BigPappy098/Satellite1-Ultra/reports/drawings/bottom_service_plate.pdf

# Satellite1 Ultra — bottom_service_plate

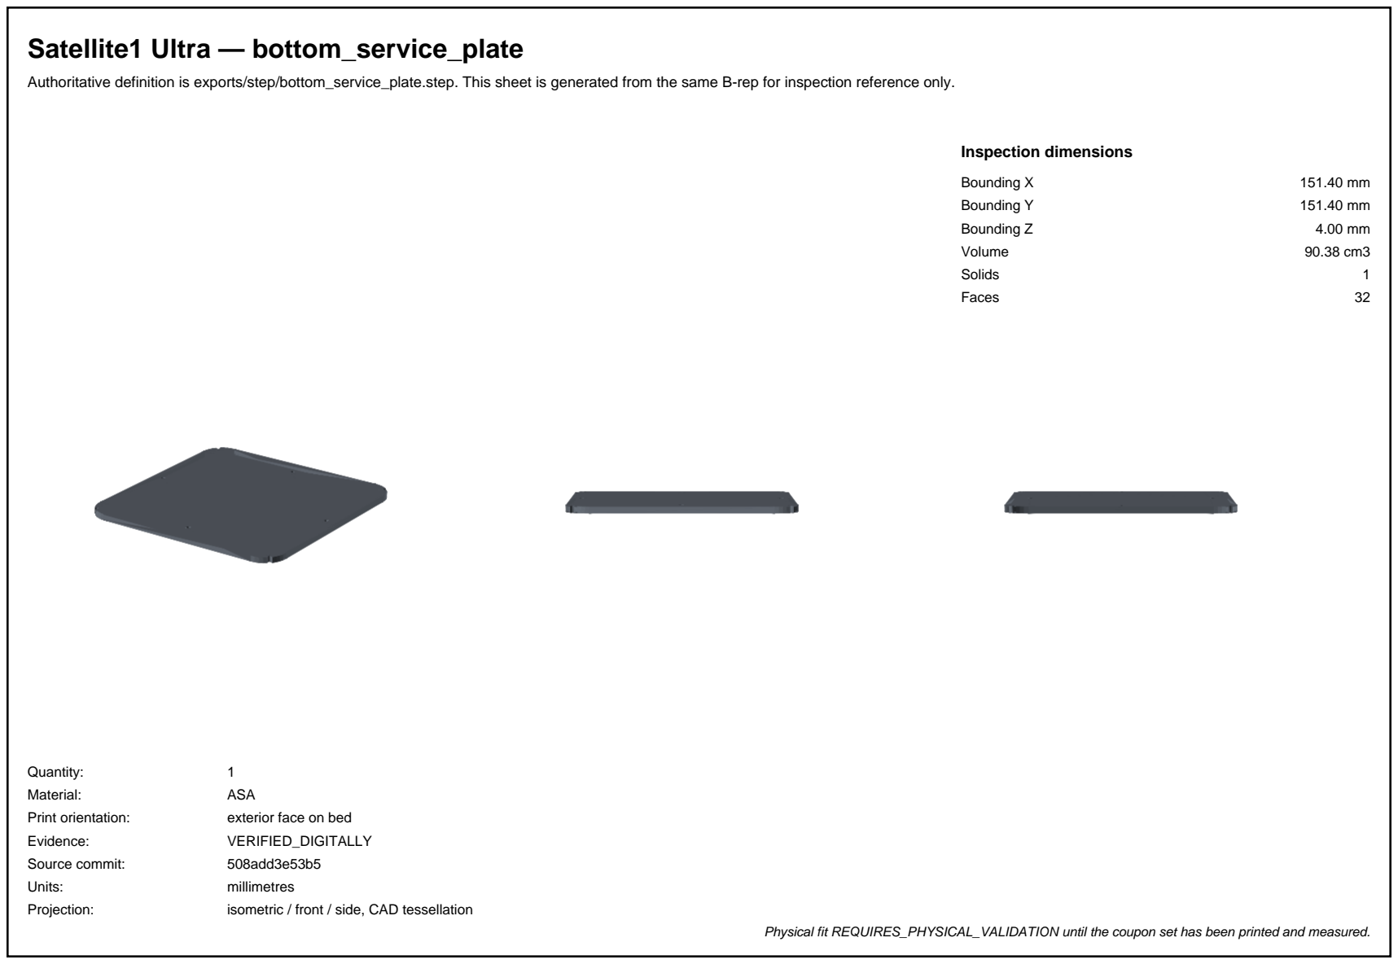
[picture p7: page 1]

Authoritative definition is exports/step/bottom_service_plate.step. This sheet is generated from the same B-rep for inspection reference only.

Inspection dimensions

Bounding X | 151.40 mm
Bounding Y | 151.40 mm
Bounding Z | 4.00 mm
Volume | 90.38 cm3
Solids | 1
Faces | 32
Quantity: | 1
Material: | ASA
Print orientation: | exterior face on bed
Evidence: | VERIFIED_DIGITALLY
Source commit: | 508add3e53b5
Units: | millimetres
Projection: | isometric / front / side, CAD tessellation
Physical fit REQUIRES_PHYSICAL_VALIDATION until the coupon set has been printed and measured.
