BigPappy098/Satellite1-Ultra/reports/drawings/cable_gland.pdf

# Satellite1 Ultra — cable_gland

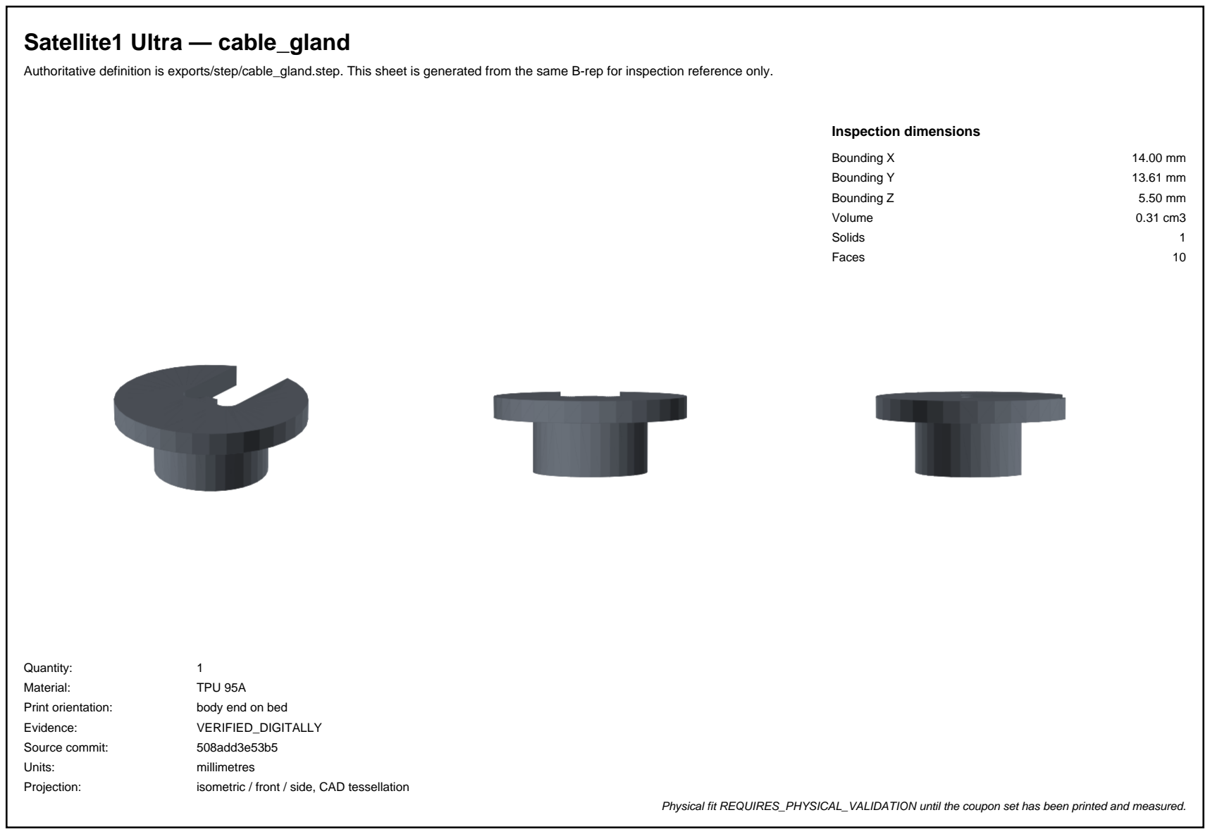
[picture p8: page 1]

Authoritative definition is exports/step/cable_gland.step. This sheet is generated from the same B-rep for inspection reference only.

Inspection dimensions

Bounding X | 14.00 mm
Bounding Y | 13.61 mm
Bounding Z | 5.50 mm
Volume | 0.31 cm3
Solids | 1
Faces | 10
Quantity: | 1
Material: | TPU 95A
Print orientation: | body end on bed
Evidence: | VERIFIED_DIGITALLY
Source commit: | 508add3e53b5
Units: | millimetres
Projection: | isometric / front / side, CAD tessellation
Physical fit REQUIRES_PHYSICAL_VALIDATION until the coupon set has been printed and measured.
