BigPappy098/Satellite1-Ultra/reports/drawings/coupon_active_driver.pdf

# Satellite1 Ultra — coupon_active_driver

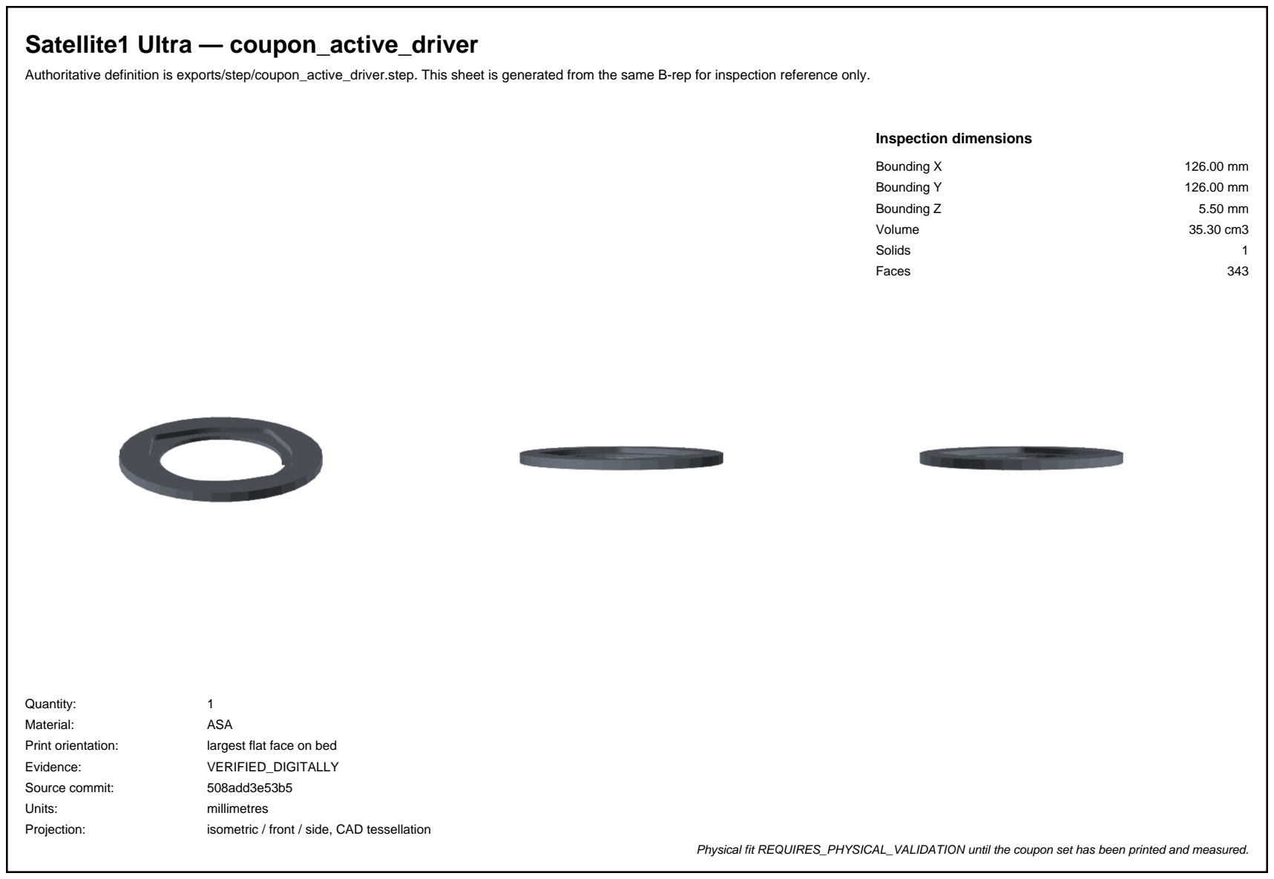
[picture p9: page 1]

Authoritative definition is exports/step/coupon_active_driver.step. This sheet is generated from the same B-rep for inspection reference only.

Inspection dimensions

Bounding X | 126.00 mm
Bounding Y | 126.00 mm
Bounding Z | 5.50 mm
Volume | 35.30 cm3
Solids | 1
Faces | 343
Quantity: | 1
Material: | ASA
Print orientation: | largest flat face on bed
Evidence: | VERIFIED_DIGITALLY
Source commit: | 508add3e53b5
Units: | millimetres
Projection: | isometric / front / side, CAD tessellation
Physical fit REQUIRES_PHYSICAL_VALIDATION until the coupon set has been printed and measured.
