BigPappy098/Satellite1-Ultra/reports/drawings/coupon_cable_passage.pdf

# Satellite1 Ultra — coupon_cable_passage

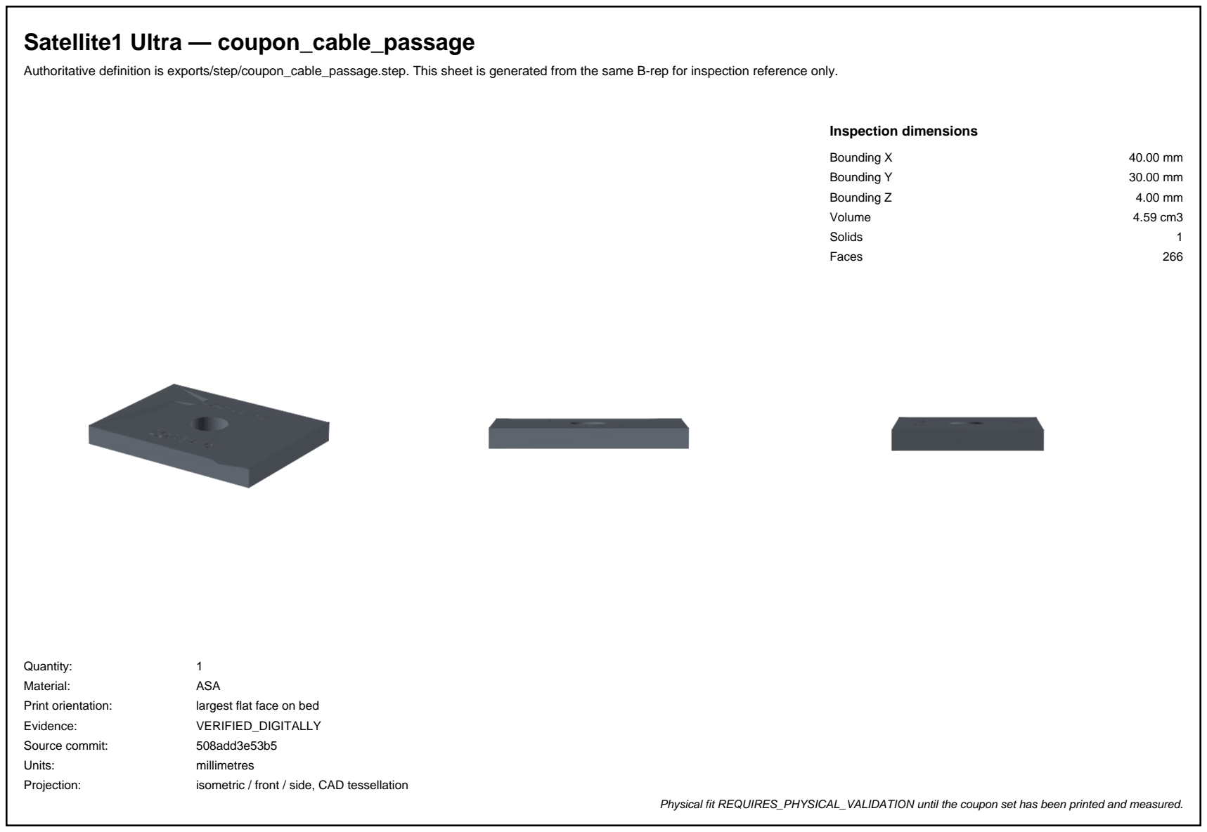
[picture p10: page 1]

Authoritative definition is exports/step/coupon_cable_passage.step. This sheet is generated from the same B-rep for inspection reference only.

Inspection dimensions

Bounding X | 40.00 mm
Bounding Y | 30.00 mm
Bounding Z | 4.00 mm
Volume | 4.59 cm3
Solids | 1
Faces | 266
Quantity: | 1
Material: | ASA
Print orientation: | largest flat face on bed
Evidence: | VERIFIED_DIGITALLY
Source commit: | 508add3e53b5
Units: | millimetres
Projection: | isometric / front / side, CAD tessellation
Physical fit REQUIRES_PHYSICAL_VALIDATION until the coupon set has been printed and measured.
