BigPappy098/Satellite1-Ultra/reports/drawings/coupon_gasket_base.pdf

# Satellite1 Ultra — coupon_gasket_base

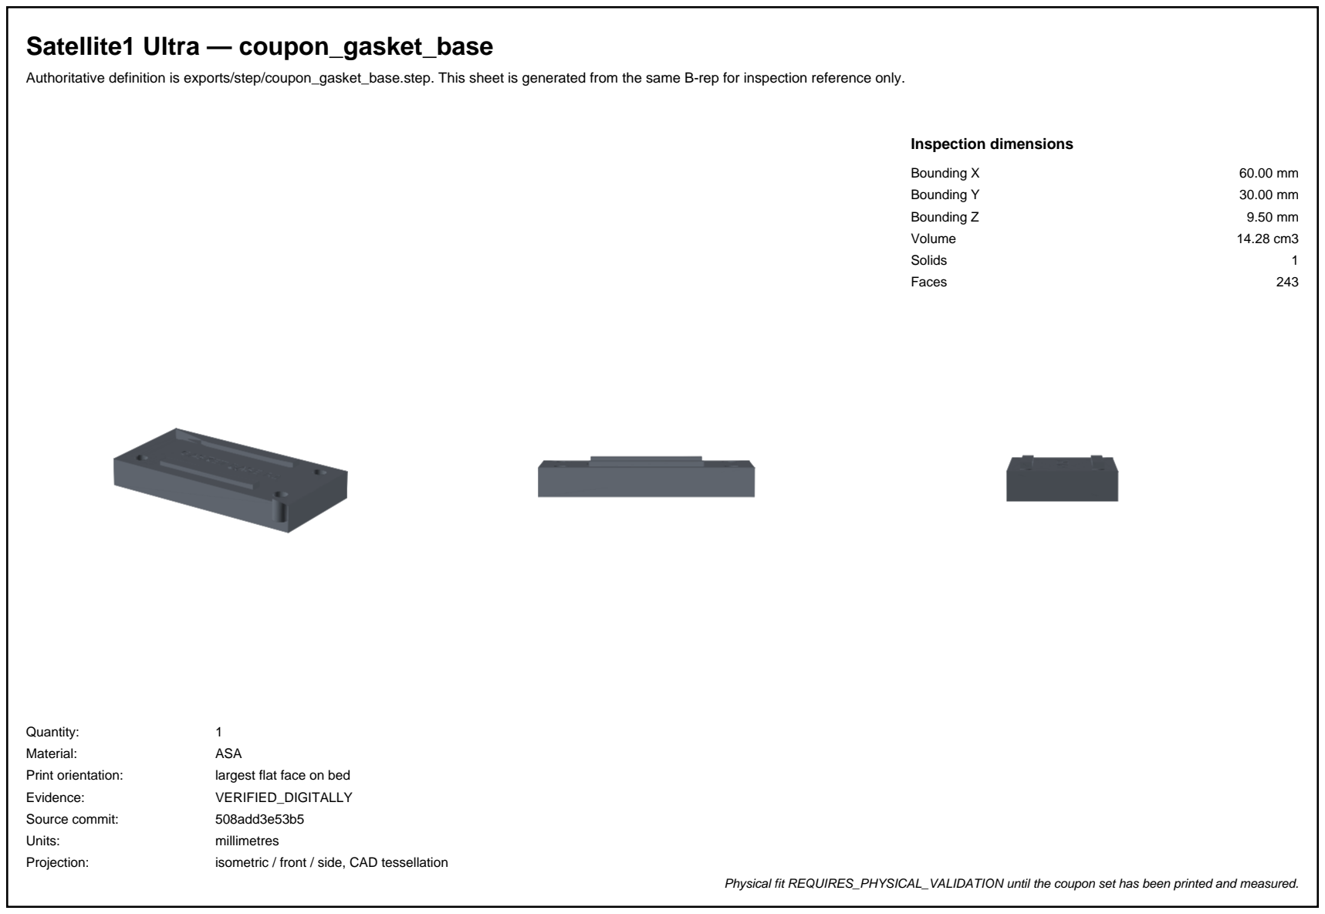
[picture p11: page 1]

Authoritative definition is exports/step/coupon_gasket_base.step. This sheet is generated from the same B-rep for inspection reference only.

Inspection dimensions

Bounding X | 60.00 mm
Bounding Y | 30.00 mm
Bounding Z | 9.50 mm
Volume | 14.28 cm3
Solids | 1
Faces | 243
Quantity: | 1
Material: | ASA
Print orientation: | largest flat face on bed
Evidence: | VERIFIED_DIGITALLY
Source commit: | 508add3e53b5
Units: | millimetres
Projection: | isometric / front / side, CAD tessellation
Physical fit REQUIRES_PHYSICAL_VALIDATION until the coupon set has been printed and measured.
