BigPappy098/Satellite1-Ultra/reports/drawings/coupon_heat_set_insert.pdf

# Satellite1 Ultra — coupon_heat_set_insert

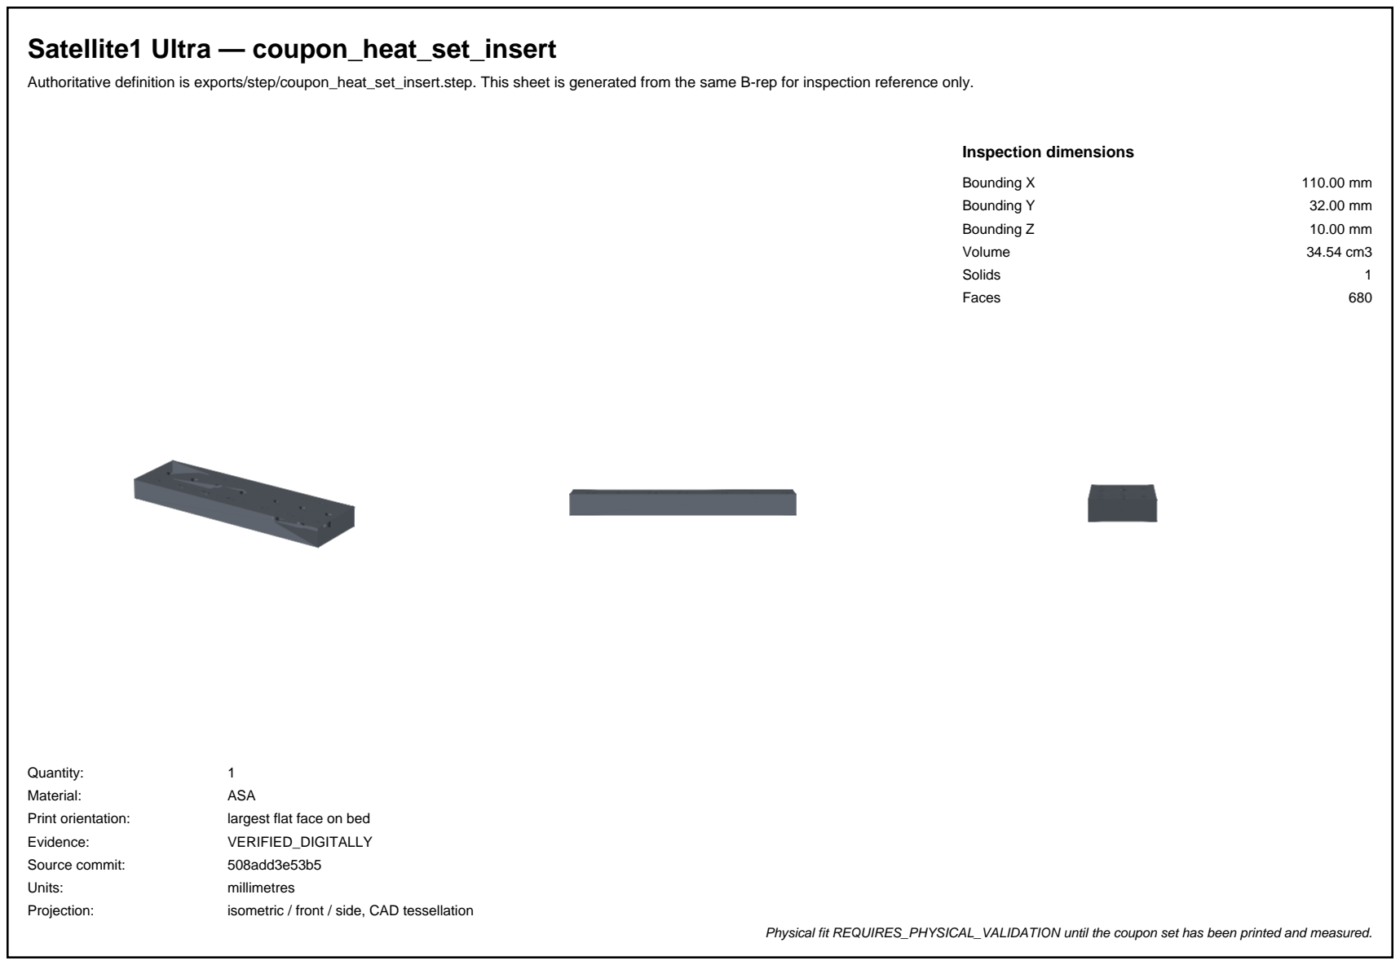
[picture p13: page 1]

Authoritative definition is exports/step/coupon_heat_set_insert.step. This sheet is generated from the same B-rep for inspection reference only.

Inspection dimensions

Bounding X | 110.00 mm
Bounding Y | 32.00 mm
Bounding Z | 10.00 mm
Volume | 34.54 cm3
Solids | 1
Faces | 680
Quantity: | 1
Material: | ASA
Print orientation: | largest flat face on bed
Evidence: | VERIFIED_DIGITALLY
Source commit: | 508add3e53b5
Units: | millimetres
Projection: | isometric / front / side, CAD tessellation
Physical fit REQUIRES_PHYSICAL_VALIDATION until the coupon set has been printed and measured.
