BigPappy098/Satellite1-Ultra/reports/drawings/coupon_official_interface.pdf

# Satellite1 Ultra — coupon_official_interface

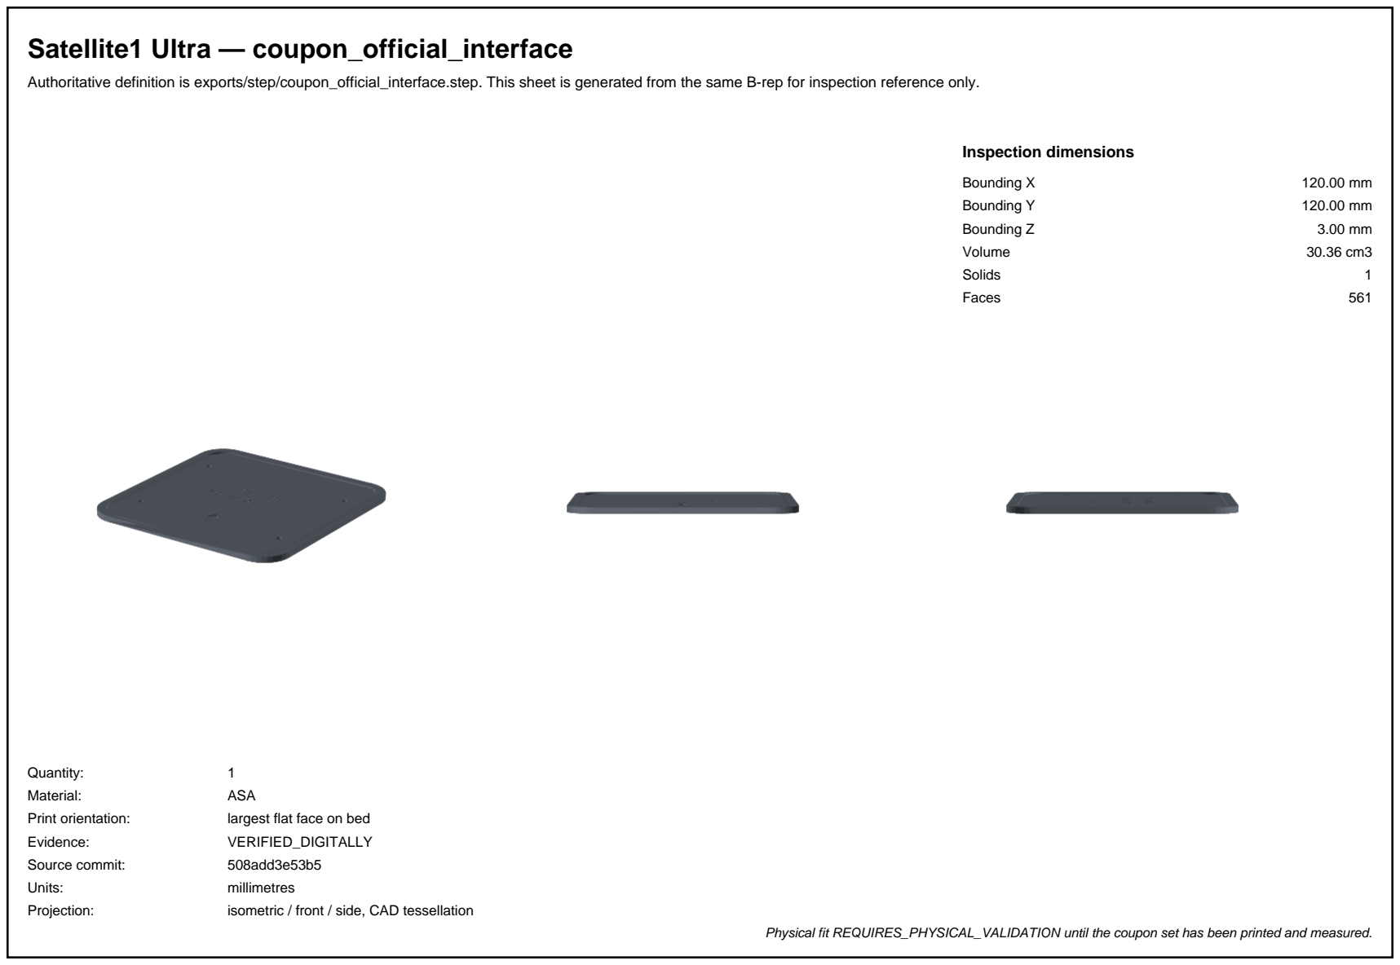
[picture p14: page 1]

Authoritative definition is exports/step/coupon_official_interface.step. This sheet is generated from the same B-rep for inspection reference only.

Inspection dimensions

Bounding X | 120.00 mm
Bounding Y | 120.00 mm
Bounding Z | 3.00 mm
Volume | 30.36 cm3
Solids | 1
Faces | 561
Quantity: | 1
Material: | ASA
Print orientation: | largest flat face on bed
Evidence: | VERIFIED_DIGITALLY
Source commit: | 508add3e53b5
Units: | millimetres
Projection: | isometric / front / side, CAD tessellation
Physical fit REQUIRES_PHYSICAL_VALIDATION until the coupon set has been printed and measured.
