BigPappy098/Satellite1-Ultra/reports/drawings/coupon_passive_radiator.pdf

# Satellite1 Ultra — coupon_passive_radiator

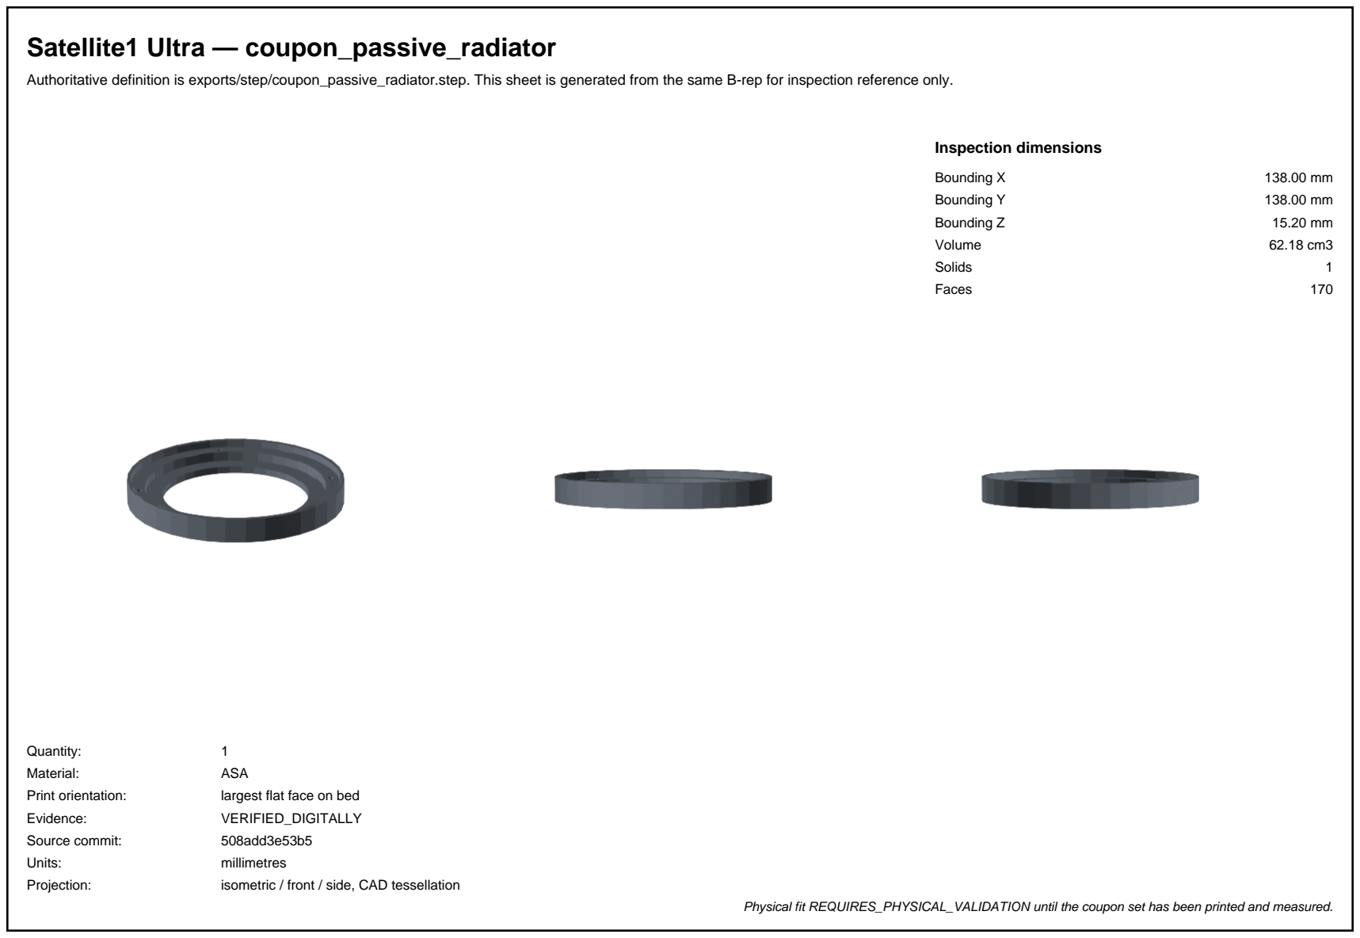
[picture p15: page 1]

Authoritative definition is exports/step/coupon_passive_radiator.step. This sheet is generated from the same B-rep for inspection reference only.

Inspection dimensions

Bounding X | 138.00 mm
Bounding Y | 138.00 mm
Bounding Z | 15.20 mm
Volume | 62.18 cm3
Solids | 1
Faces | 170
Quantity: | 1
Material: | ASA
Print orientation: | largest flat face on bed
Evidence: | VERIFIED_DIGITALLY
Source commit: | 508add3e53b5
Units: | millimetres
Projection: | isometric / front / side, CAD tessellation
Physical fit REQUIRES_PHYSICAL_VALIDATION until the coupon set has been printed and measured.
