BigPappy098/Satellite1-Ultra/reports/drawings/divider_gasket.pdf

# Satellite1 Ultra — divider_gasket

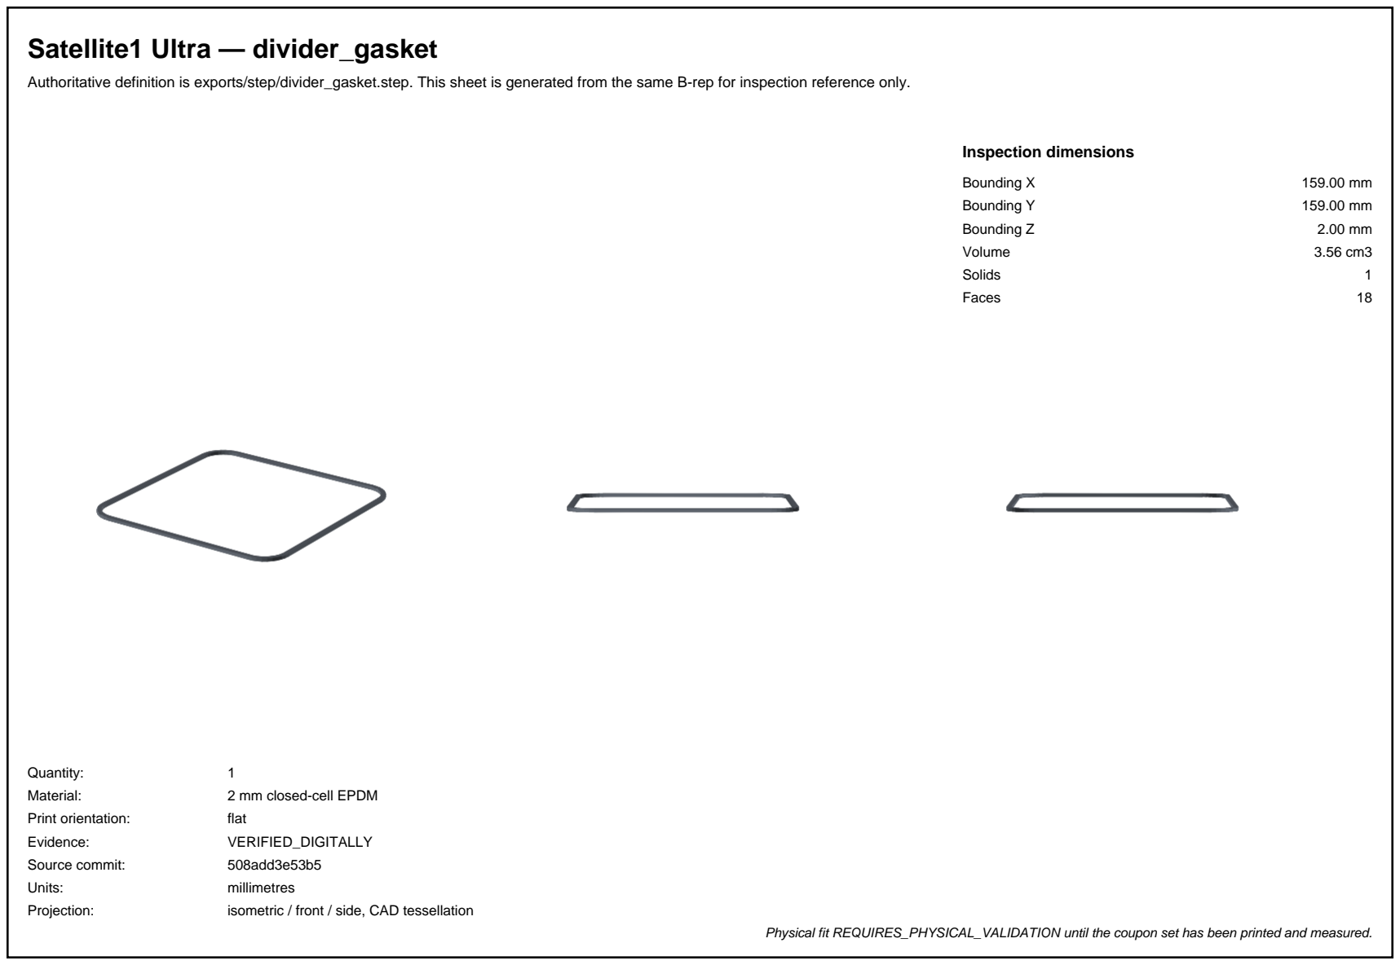
[picture p16: page 1]

Authoritative definition is exports/step/divider_gasket.step. This sheet is generated from the same B-rep for inspection reference only.

Inspection dimensions

Bounding X | 159.00 mm
Bounding Y | 159.00 mm
Bounding Z | 2.00 mm
Volume | 3.56 cm3
Solids | 1
Faces | 18
Quantity: | 1
Material: | 2 mm closed-cell EPDM
Print orientation: | flat
Evidence: | VERIFIED_DIGITALLY
Source commit: | 508add3e53b5
Units: | millimetres
Projection: | isometric / front / side, CAD tessellation
Physical fit REQUIRES_PHYSICAL_VALIDATION until the coupon set has been printed and measured.
