BigPappy098/Satellite1-Ultra/reports/drawings/driver_gasket.pdf

# Satellite1 Ultra — driver_gasket

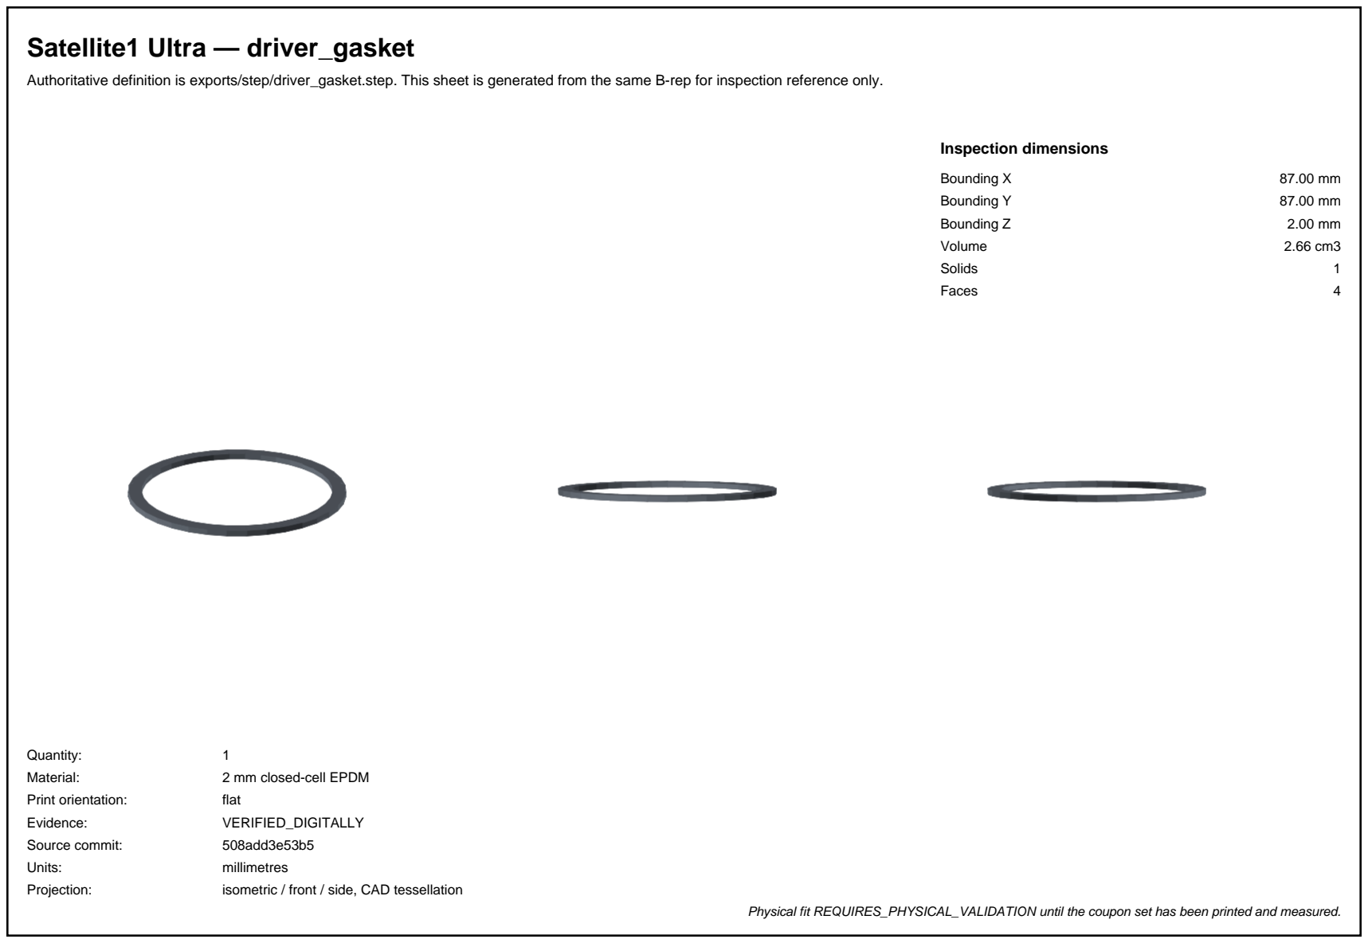
[picture p17: page 1]

Authoritative definition is exports/step/driver_gasket.step. This sheet is generated from the same B-rep for inspection reference only.

Inspection dimensions

Bounding X | 87.00 mm
Bounding Y | 87.00 mm
Bounding Z | 2.00 mm
Volume | 2.66 cm3
Solids | 1
Faces | 4
Quantity: | 1
Material: | 2 mm closed-cell EPDM
Print orientation: | flat
Evidence: | VERIFIED_DIGITALLY
Source commit: | 508add3e53b5
Units: | millimetres
Projection: | isometric / front / side, CAD tessellation
Physical fit REQUIRES_PHYSICAL_VALIDATION until the coupon set has been printed and measured.
