BigPappy098/Satellite1-Ultra/reports/drawings/main_cabinet.pdf

# Satellite1 Ultra — main_cabinet

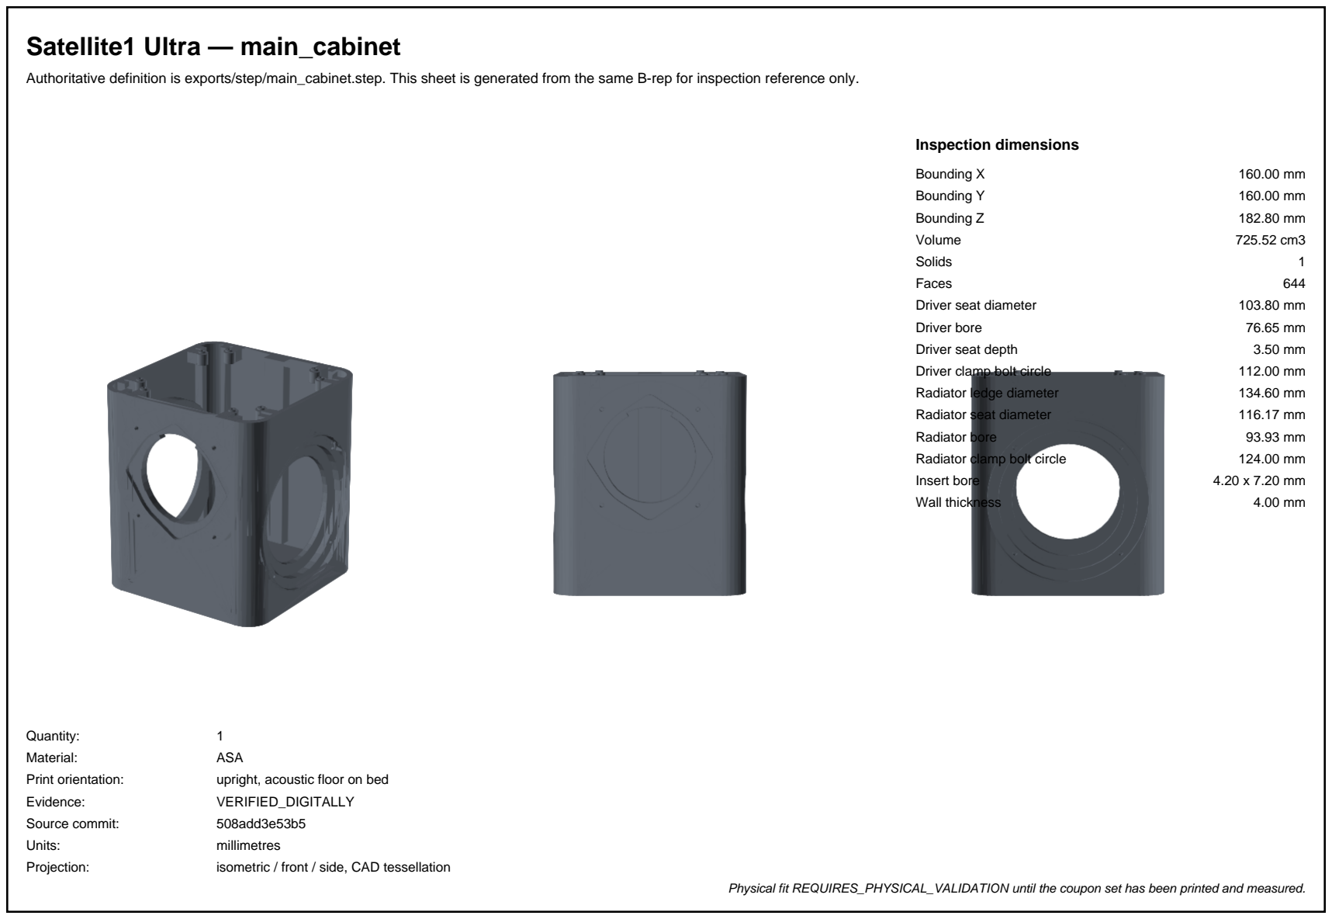
[picture p18: page 1]

Authoritative definition is exports/step/main_cabinet.step. This sheet is generated from the same B-rep for inspection reference only.

Inspection dimensions

Bounding X | 160.00 mm
Bounding Y | 160.00 mm
Bounding Z | 182.80 mm
Volume | 725.52 cm3
Solids | 1
Faces | 644
Driver seat diameter | 103.80 mm
Driver bore | 76.65 mm
Driver seat depth | 3.50 mm
Driver clamp bolt circle | 112.00 mm
Radiator ledge diameter | 134.60 mm
Radiator seat diameter | 116.17 mm
Radiator bore | 93.93 mm
Radiator clamp bolt circle | 124.00 mm
Insert bore | 4.20 x 7.20 mm
Wall thickness | 4.00 mm
Quantity: | 1
Material: | ASA
Print orientation: | upright, acoustic floor on bed
Evidence: | VERIFIED_DIGITALLY
Source commit: | 508add3e53b5
Units: | millimetres
Projection: | isometric / front / side, CAD tessellation
Physical fit REQUIRES_PHYSICAL_VALIDATION until the coupon set has been printed and measured.
