BigPappy098/Satellite1-Ultra/reports/drawings/mic_isolation_bushing.pdf

# Satellite1 Ultra — mic_isolation_bushing

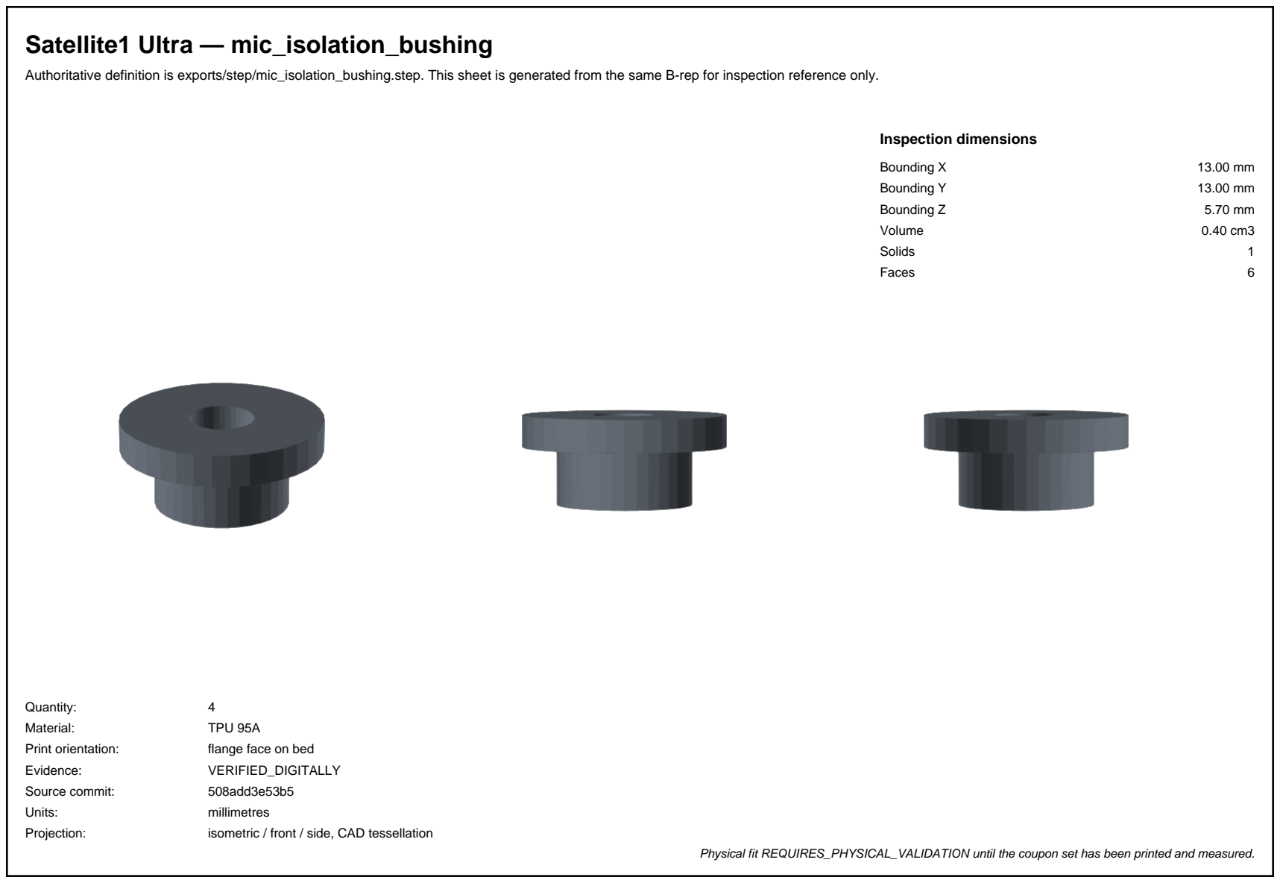
[picture p19: page 1]

Authoritative definition is exports/step/mic_isolation_bushing.step. This sheet is generated from the same B-rep for inspection reference only.

Inspection dimensions

Bounding X | 13.00 mm
Bounding Y | 13.00 mm
Bounding Z | 5.70 mm
Volume | 0.40 cm3
Solids | 1
Faces | 6
Quantity: | 4
Material: | TPU 95A
Print orientation: | flange face on bed
Evidence: | VERIFIED_DIGITALLY
Source commit: | 508add3e53b5
Units: | millimetres
Projection: | isometric / front / side, CAD tessellation
Physical fit REQUIRES_PHYSICAL_VALIDATION until the coupon set has been printed and measured.
