BigPappy098/Satellite1-Ultra/reports/drawings/passive_radiator_clamp_ring.pdf

# Satellite1 Ultra — passive_radiator_clamp_ring

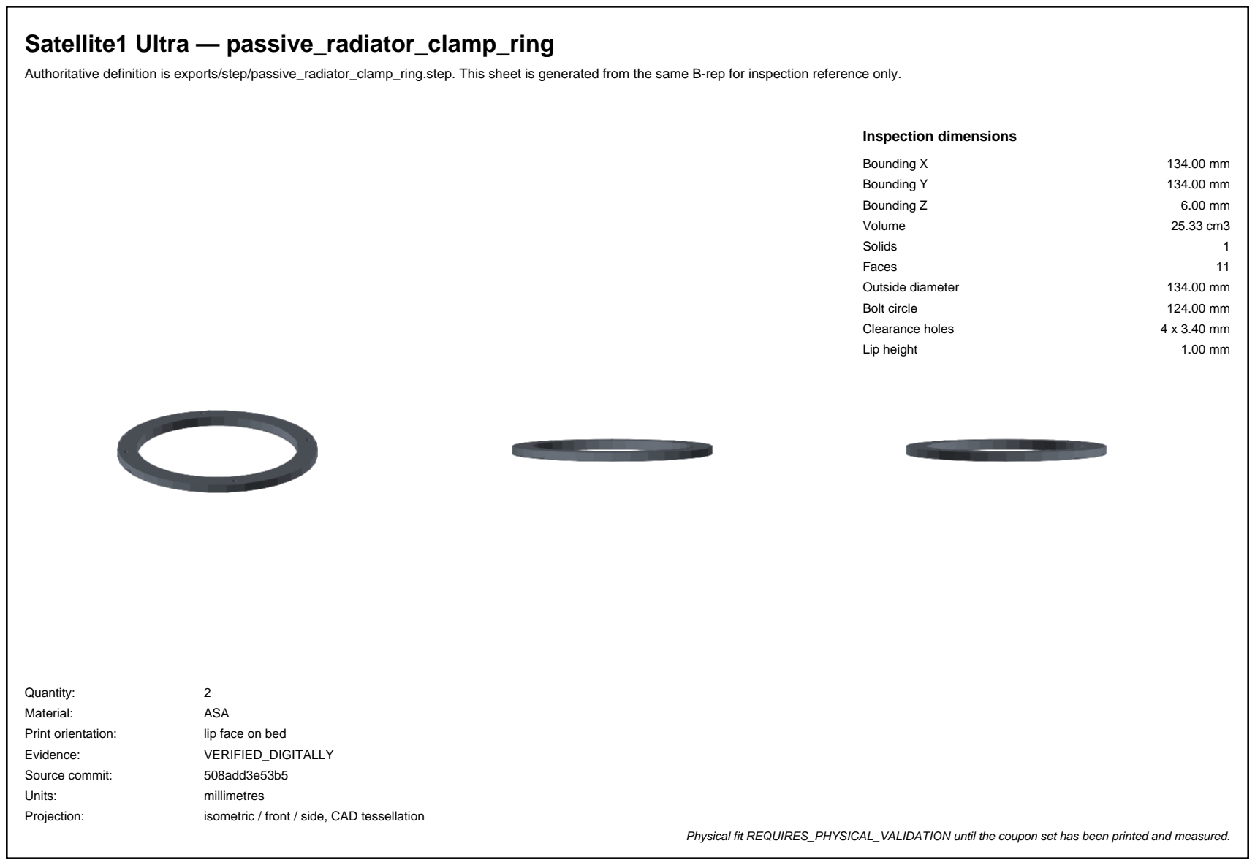
[picture p20: page 1]

Authoritative definition is exports/step/passive_radiator_clamp_ring.step. This sheet is generated from the same B-rep for inspection reference only.

Inspection dimensions

Bounding X | 134.00 mm
Bounding Y | 134.00 mm
Bounding Z | 6.00 mm
Volume | 25.33 cm3
Solids | 1
Faces | 11
Outside diameter | 134.00 mm
Bolt circle | 124.00 mm
Clearance holes | 4 x 3.40 mm
Lip height | 1.00 mm
Quantity: | 2
Material: | ASA
Print orientation: | lip face on bed
Evidence: | VERIFIED_DIGITALLY
Source commit: | 508add3e53b5
Units: | millimetres
Projection: | isometric / front / side, CAD tessellation
Physical fit REQUIRES_PHYSICAL_VALIDATION until the coupon set has been printed and measured.
