BigPappy098/Satellite1-Ultra/reports/drawings/passive_radiator_gasket.pdf

# Satellite1 Ultra — passive_radiator_gasket

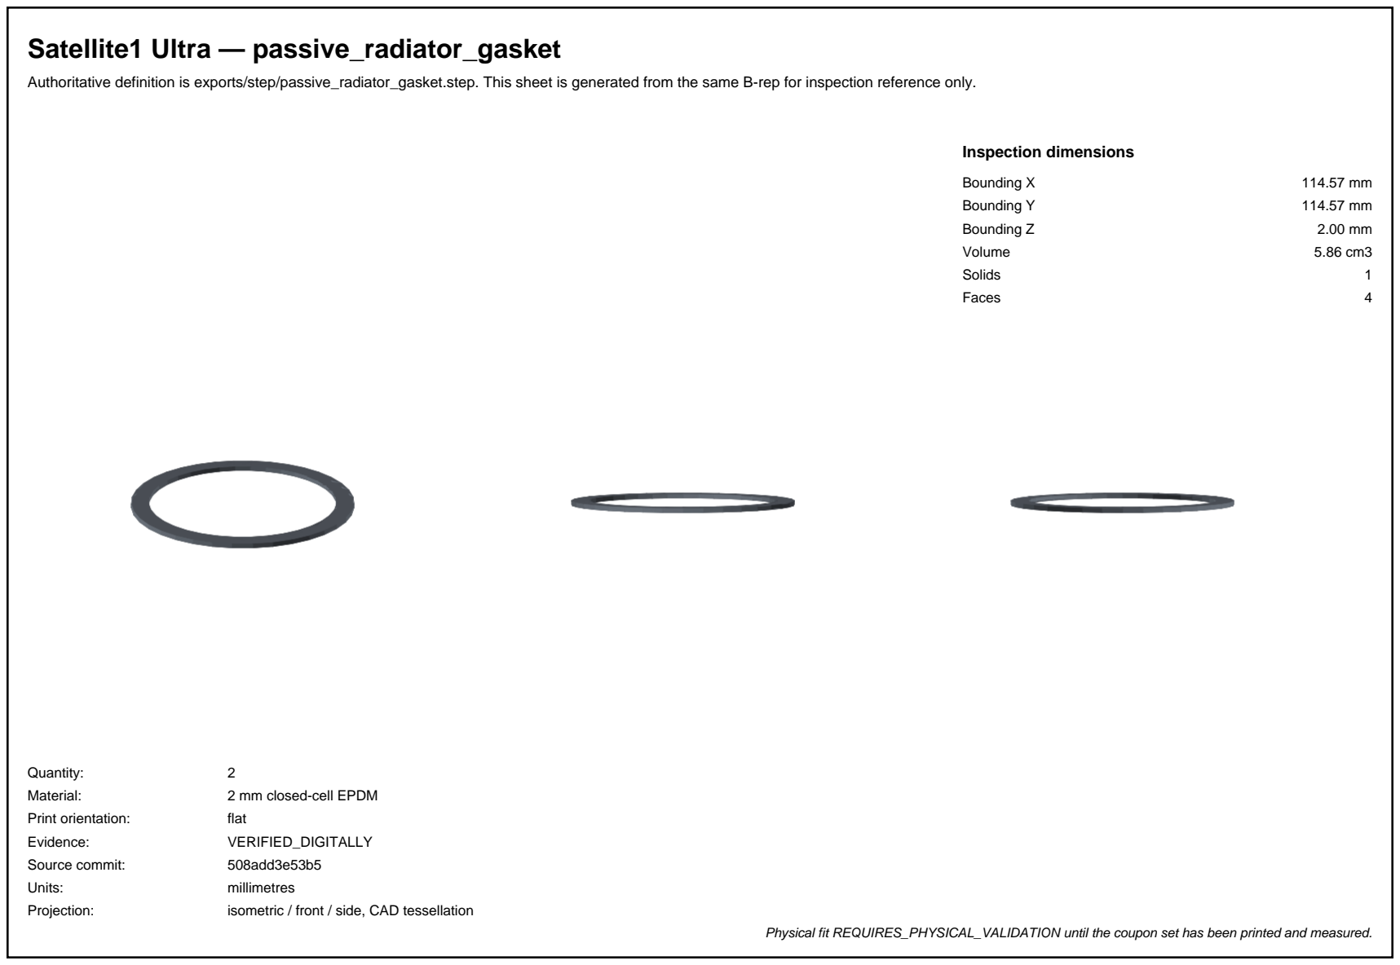
[picture p21: page 1]

Authoritative definition is exports/step/passive_radiator_gasket.step. This sheet is generated from the same B-rep for inspection reference only.

Inspection dimensions

Bounding X | 114.57 mm
Bounding Y | 114.57 mm
Bounding Z | 2.00 mm
Volume | 5.86 cm3
Solids | 1
Faces | 4
Quantity: | 2
Material: | 2 mm closed-cell EPDM
Print orientation: | flat
Evidence: | VERIFIED_DIGITALLY
Source commit: | 508add3e53b5
Units: | millimetres
Projection: | isometric / front / side, CAD tessellation
Physical fit REQUIRES_PHYSICAL_VALIDATION until the coupon set has been printed and measured.
