BigPappy098/Satellite1-Ultra/reports/drawings/pressure_divider.pdf

# Satellite1 Ultra — pressure_divider

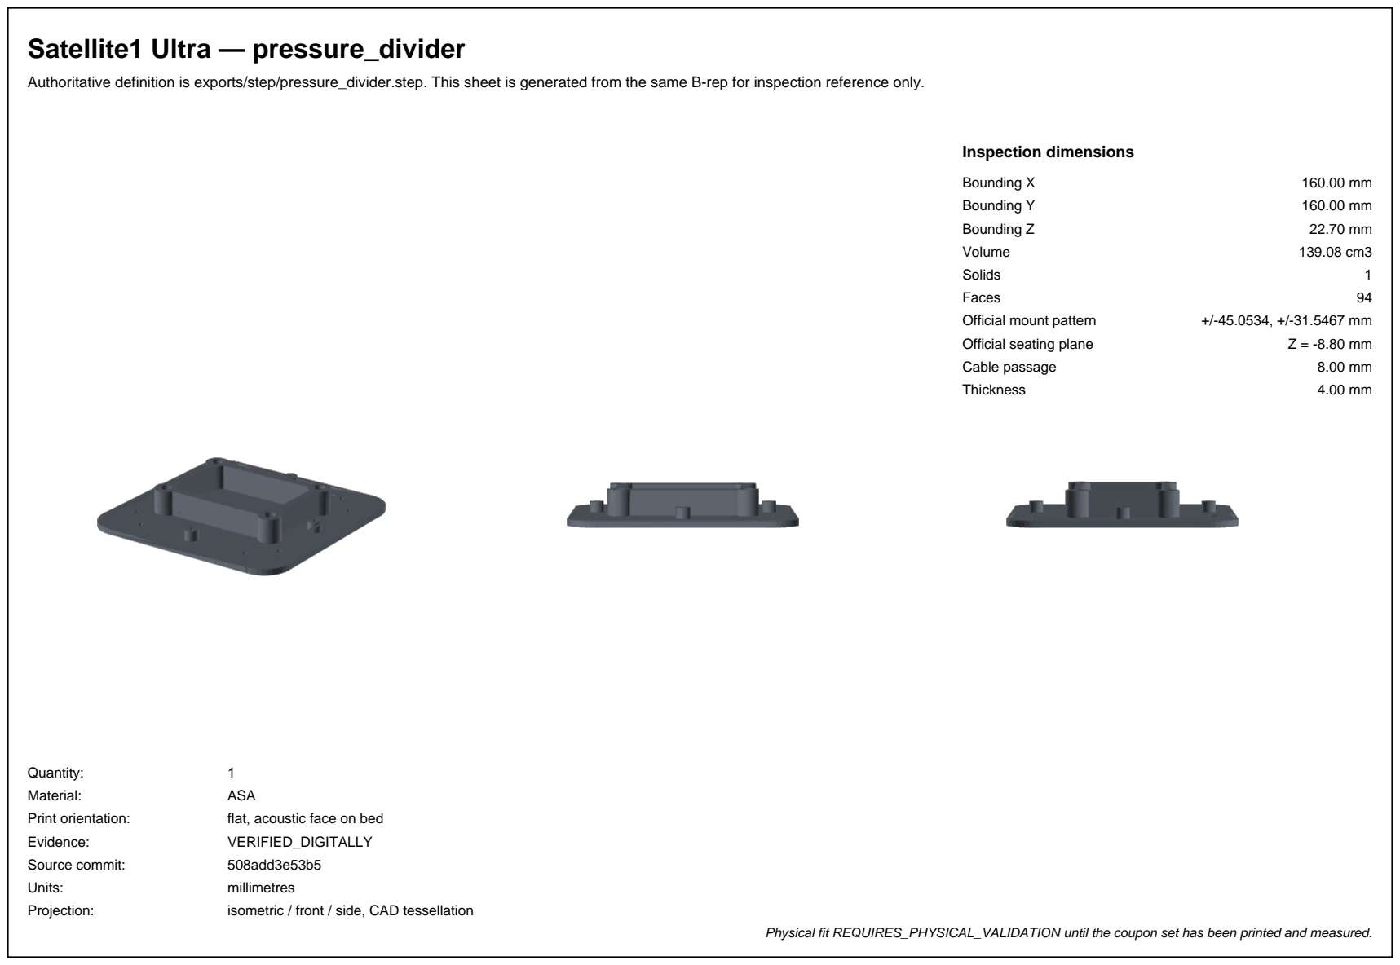
[picture p22: page 1]

Authoritative definition is exports/step/pressure_divider.step. This sheet is generated from the same B-rep for inspection reference only.

Inspection dimensions

Bounding X | 160.00 mm
Bounding Y | 160.00 mm
Bounding Z | 22.70 mm
Volume | 139.08 cm3
Solids | 1
Faces | 94
Official mount pattern | +/-45.0534, +/-31.5467 mm
Official seating plane | Z = -8.80 mm
Cable passage | 8.00 mm
Thickness | 4.00 mm
Quantity: | 1
Material: | ASA
Print orientation: | flat, acoustic face on bed
Evidence: | VERIFIED_DIGITALLY
Source commit: | 508add3e53b5
Units: | millimetres
Projection: | isometric / front / side, CAD tessellation
Physical fit REQUIRES_PHYSICAL_VALIDATION until the coupon set has been printed and measured.
