BigPappy098/Satellite1-Ultra/reports/drawings/shell_base.pdf

# Satellite1 Ultra — shell_base

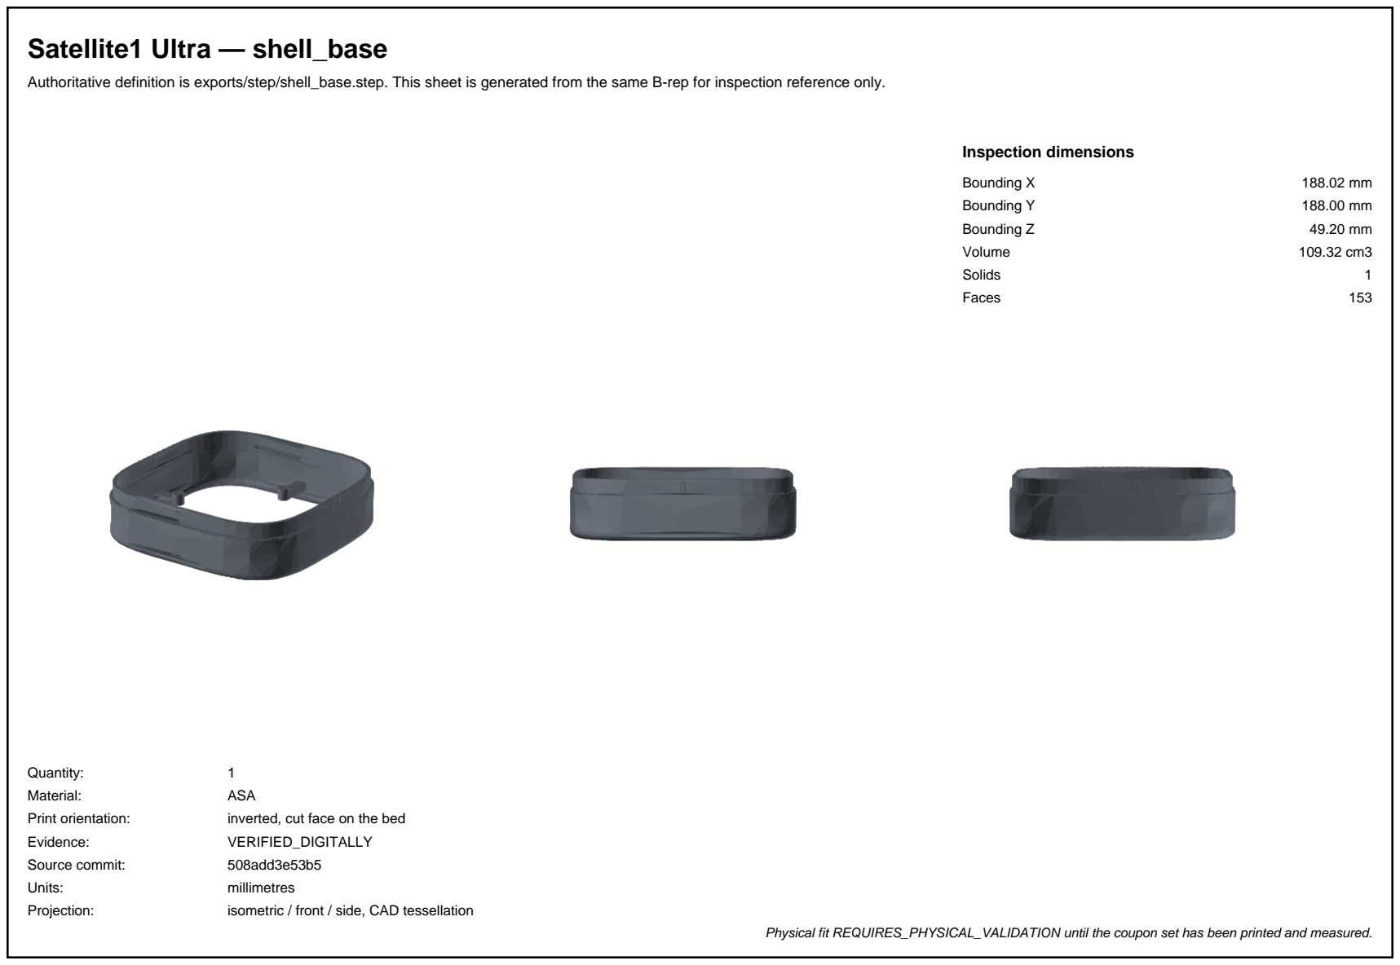
[picture p23: page 1]

Authoritative definition is exports/step/shell_base.step. This sheet is generated from the same B-rep for inspection reference only.

Inspection dimensions

Bounding X | 188.02 mm
Bounding Y | 188.00 mm
Bounding Z | 49.20 mm
Volume | 109.32 cm3
Solids | 1
Faces | 153
Quantity: | 1
Material: | ASA
Print orientation: | inverted, cut face on the bed
Evidence: | VERIFIED_DIGITALLY
Source commit: | 508add3e53b5
Units: | millimetres
Projection: | isometric / front / side, CAD tessellation
Physical fit REQUIRES_PHYSICAL_VALIDATION until the coupon set has been printed and measured.
