BigPappy098/Satellite1-Ultra/reports/drawings/shell_crown_fabric.pdf

# Satellite1 Ultra — shell_crown_fabric

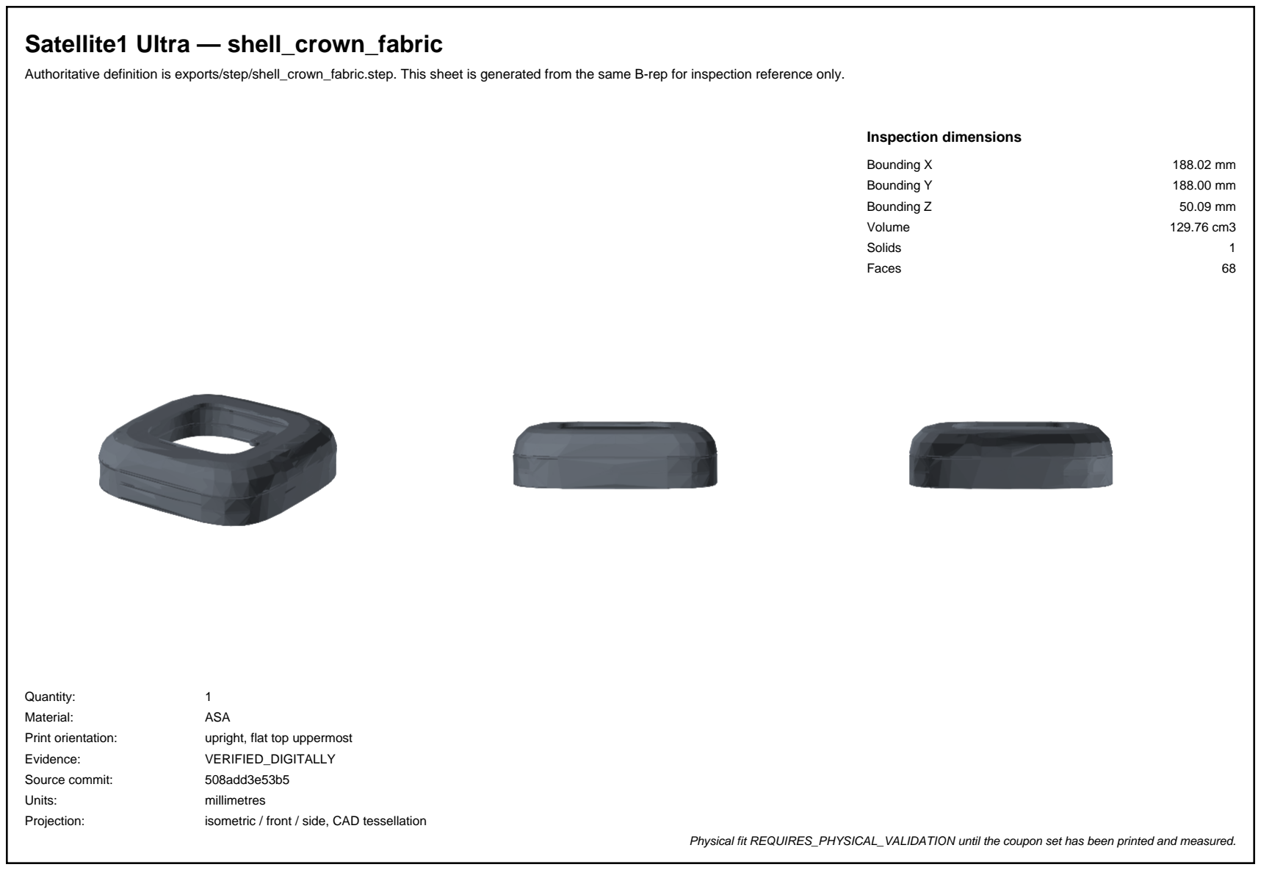
[picture p25: page 1]

Authoritative definition is exports/step/shell_crown_fabric.step. This sheet is generated from the same B-rep for inspection reference only.

Inspection dimensions

Bounding X | 188.02 mm
Bounding Y | 188.00 mm
Bounding Z | 50.09 mm
Volume | 129.76 cm3
Solids | 1
Faces | 68
Quantity: | 1
Material: | ASA
Print orientation: | upright, flat top uppermost
Evidence: | VERIFIED_DIGITALLY
Source commit: | 508add3e53b5
Units: | millimetres
Projection: | isometric / front / side, CAD tessellation
Physical fit REQUIRES_PHYSICAL_VALIDATION until the coupon set has been printed and measured.
