BigPappy098/Satellite1-Ultra/release/Satellite1-Ultra-RC1/ADVANCED/IMAGES/cross_section_xz.png

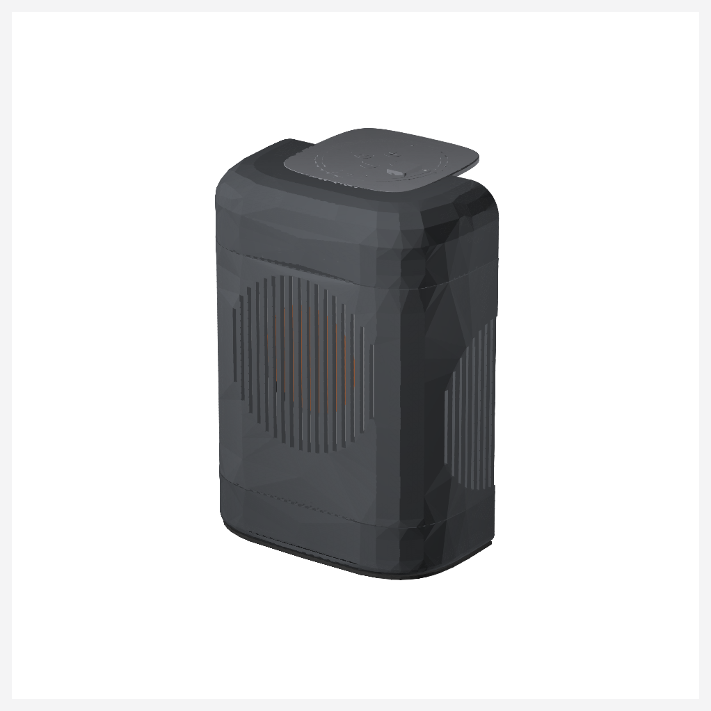
release/Satellite1-Ultra-RC1/ADVANCED/IMAGES/cross_section_xz.png
