BigPappy098/Satellite1-Ultra/release/Satellite1-Ultra-RC1/ADVANCED/IMAGES/cross_section_yz.png

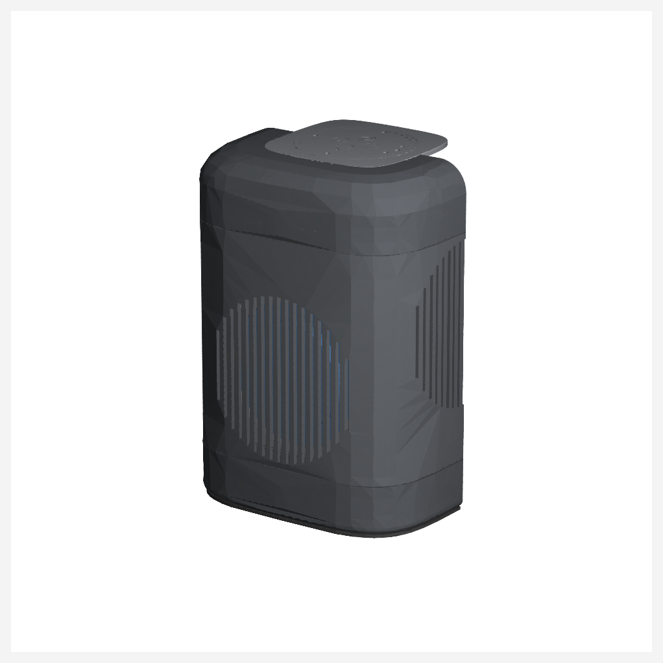
release/Satellite1-Ultra-RC1/ADVANCED/IMAGES/cross_section_yz.png
