BigPappy098/Satellite1-Ultra/release/Satellite1-Ultra-RC1/ADVANCED/IMAGES/gasket_placement.png

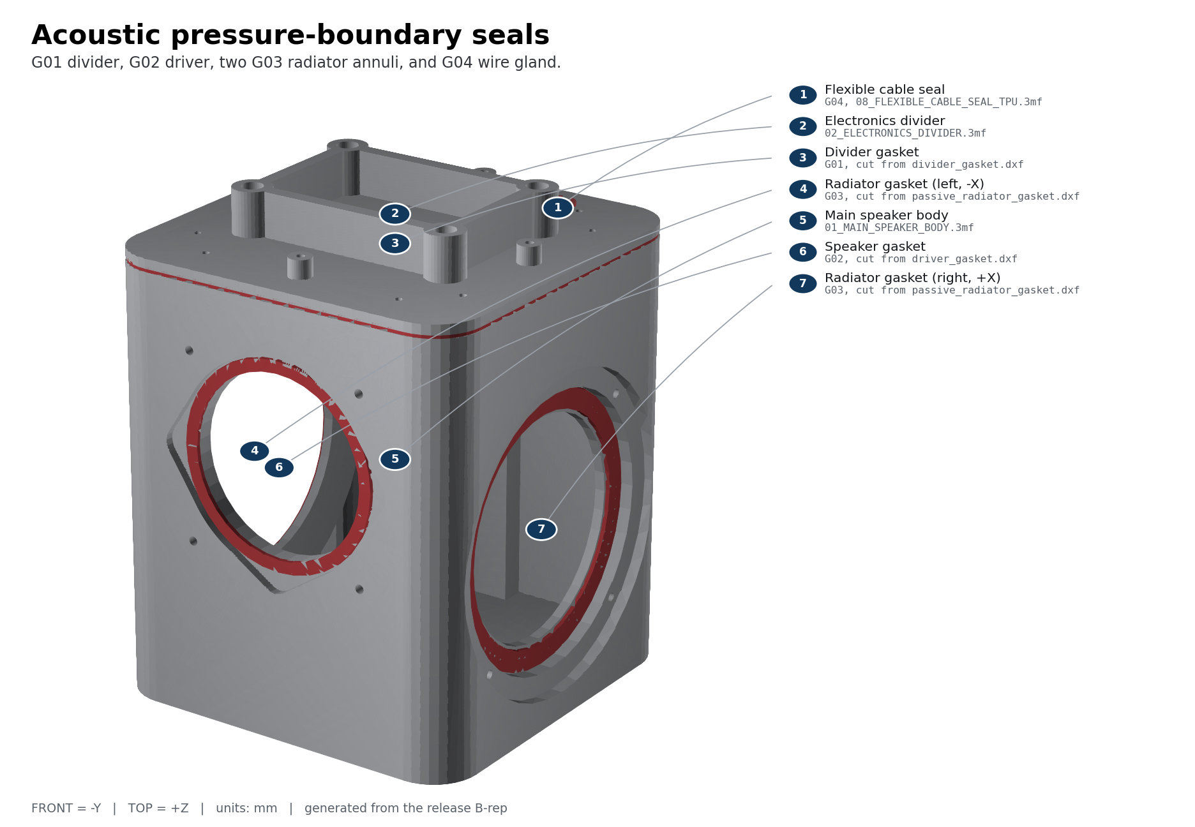
release/Satellite1-Ultra-RC1/ADVANCED/IMAGES/gasket_placement.png
