BigPappy098/Satellite1-Ultra/release/Satellite1-Ultra-RC1/ADVANCED/IMAGES/part_sheet.png

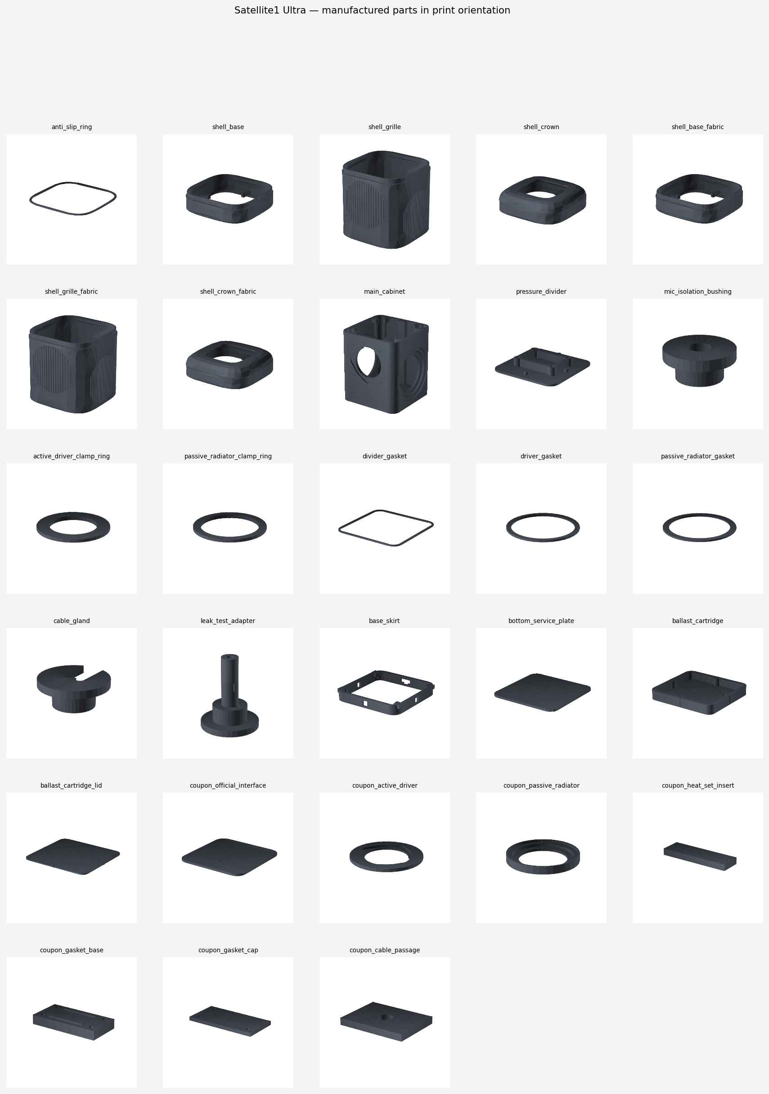
release/Satellite1-Ultra-RC1/ADVANCED/IMAGES/part_sheet.png
