BigPappy098/Satellite1-Ultra/release/Satellite1-Ultra-RC1/ADVANCED/IMAGES/product_front.png

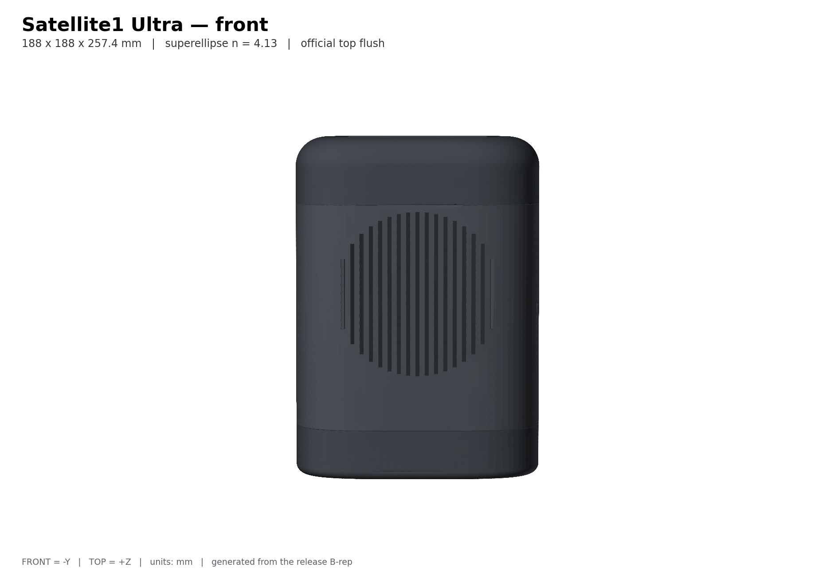
release/Satellite1-Ultra-RC1/ADVANCED/IMAGES/product_front.png
