BigPappy098/Satellite1-Ultra/release/Satellite1-Ultra-RC1/ADVANCED/IMAGES/wall_thickness_sections.png

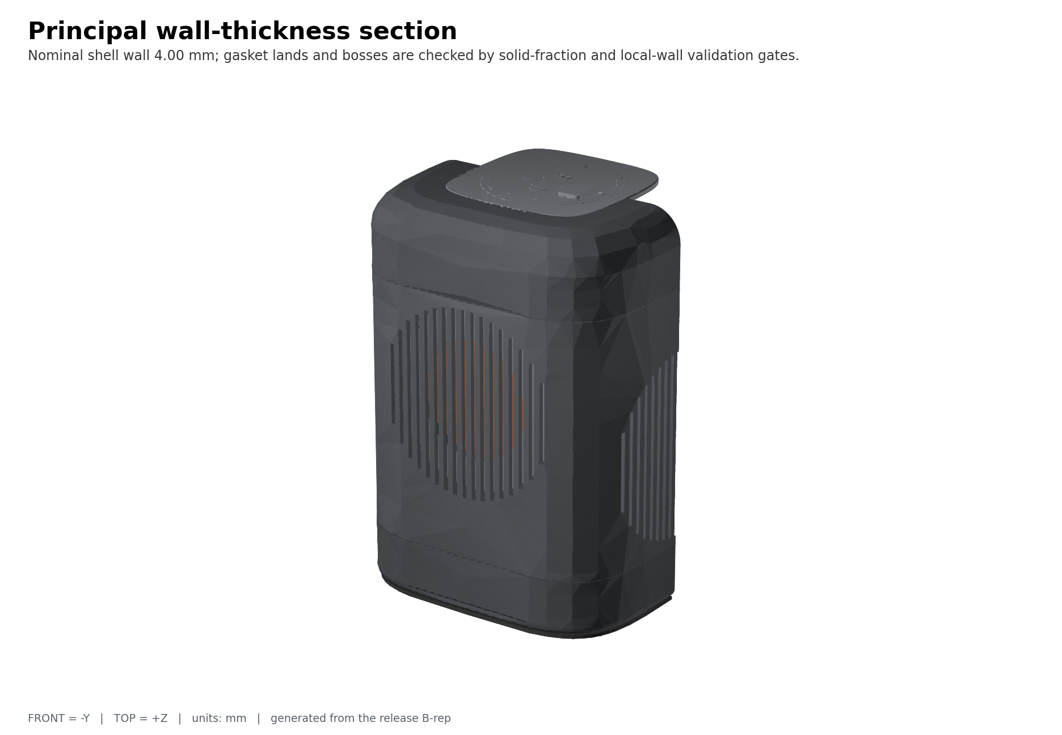
release/Satellite1-Ultra-RC1/ADVANCED/IMAGES/wall_thickness_sections.png
