BigPappy098/Satellite1-Ultra/reports/acoustics/sensitivity.png

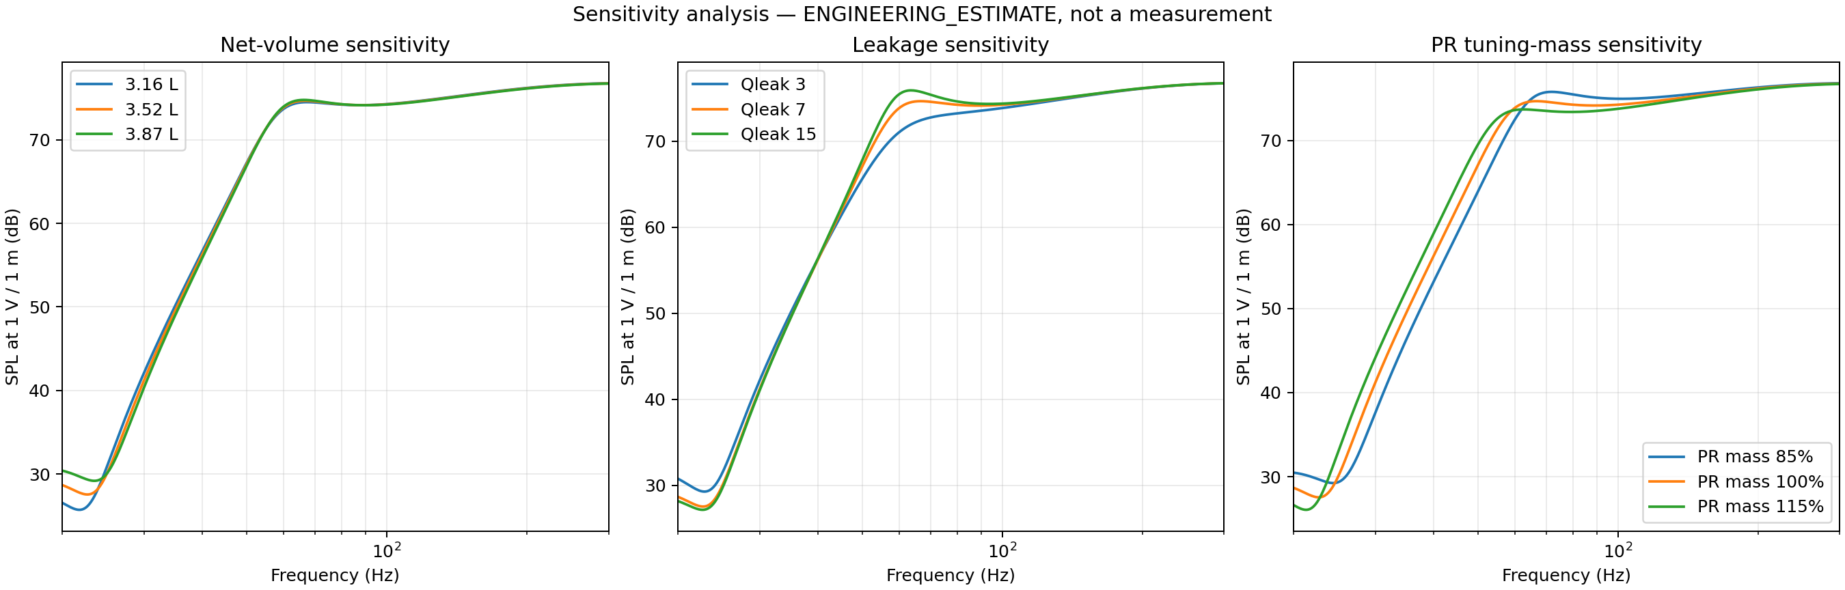
reports/acoustics/sensitivity.png
