BigPappy098/Satellite1-Ultra/reports/acoustics/system_response.png

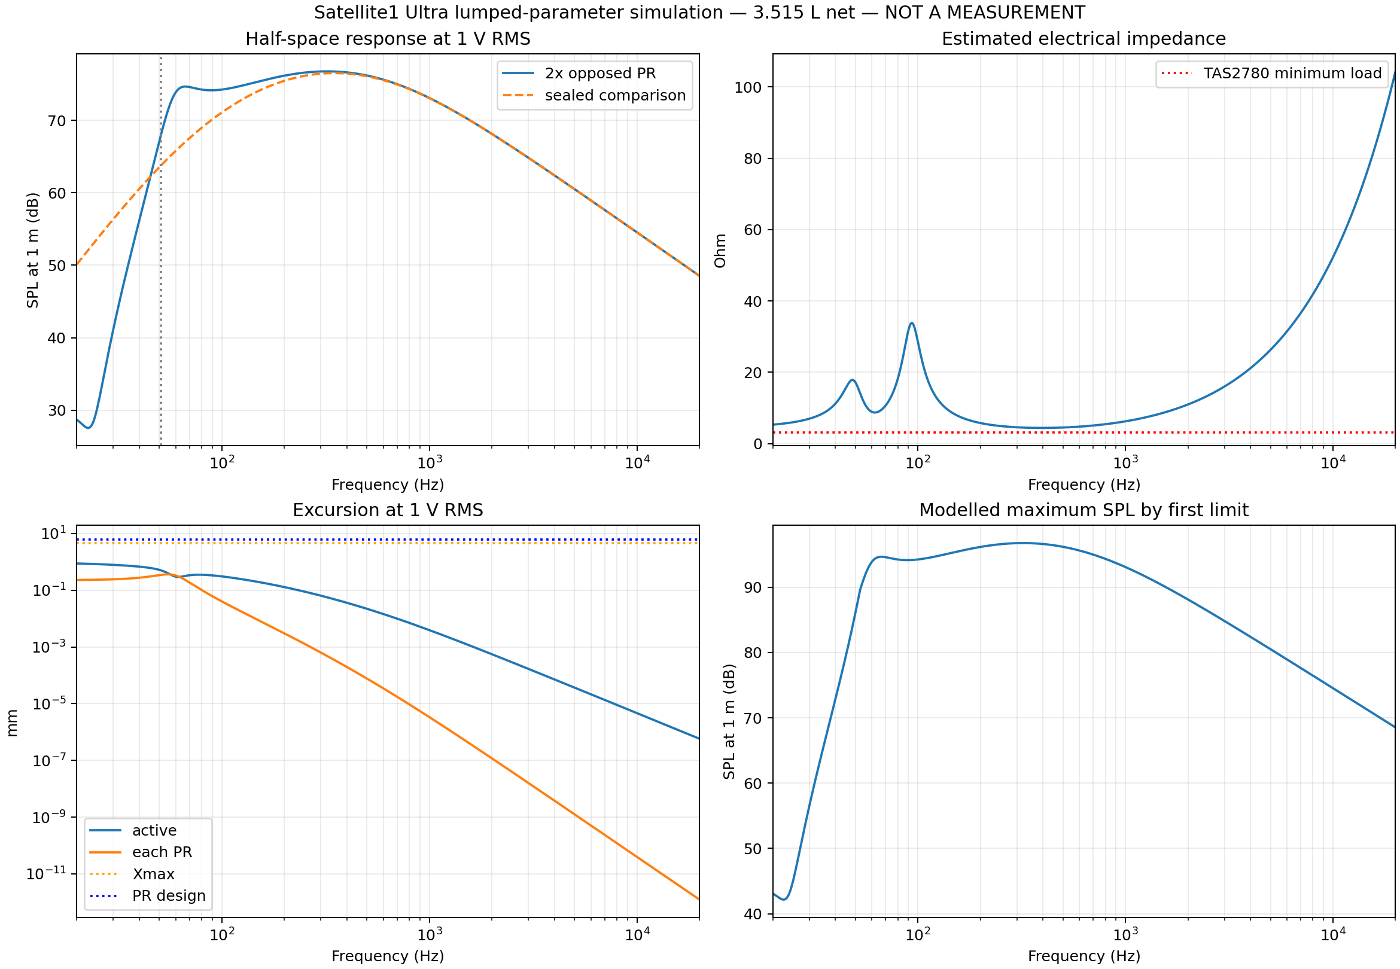
reports/acoustics/system_response.png
