BigPappy098/Satellite1-Ultra/reports/drawings/views/active_driver_clamp_ring_front.png

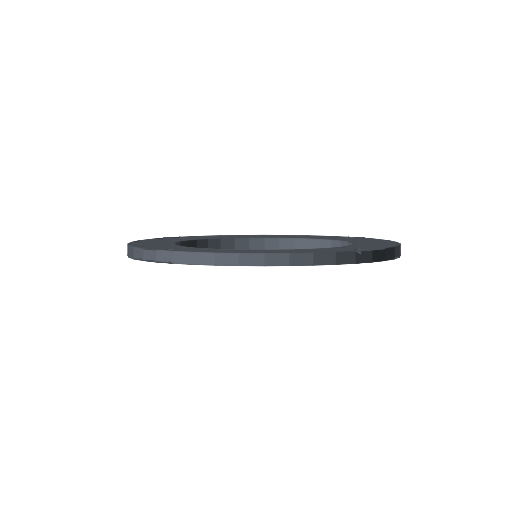
reports/drawings/views/active_driver_clamp_ring_front.png
