BigPappy098/Satellite1-Ultra/reports/drawings/views/anti_slip_ring_iso.png

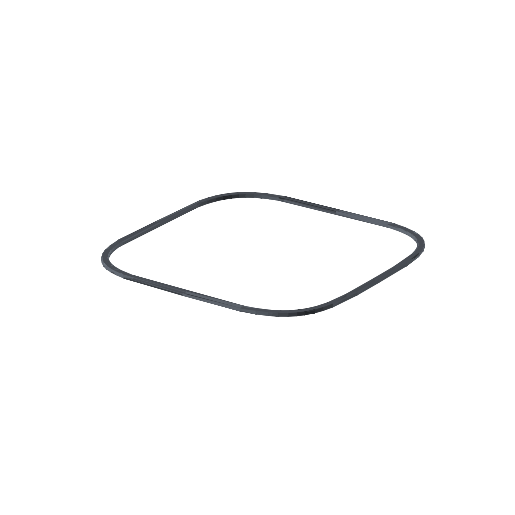
reports/drawings/views/anti_slip_ring_iso.png
