BigPappy098/Satellite1-Ultra/reports/drawings/views/ballast_cartridge_iso.png

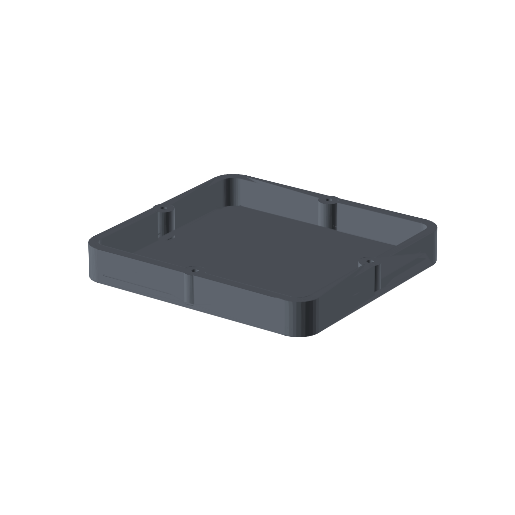
reports/drawings/views/ballast_cartridge_iso.png
