BigPappy098/Satellite1-Ultra/reports/drawings/views/base_skirt_iso.png

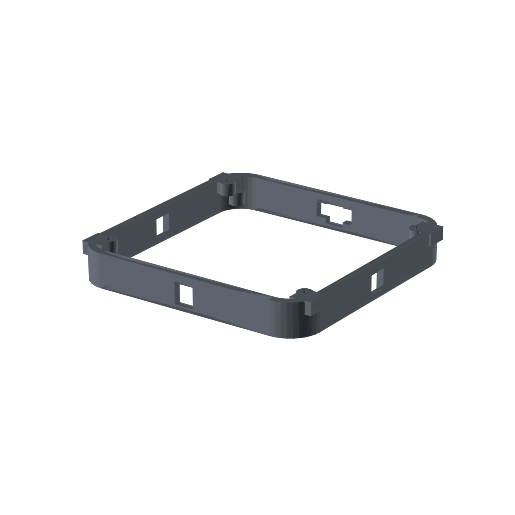
reports/drawings/views/base_skirt_iso.png
