BigPappy098/Satellite1-Ultra/reports/drawings/views/cable_gland_front.png

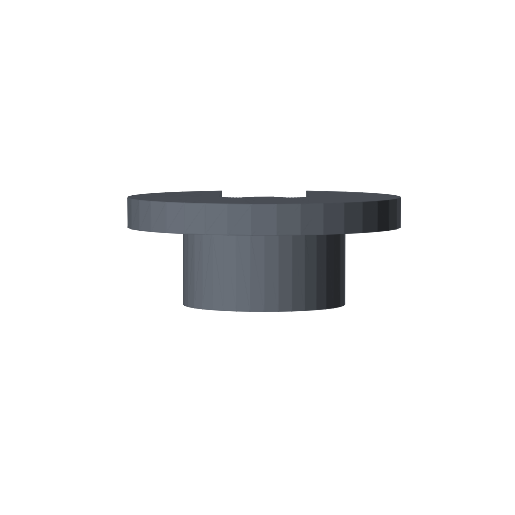
reports/drawings/views/cable_gland_front.png
