BigPappy098/Satellite1-Ultra/reports/drawings/views/cable_gland_iso.png

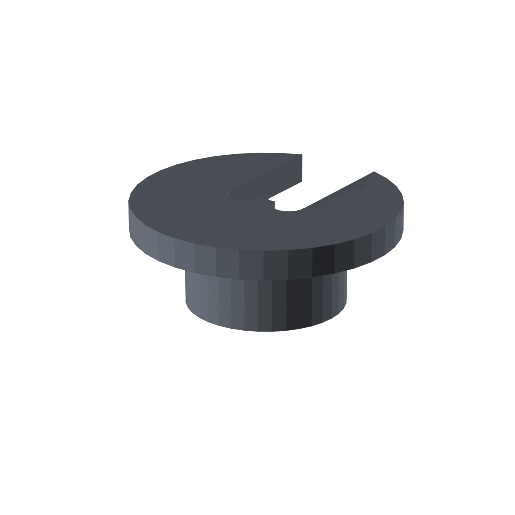
reports/drawings/views/cable_gland_iso.png
