BigPappy098/Satellite1-Ultra/reports/drawings/views/coupon_gasket_base_side.png

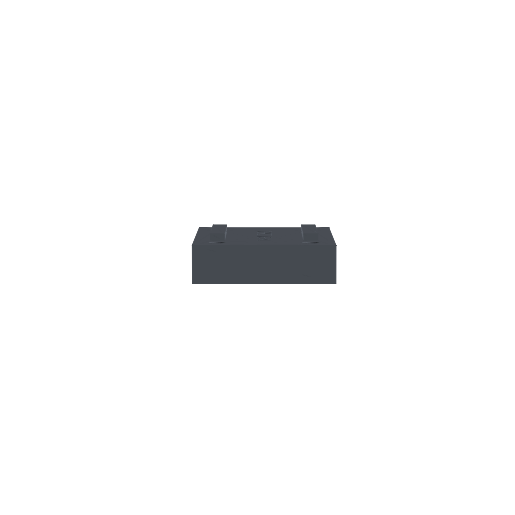
reports/drawings/views/coupon_gasket_base_side.png
