BigPappy098/Satellite1-Ultra/reports/drawings/views/coupon_passive_radiator_iso.png

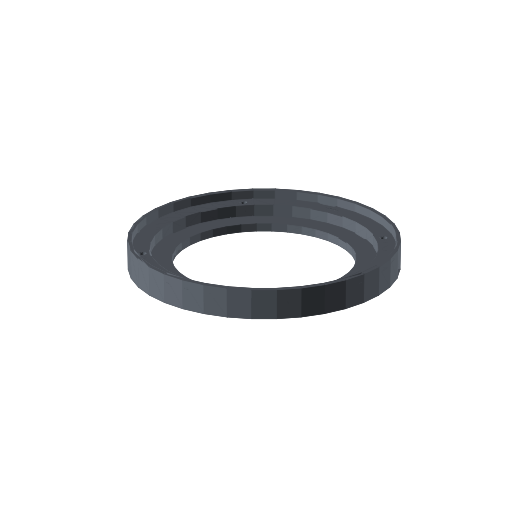
reports/drawings/views/coupon_passive_radiator_iso.png
