BigPappy098/Satellite1-Ultra/reports/drawings/views/divider_gasket_iso.png

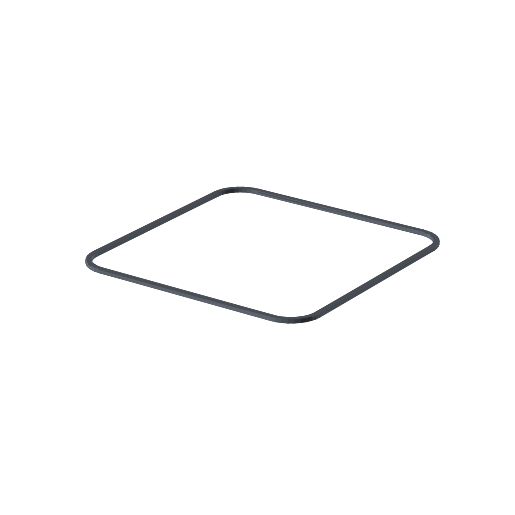
reports/drawings/views/divider_gasket_iso.png
