BigPappy098/Satellite1-Ultra/reports/drawings/views/main_cabinet_front.png

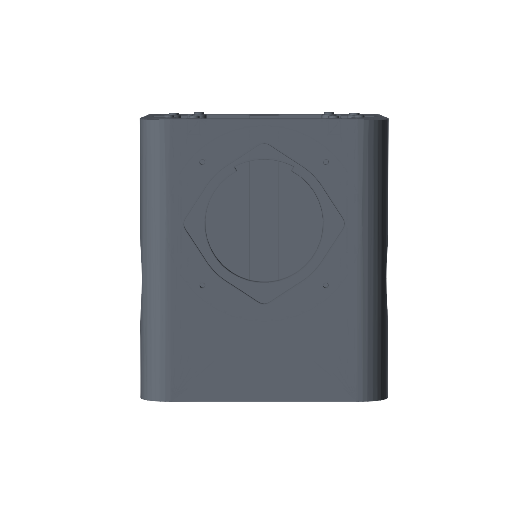
reports/drawings/views/main_cabinet_front.png
