BigPappy098/Satellite1-Ultra/reports/drawings/views/main_cabinet_iso.png

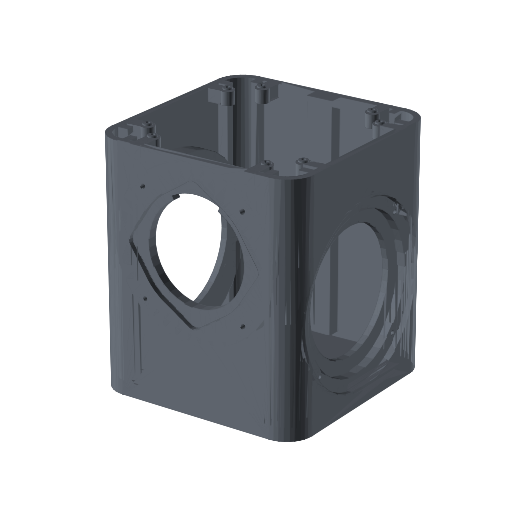
reports/drawings/views/main_cabinet_iso.png
