BigPappy098/Satellite1-Ultra/reports/drawings/views/mic_isolation_bushing_iso.png

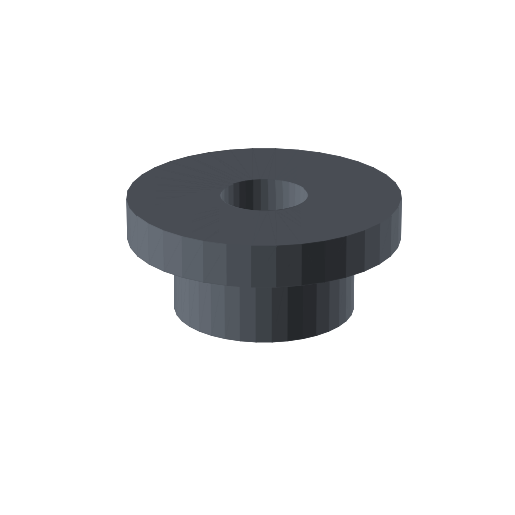
reports/drawings/views/mic_isolation_bushing_iso.png
