BigPappy098/Satellite1-Ultra/reports/drawings/views/passive_radiator_gasket_iso.png

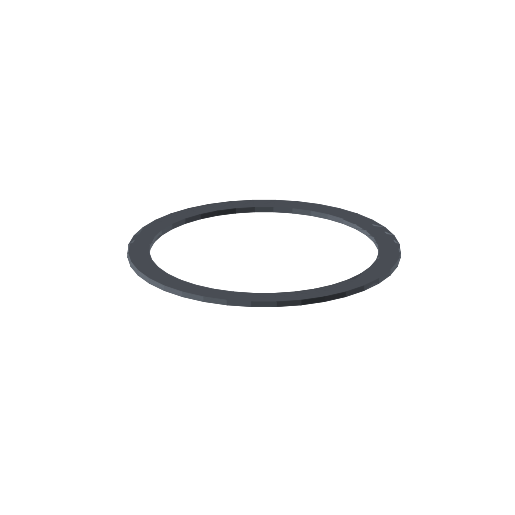
reports/drawings/views/passive_radiator_gasket_iso.png
