BigPappy098/Satellite1-Ultra/reports/drawings/views/shell_base_fabric_side.png

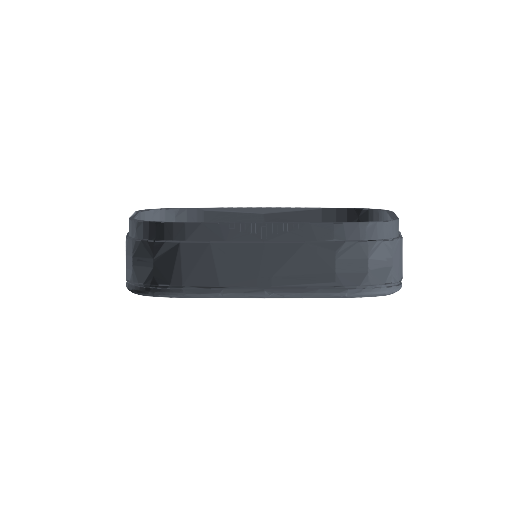
reports/drawings/views/shell_base_fabric_side.png
