BigPappy098/Satellite1-Ultra/reports/drawings/views/shell_grille_fabric_front.png

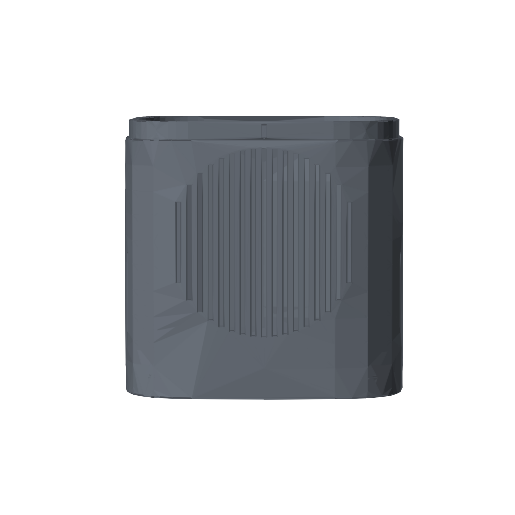
reports/drawings/views/shell_grille_fabric_front.png
