BigPappy098/Satellite1-Ultra/reports/drawings/views/shell_grille_fabric_iso.png

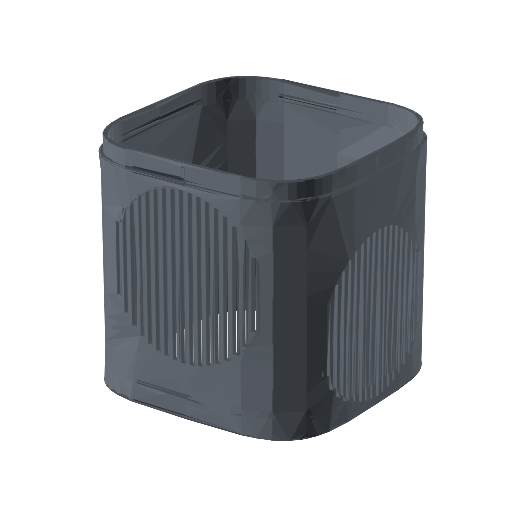
reports/drawings/views/shell_grille_fabric_iso.png
