BigPappy098/Satellite1-Ultra/reports/drawings/views/shell_grille_fabric_side.png

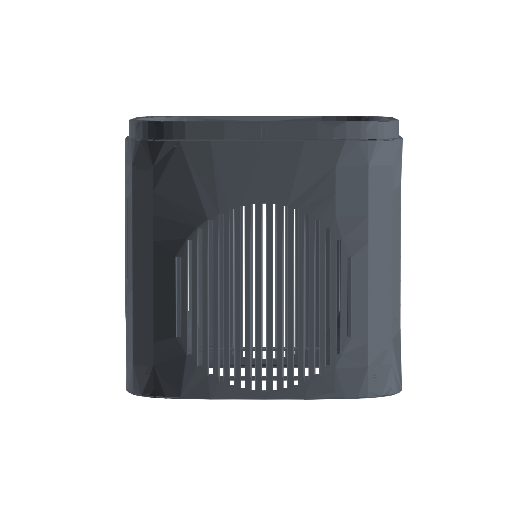
reports/drawings/views/shell_grille_fabric_side.png
