BigPappy098/Satellite1-Ultra/release/Satellite1-Ultra-RC1/ADVANCED/IMAGES/exploded_parts_identification.png

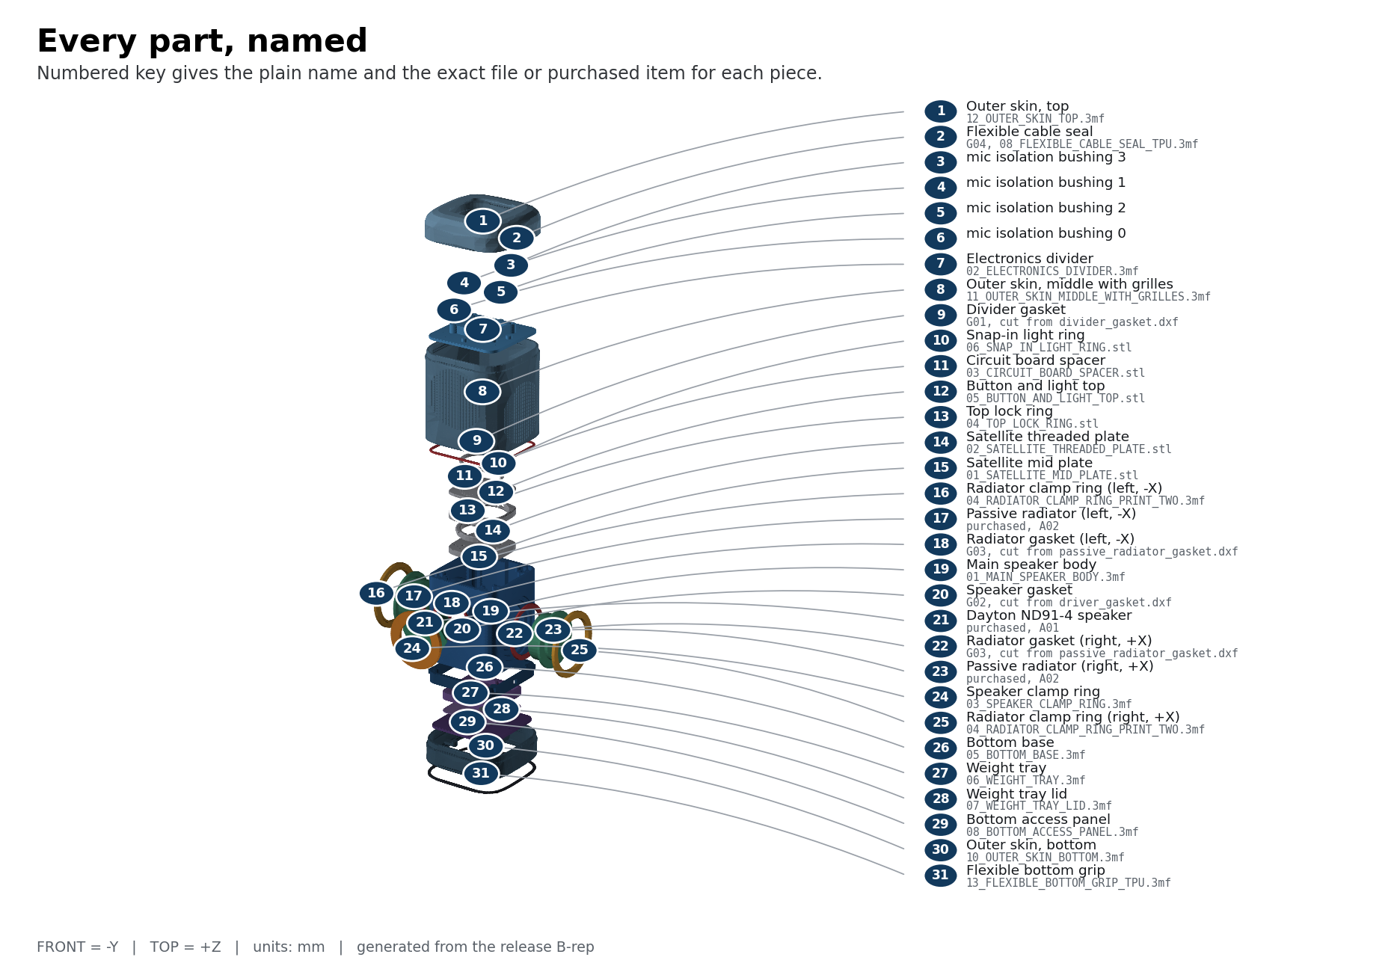
release/Satellite1-Ultra-RC1/ADVANCED/IMAGES/exploded_parts_identification.png
