BigPappy098/Satellite1-Ultra/reference-assets/official/Satellite1-Enclosures/DIY Enclosures/Squircle Enclosures/Geometry Files/STEP/Mid-Plate/Mid-Plate Threads.step

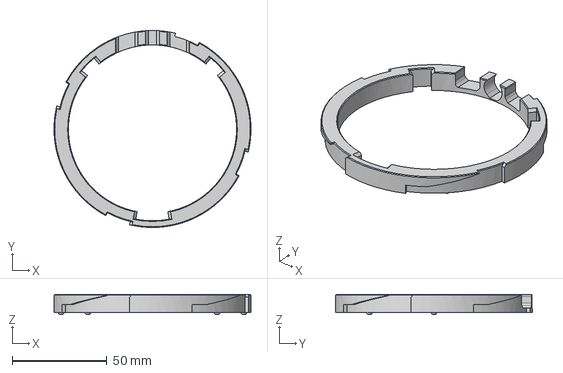
[picture p74: CAD file, 2026-07-28]
reference-assets/official/Satellite1-Enclosures/DIY Enclosures/Squircle Enclosures/Geometry Files/STEP/Mid-Plate/Mid-Plate Threads.step
104.0 x 104.0 x 10.6 mm
