BigPappy098/Satellite1-Ultra/reference-assets/official/Satellite1-Enclosures/DIY Enclosures/Squircle Enclosures/Geometry Files/STEP/Speaker Chamber/25-Watt Speaker Chamber.step

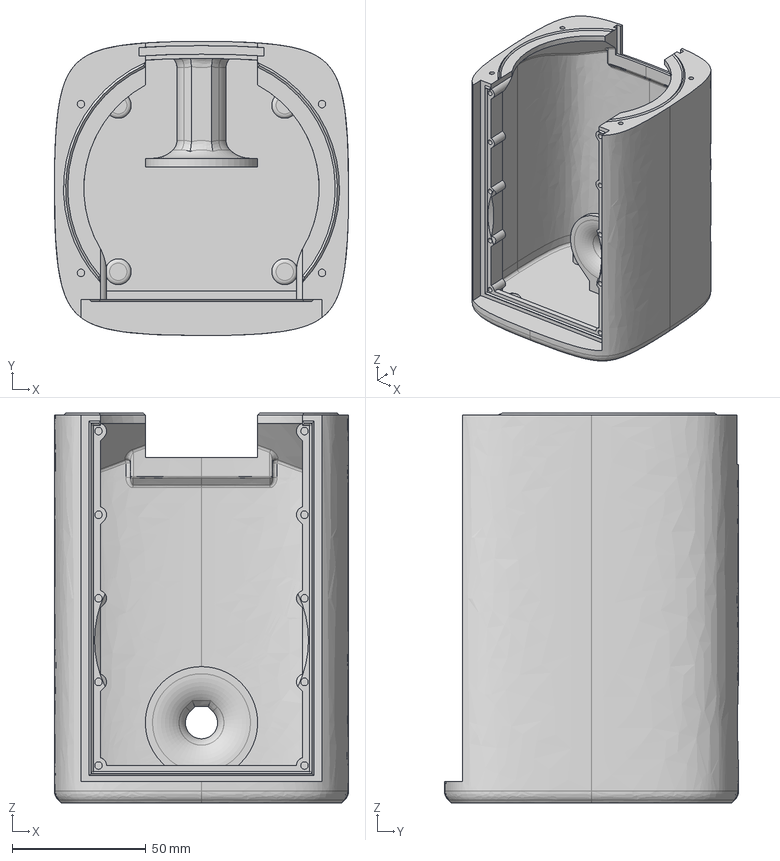
[picture p75: CAD file, 2026-07-28]
reference-assets/official/Satellite1-Enclosures/DIY Enclosures/Squircle Enclosures/Geometry Files/STEP/Speaker Chamber/25-Watt Speaker Chamber.step
110.0 x 110.0 x 145.8 mm
