BigPappy098/Satellite1-Ultra/reference-assets/official/Satellite1-Enclosures/DIY Enclosures/Squircle Enclosures/Geometry Files/STEP/Speaker Plates/15-Watt Speaker Plate Triple Speaker.step

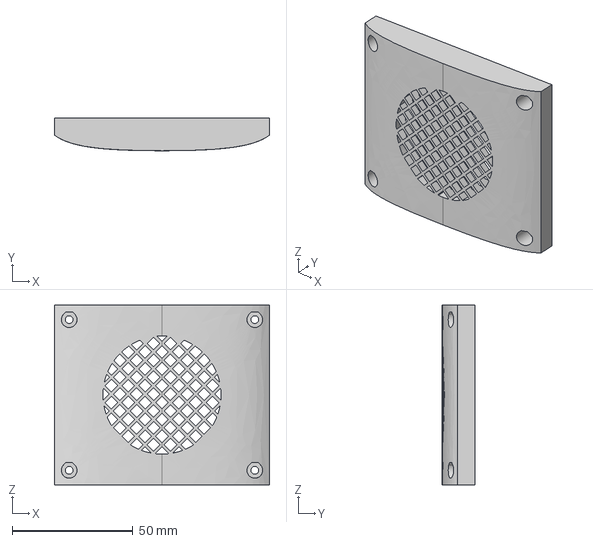
[picture p76: CAD file, 2026-07-28]
reference-assets/official/Satellite1-Enclosures/DIY Enclosures/Squircle Enclosures/Geometry Files/STEP/Speaker Plates/15-Watt Speaker Plate Triple Speaker.step
89.2 x 13.5 x 74.5 mm
