BigPappy098/Satellite1-Ultra/reference-assets/official/Satellite1-Enclosures/DIY Enclosures/Squircle Enclosures/Geometry Files/STEP/Squircle Top/Top Plate.step

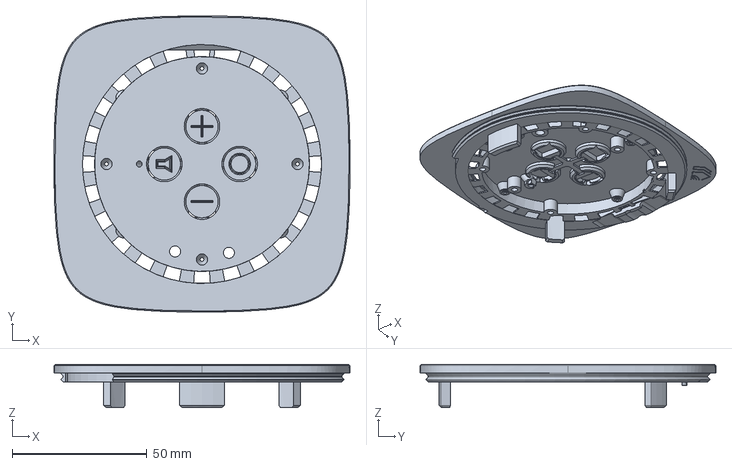
[picture p77: CAD file, 2026-07-28]
reference-assets/official/Satellite1-Enclosures/DIY Enclosures/Squircle Enclosures/Geometry Files/STEP/Squircle Top/Top Plate.step
110.0 x 110.0 x 16.0 mm
