BigPappy098/Satellite1-Ultra/reference-assets/official/Satellite1-Enclosures/DIY Enclosures/Squircle Enclosures/Geometry Files/STEP/Wire Covers/Wire Cover 2mm.step

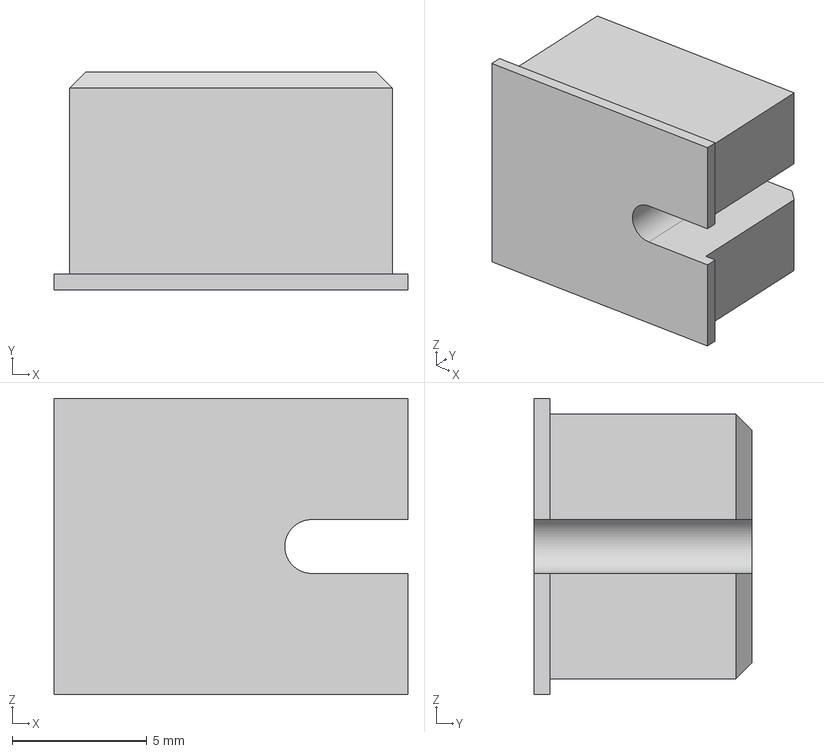
[picture p78: CAD file, 2026-07-28]
reference-assets/official/Satellite1-Enclosures/DIY Enclosures/Squircle Enclosures/Geometry Files/STEP/Wire Covers/Wire Cover 2mm.step
13.2 x 8.10 x 11.0 mm
