BigPappy098/Satellite1-Ultra/reference-assets/official/Satellite1-Enclosures/OEM Enclosures/Satellite1.1 Smart Speaker Enclosure Kit/Geometry Files/STEP/Sat1.x - Top Plate multi material.step

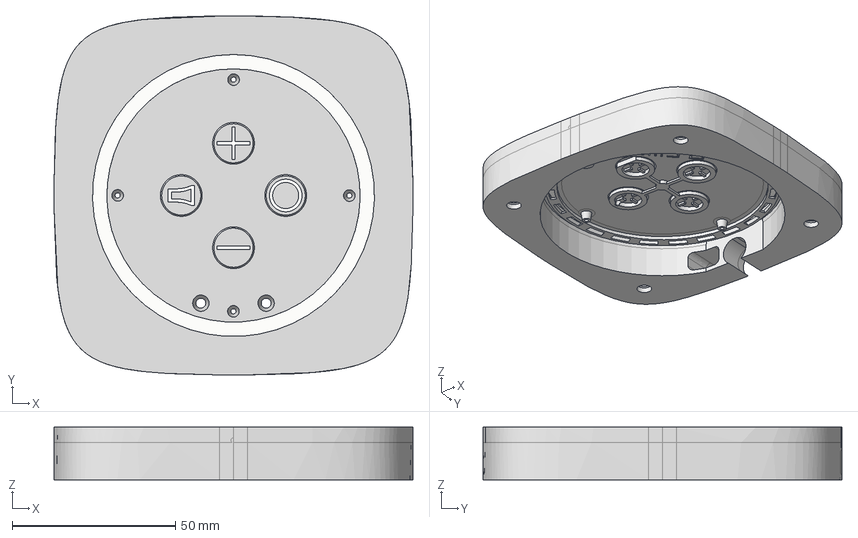
[picture p79: CAD file, 2026-07-28]
reference-assets/official/Satellite1-Enclosures/OEM Enclosures/Satellite1.1 Smart Speaker Enclosure Kit/Geometry Files/STEP/Sat1.x - Top Plate multi material.step
110.0 x 110.0 x 16.2 mm
Top multimaterial
Mute
Minus
Action
Plus
Diffuser
