BigPappy098/Satellite1-Ultra/reference-assets/official/Satellite1-Enclosures/OEM Enclosures/Satellite1.1 Smart Speaker Enclosure Kit/Sat 1.x Enclosure large - multimaterial grey (Bambu Studio Projectfile).3mf

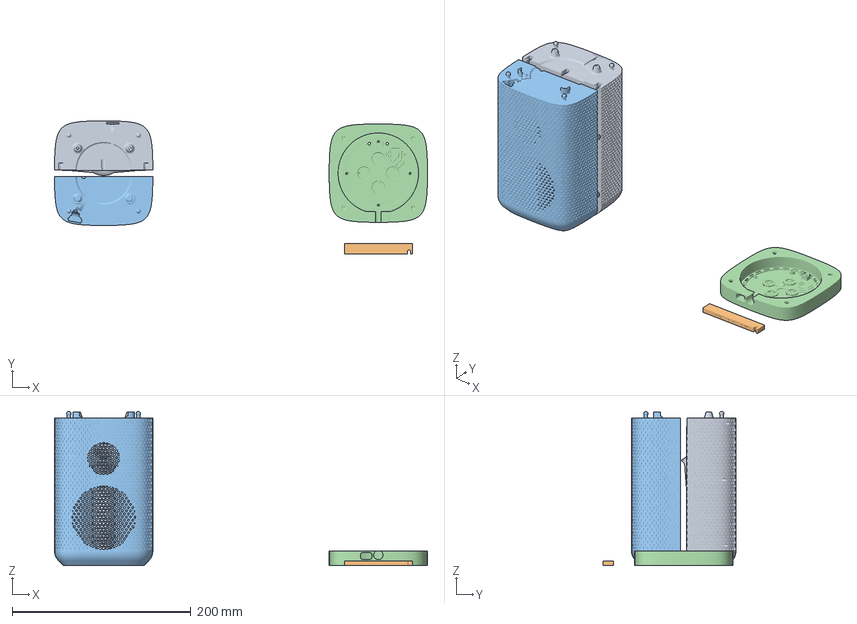
[picture p80: CAD file, 2026-07-28]
reference-assets/official/Satellite1-Enclosures/OEM Enclosures/Satellite1.1 Smart Speaker Enclosure Kit/Sat 1.x Enclosure large - multimaterial grey (Bambu Studio Projectfile).3mf
417.2 x 149.0 x 172.5 mm
Chamber back - Wifi pocket + Bass port.stl
Screw guide
Chamber front - FPH Woofer +Tweeter + LD2450 pocket.stl
Top - Multimaterial
