BigPappy098/Satellite1-Ultra/reference-assets/official/Satellite1-Hardware/core/rev4.1core3D.step

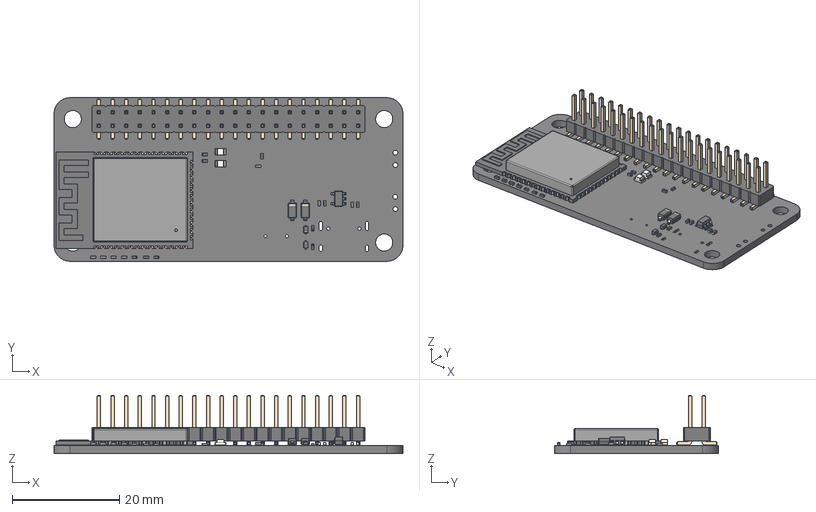
[picture p81: CAD file, 2026-07-28]
reference-assets/official/Satellite1-Hardware/core/rev4.1core3D.step
65.0 x 30.5 x 10.9 mm
D_SOD-523 x 2
R_0402_1005Metric x 8
LED_0805_2012Metric x 2
C_0402_1005Metric x 9
SOT-23-5
ESP32-S3-WROOM-1
PinHeader_2x20_P2.54mm_Vertical_SMD
D_SOD-123 x 2
sat1-core_PCB
