BigPappy098/Satellite1-Ultra/reference-assets/official/Satellite1-Hardware/shim/rev1shim3D.step

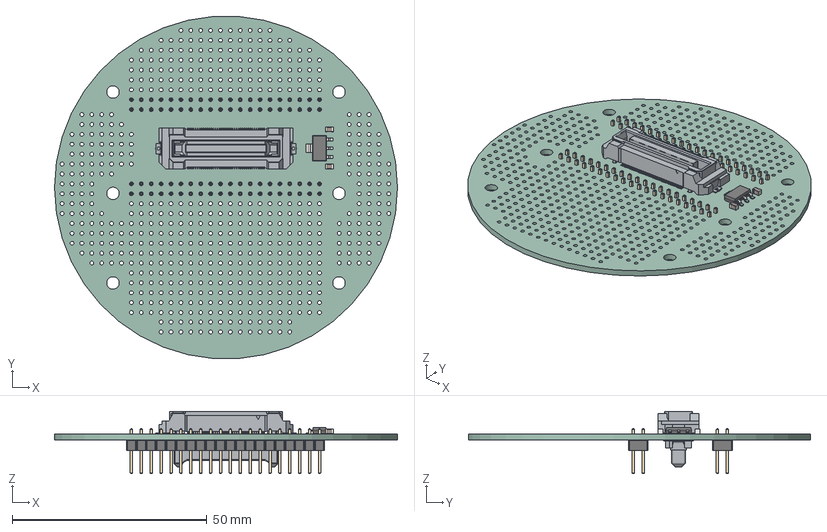
[picture p82: CAD file, 2026-07-28]
reference-assets/official/Satellite1-Hardware/shim/rev1shim3D.step
88.0 x 87.8 x 16.0 mm
C_0805_2012Metric x 2
FX23L-80S-0.5SV
SOT-223
PinHeader_2x20_P2.54mm_Vertical x 2
FX23L-80P-0.5SV8
sat1-shim_PCB
