BigPappy098/Satellite1-Ultra/reference-assets/official/Satellite1-Hardware/shoe/rev1shoe3D.step

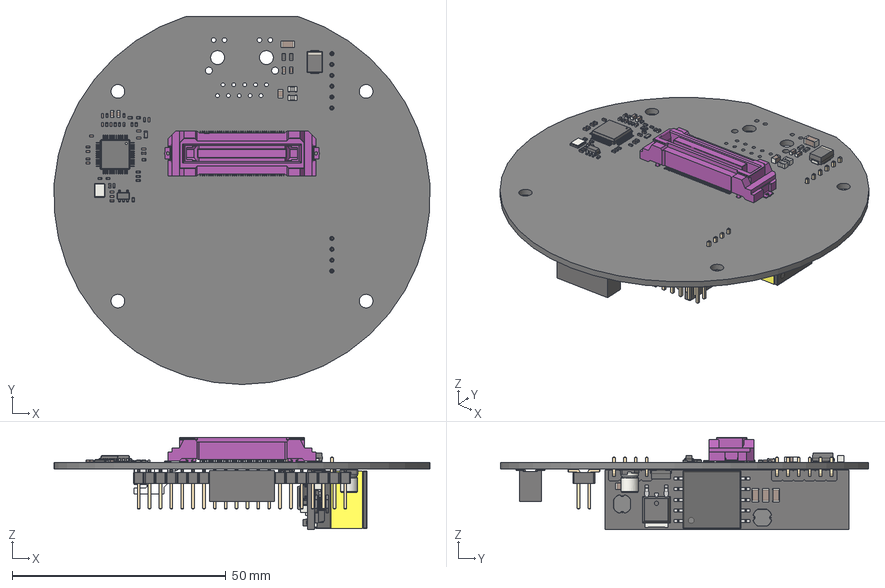
[picture p83: CAD file, 2026-07-28]
reference-assets/official/Satellite1-Hardware/shoe/rev1shoe3D.step
87.8 x 86.0 x 21.6 mm
C_0402_1005Metric x 20
R_0402_1005Metric x 19
C_0805_2012Metric
C_0603_1608Metric x 4
L_0805_2012Metric x 2
R_0603_1608Metric x 2
D_SMB
L0603_L1.6-W0.8-H0.5_BEAD
SOT-23-5 x 2
LQFP-48_7x7mm_P0.5mm
FX23L-80S-0.5SV
C_1206_3216Metric x 7
Crystal_SMD_3225-4Pin_3.2x2.5mm
CONN-SMD_2P-P2.50-A2501-WF-02A
PinSocket_2x06_P2.54mm_Vertical_SMD
PinHeader_1x06_P254mm_Horizontal
PinHeader_1x04_P254mm_Horizontal
CQ assembly x 2
TO-269AA x 2
SO_4_44x36mm_P254mm
CQ assembly (1)
D_SOD_123F
RT5400B_PCB
D_SMA
CP_Elec_4x5.4
PinHeader_2x20_P2.54mm_Vertical_SMD
minispeaker-shoe_PCB
