BigPappy098/Satellite1-Ultra/release/Satellite1-Ultra-RC1/1_PRINT_THIS_FIRST/01_MEASURE_YOUR_PRINTER.3mf

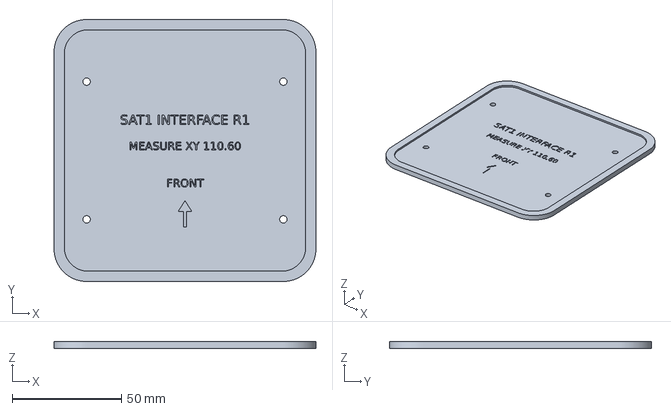
[picture p84: CAD file, 2026-08-10]
release/Satellite1-Ultra-RC1/1_PRINT_THIS_FIRST/01_MEASURE_YOUR_PRINTER.3mf
120.0 x 120.0 x 3.00 mm
