BigPappy098/Satellite1-Ultra/release/Satellite1-Ultra-RC1/3_ENCLOSURE_PARTS/05_BOTTOM_BASE.3mf

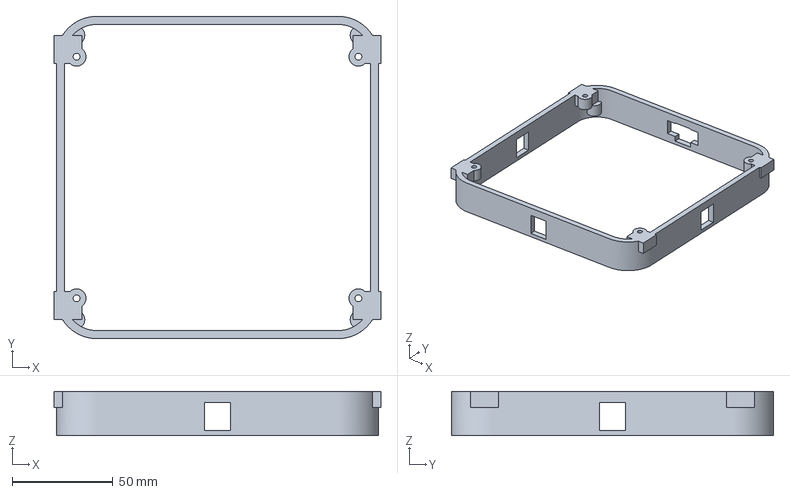
[picture p85: CAD file, 2026-08-10]
release/Satellite1-Ultra-RC1/3_ENCLOSURE_PARTS/05_BOTTOM_BASE.3mf
162.4 x 160.0 x 22.0 mm
