BigPappy098/Satellite1-Ultra/release/Satellite1-Ultra-RC1/3_ENCLOSURE_PARTS/OPTIONAL_FABRIC_WRAP/12F_OUTER_SKIN_TOP_FOR_FABRIC.3mf

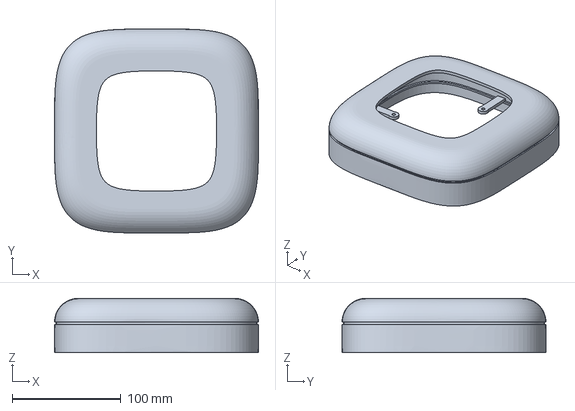
[picture p86: CAD file, 2026-08-10]
release/Satellite1-Ultra-RC1/3_ENCLOSURE_PARTS/OPTIONAL_FABRIC_WRAP/12F_OUTER_SKIN_TOP_FOR_FABRIC.3mf
188.0 x 188.0 x 50.1 mm
