BigPappy098/Satellite1-Ultra/release/Satellite1-Ultra-RC1/ADVANCED/3MF/coupon_passive_radiator.3mf

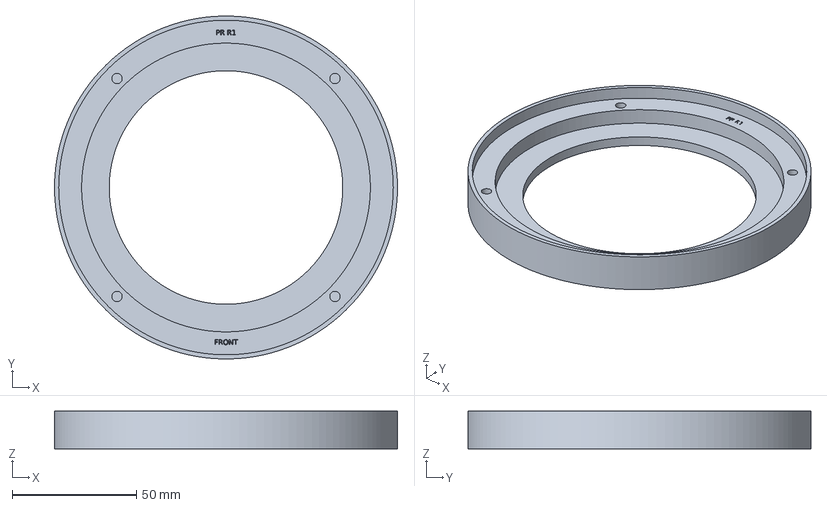
[picture p87: CAD file, 2026-08-10]
release/Satellite1-Ultra-RC1/ADVANCED/3MF/coupon_passive_radiator.3mf
138.0 x 138.0 x 15.2 mm
