BigPappy098/Satellite1-Ultra/release/Satellite1-Ultra-RC1/ADVANCED/CALIBRATION_PARTS/coupon_cable_passage.3mf

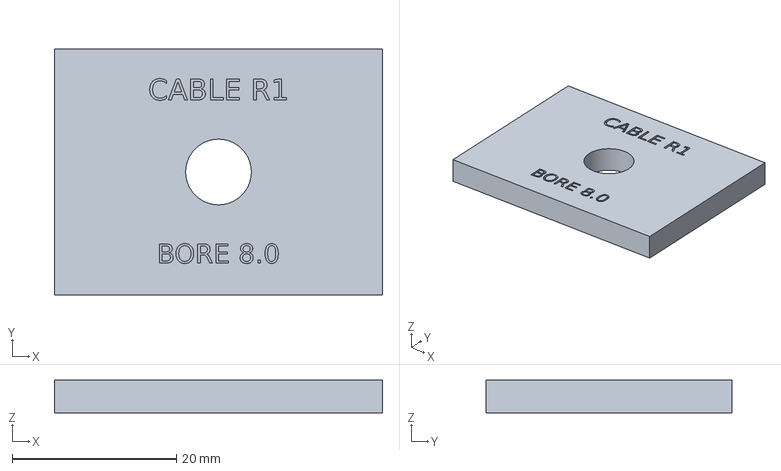
[picture p88: CAD file, 2026-08-10]
release/Satellite1-Ultra-RC1/ADVANCED/CALIBRATION_PARTS/coupon_cable_passage.3mf
40.0 x 30.0 x 4.00 mm
