BigPappy098/Satellite1-Ultra/release/Satellite1-Ultra-RC1/ADVANCED/OFFICIAL_PARTS/OPTIONAL_MULTI_MATERIAL/official_top_plate_mm_buttons.stl

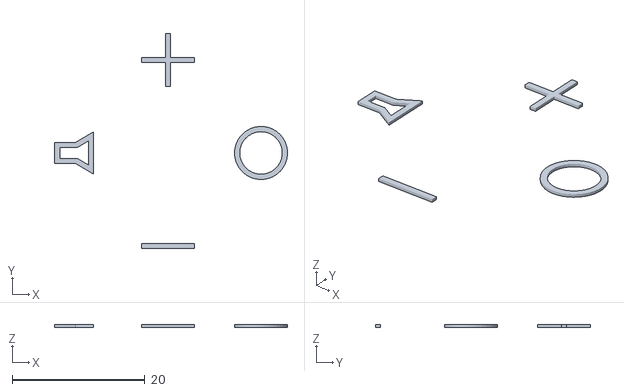
[picture p89: CAD file, 2026-07-28]
release/Satellite1-Ultra-RC1/ADVANCED/OFFICIAL_PARTS/OPTIONAL_MULTI_MATERIAL/official_top_plate_mm_buttons.stl
35.1 x 32.4 x 0.4
