BigPappy098/Satellite1-Ultra/exports/gasket_templates/driver_gasket.dxf

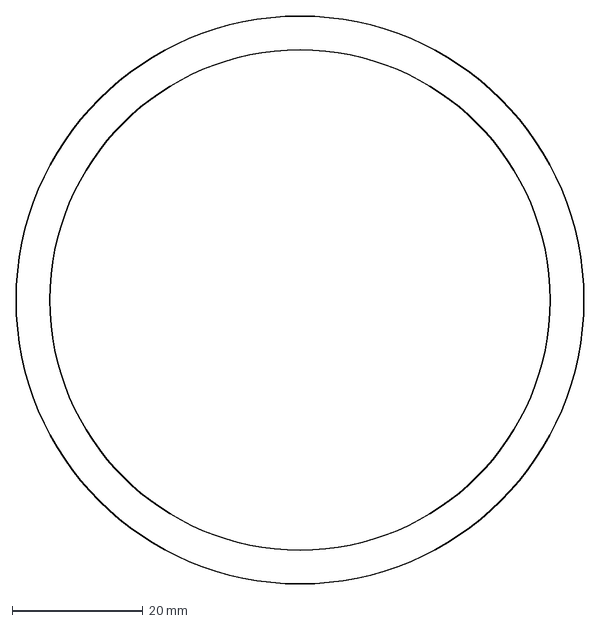
[picture p90: CAD file, 2026-08-10]
exports/gasket_templates/driver_gasket.dxf
87.0 x 87.0 mm
