BigPappy098/Satellite1-Ultra/exports/step/cable_gland.step

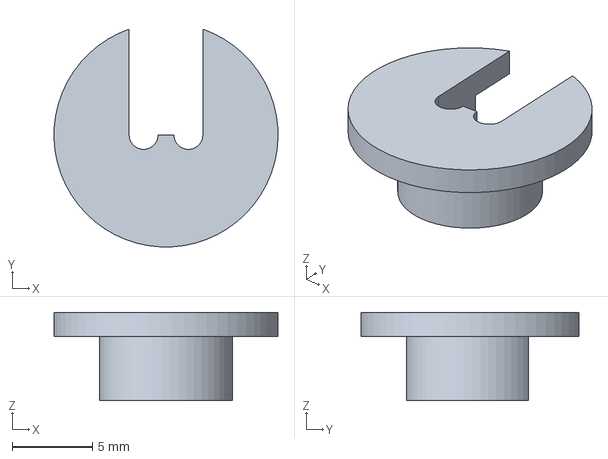
[picture p91: CAD file, 2026-08-10]
exports/step/cable_gland.step
14.0 x 13.6 x 5.50 mm
