BigPappy098/Satellite1-Ultra/reference-assets/official/Satellite1-Enclosures/assets/Core R2025.03.stl

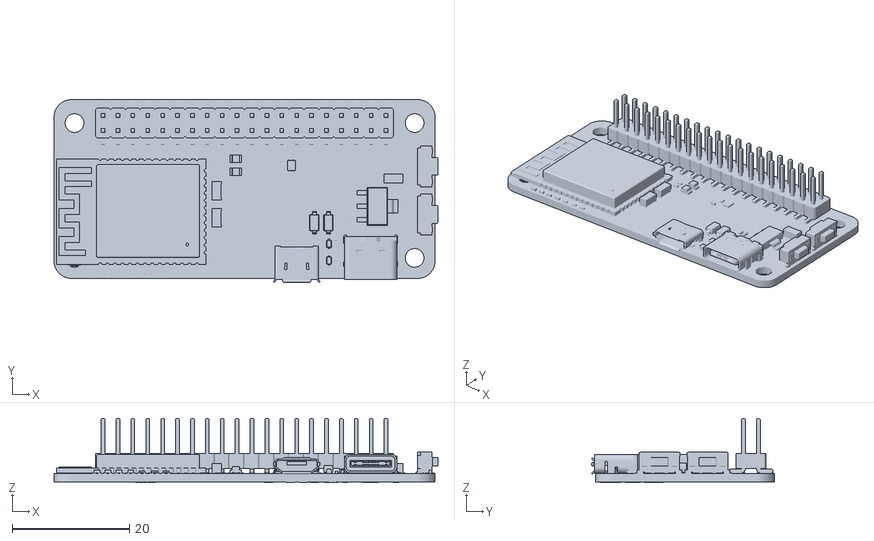
[picture p92: CAD file, 2026-07-28]
reference-assets/official/Satellite1-Enclosures/assets/Core R2025.03.stl
65.5 x 31.2 x 11.0
