BigPappy098/Satellite1-Ultra/reference-assets/official/Satellite1-Enclosures/DIY Enclosures/Cylindrical Enclosures/Geometry Files/STEP/Speaker - GRS 3FR-4/Speaker Stand - GRS 3FR-4.step

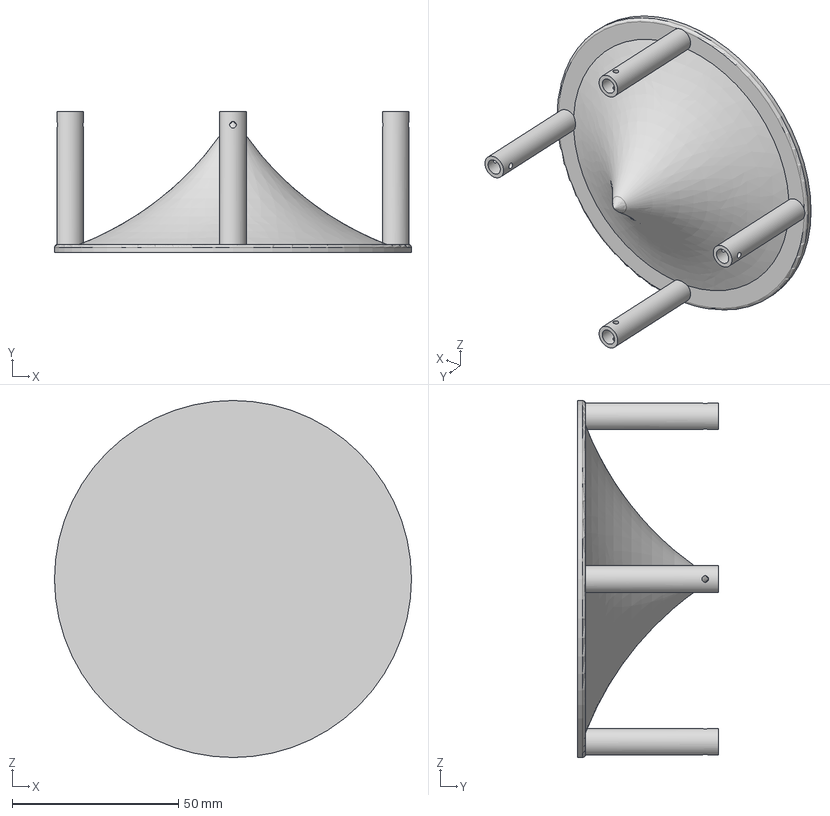
[picture p95: CAD file, 2026-07-28]
reference-assets/official/Satellite1-Enclosures/DIY Enclosures/Cylindrical Enclosures/Geometry Files/STEP/Speaker - GRS 3FR-4/Speaker Stand - GRS 3FR-4.step
107.5 x 42.5 x 107.5 mm
