BigPappy098/Satellite1-Ultra/reference-assets/official/Satellite1-Enclosures/DIY Enclosures/Squircle Enclosures/Geometry Files/STEP/Mid-Plate/Mid-Plate.step

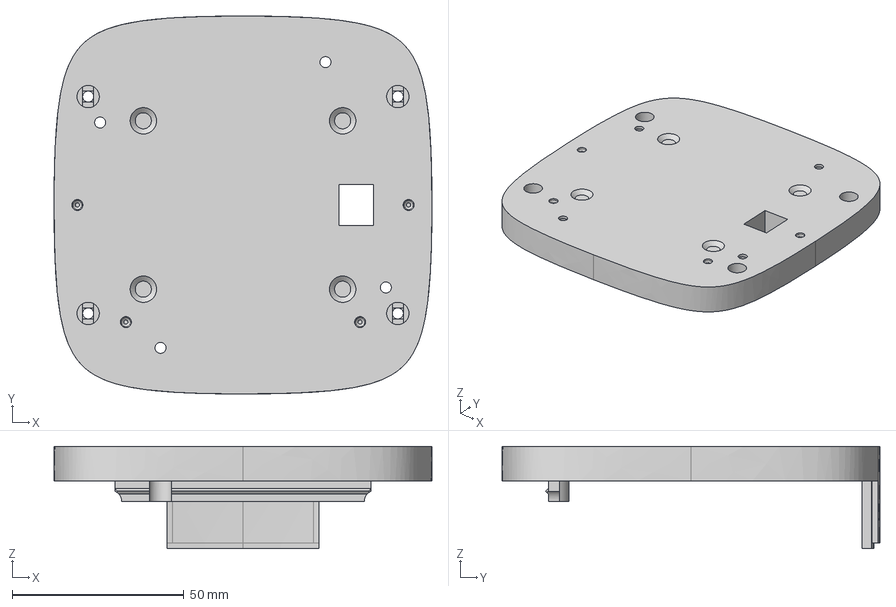
[picture p96: CAD file, 2026-07-28]
reference-assets/official/Satellite1-Enclosures/DIY Enclosures/Squircle Enclosures/Geometry Files/STEP/Mid-Plate/Mid-Plate.step
110.0 x 110.0 x 29.7 mm
