BigPappy098/Satellite1-Ultra/reference-assets/official/Satellite1-Enclosures/DIY Enclosures/Squircle Enclosures/Geometry Files/STEP/Speaker Chamber/25-Watt Speaker Chamber Anti-Slip Ring.step

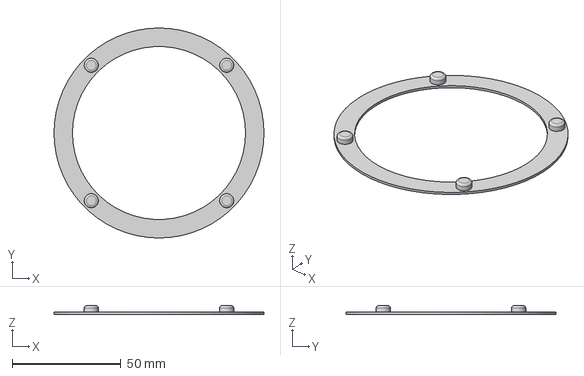
[picture p97: CAD file, 2026-07-28]
reference-assets/official/Satellite1-Enclosures/DIY Enclosures/Squircle Enclosures/Geometry Files/STEP/Speaker Chamber/25-Watt Speaker Chamber Anti-Slip Ring.step
96.5 x 96.5 x 4.00 mm
