BigPappy098/Satellite1-Ultra/reference-assets/official/Satellite1-Enclosures/DIY Enclosures/Squircle Enclosures/Geometry Files/STEP/Speaker Plates/25-Watt Speaker Plate GRS 3FR3 and Visaton FRS8-4 3.3in.step

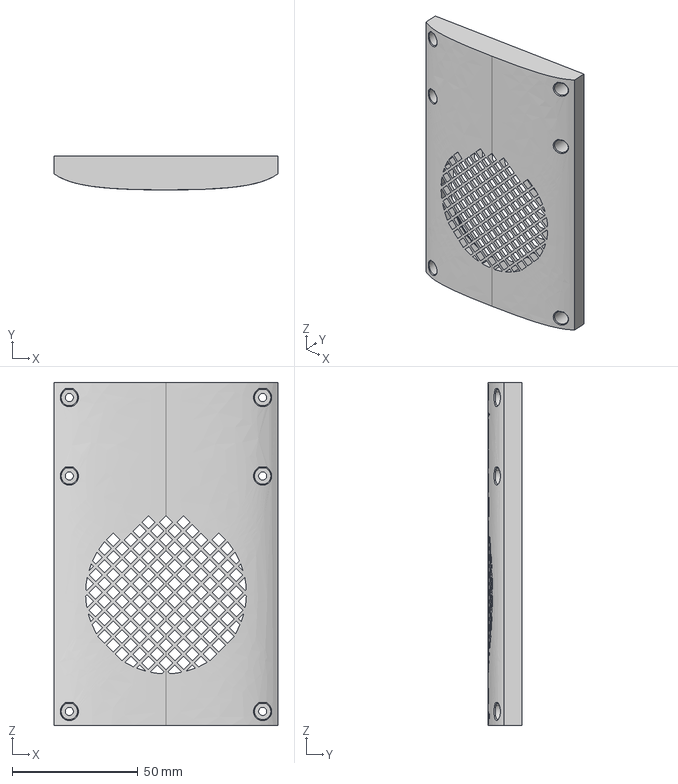
[picture p98: CAD file, 2026-07-28]
reference-assets/official/Satellite1-Enclosures/DIY Enclosures/Squircle Enclosures/Geometry Files/STEP/Speaker Plates/25-Watt Speaker Plate GRS 3FR3 and Visaton FRS8-4 3.3in.step
89.2 x 13.5 x 136.6 mm
