BigPappy098/Satellite1-Ultra/reference-assets/official/Satellite1-Enclosures/OEM Enclosures/Satellite1.1 Smart Speaker Enclosure Kit/Geometry Files/STEP/Sat1.x small - Chamber with 3525 speaker.step

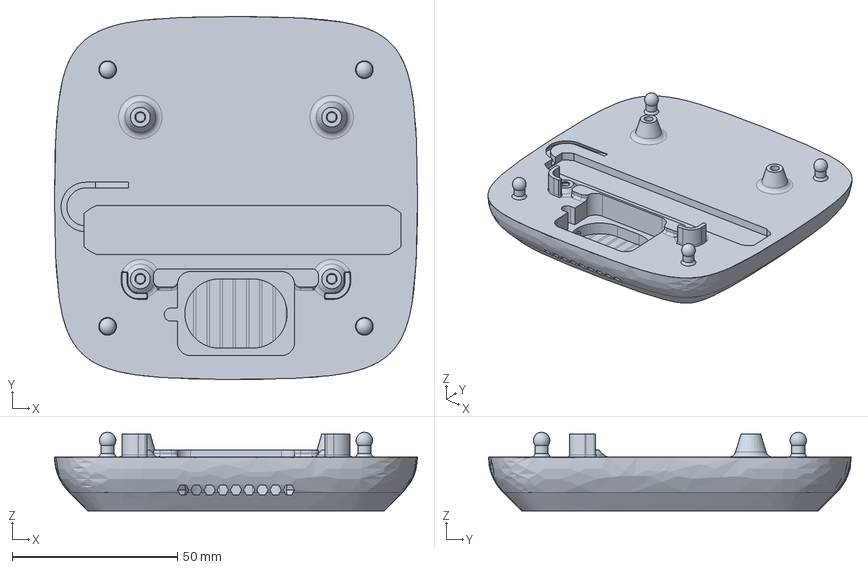
[picture p101: CAD file, 2026-07-28]
reference-assets/official/Satellite1-Enclosures/OEM Enclosures/Satellite1.1 Smart Speaker Enclosure Kit/Geometry Files/STEP/Sat1.x small - Chamber with 3525 speaker.step
110.0 x 110.0 x 23.8 mm
