BigPappy098/Satellite1-Ultra/reference-assets/official/Satellite1-Hardware/core/rev5.1core3D.step

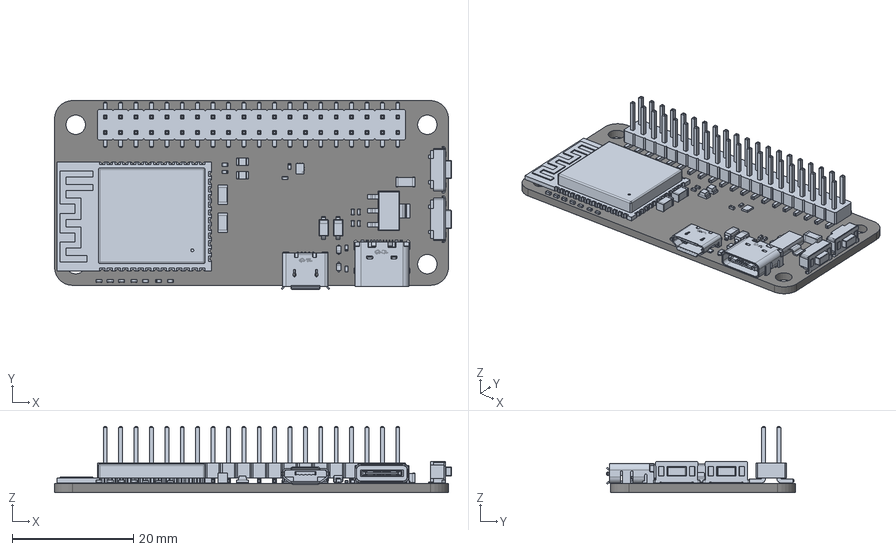
[picture p102: CAD file, 2026-07-28]
reference-assets/official/Satellite1-Hardware/core/rev5.1core3D.step
65.5 x 31.2 x 10.9 mm
D_SOD-523 x 2
R_0402_1005Metric x 8
LED_0805_2012Metric x 2
C_0402_1005Metric x 9
SOT-223
C_1206_3216Metric x 3
ESP32-S3-WROOM-1
PinHeader_2x20_P2.54mm_Vertical_SMD
SW-SMD_YTSB001XXXX x 2
USB-C-SMD_HC-TYPE-C-16P-01A
D_SOD-123 x 2
UTQFN-10L_L1.8-W1.4-P0.40-BL
MICRO-USB-SMD_MICROQTJ-5P
kibot_n2mu79fv_PCB
