BigPappy098/Satellite1-Ultra/release/Satellite1-Ultra-RC1/3_ENCLOSURE_PARTS/13_FLEXIBLE_BOTTOM_GRIP_TPU.3mf

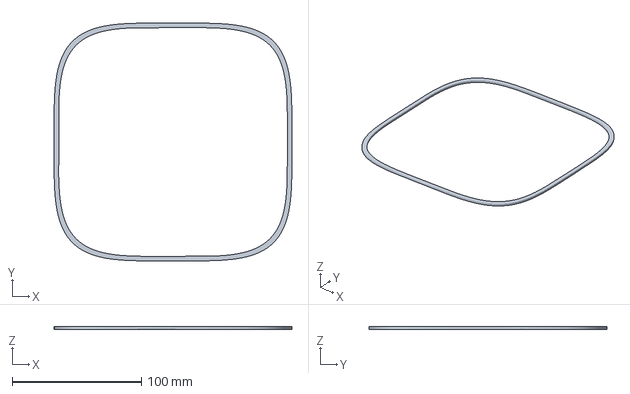
[picture p103: CAD file, 2026-08-10]
release/Satellite1-Ultra-RC1/3_ENCLOSURE_PARTS/13_FLEXIBLE_BOTTOM_GRIP_TPU.3mf
184.0 x 184.0 x 2.00 mm
