BigPappy098/Satellite1-Ultra/release/Satellite1-Ultra-RC1/ADVANCED/CALIBRATION_PARTS/coupon_active_driver.3mf

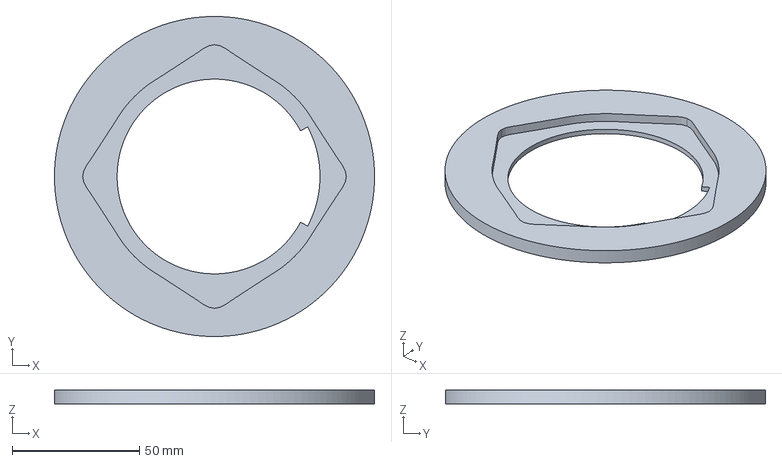
[picture p104: CAD file, 2026-08-10]
release/Satellite1-Ultra-RC1/ADVANCED/CALIBRATION_PARTS/coupon_active_driver.3mf
126.0 x 126.0 x 5.50 mm
