BigPappy098/Satellite1-Ultra/release/Satellite1-Ultra-RC1/ADVANCED/OFFICIAL_PARTS/OPTIONAL_MULTI_MATERIAL/official_top_plate_mm_diffuser_ring.stl

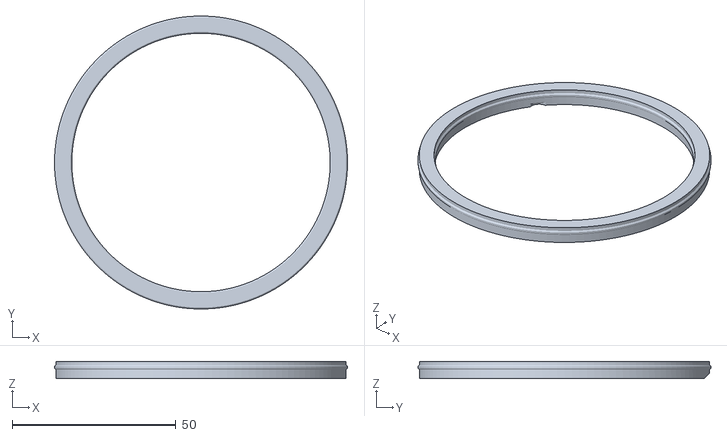
[picture p105: CAD file, 2026-07-28]
release/Satellite1-Ultra-RC1/ADVANCED/OFFICIAL_PARTS/OPTIONAL_MULTI_MATERIAL/official_top_plate_mm_diffuser_ring.stl
89.6 x 89.6 x 5.20
