BigPappy098/Satellite1-Ultra/release/Satellite1-Ultra-RC1/ADVANCED/STEP/active_driver_clamp_ring.step

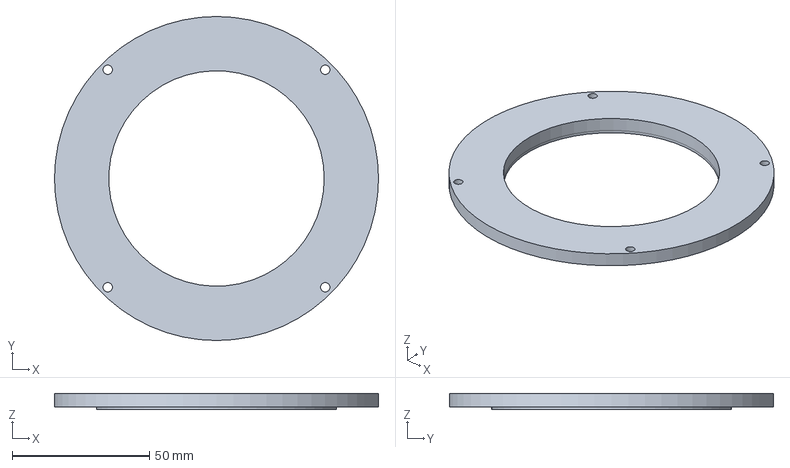
[picture p106: CAD file, 2026-08-10]
release/Satellite1-Ultra-RC1/ADVANCED/STEP/active_driver_clamp_ring.step
118.0 x 118.0 x 6.00 mm
