BigPappy098/Satellite1-Ultra/exports/assembly/satellite1_ultra_exploded.step

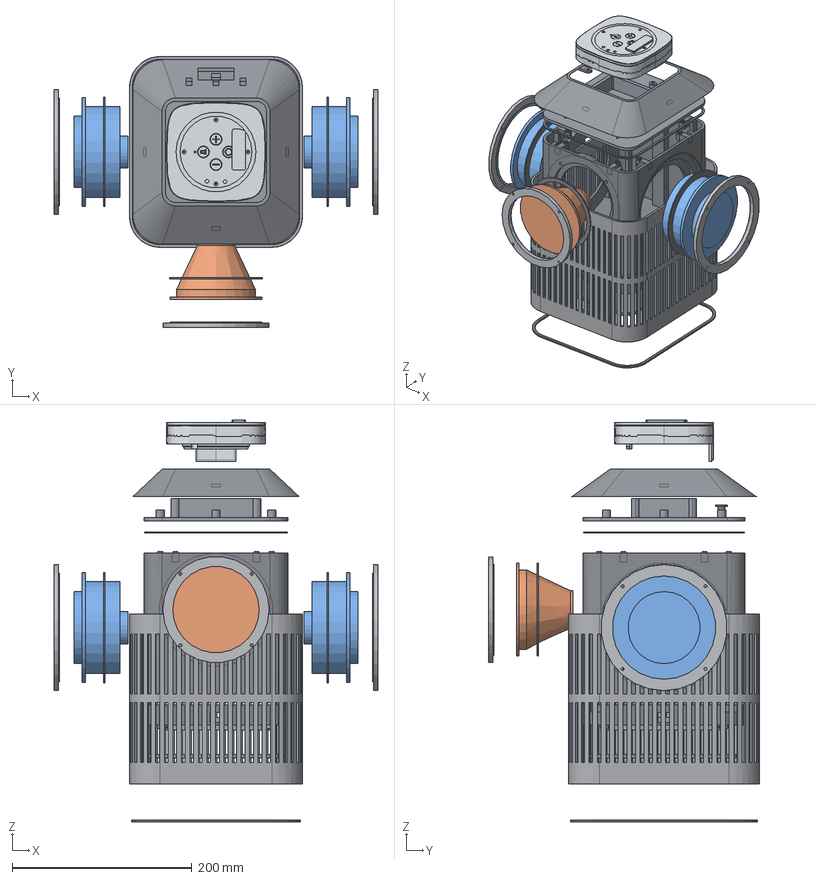
[picture p107: CAD file, 2026-07-28]
exports/assembly/satellite1_ultra_exploded.step
360.0 x 301.0 x 446.7 mm
anti_slip_ring
outer_shell
main_cabinet
divider_gasket
pressure_divider
electronics_shroud
wire_gland
active_driver_gasket
active_driver_clamp_ring
driver_envelope
base_skirt
bottom_service_plate
ballast_cartridge
ballast_cartridge_lid
pr_-1_gasket
pr_-1_clamp_ring
pr_-1_envelope
pr_+1_gasket
pr_+1_clamp_ring
pr_+1_envelope
official_mid_plate
official_mid_plate_threads
official_top_plate
official_pcb_spacer
official_lock_ring
official_hat_batch1_rev4_1_envelope
