BigPappy098/Satellite1-Ultra/exports/gasket_templates/divider_gasket.dxf

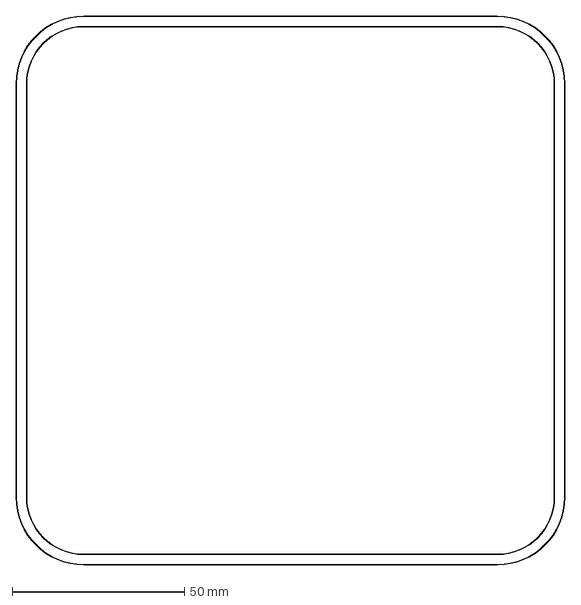
[picture p108: CAD file, 2026-08-10]
exports/gasket_templates/divider_gasket.dxf
159.0 x 159.0 mm
