BigPappy098/Satellite1-Ultra/reference-assets/official/Satellite1-Enclosures/DIY Enclosures/Cylindrical Enclosures/Geometry Files/STEP/Speaker - GRS 3FR-4/Speaker Adapter - GRS 3FR-4.step

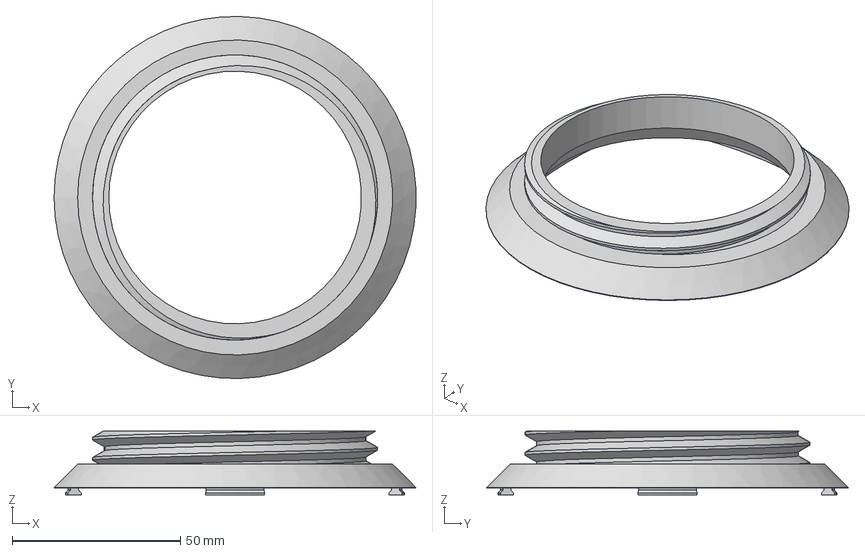
[picture p110: CAD file, 2026-07-28]
reference-assets/official/Satellite1-Enclosures/DIY Enclosures/Cylindrical Enclosures/Geometry Files/STEP/Speaker - GRS 3FR-4/Speaker Adapter - GRS 3FR-4.step
107.4 x 107.5 x 18.9 mm
