BigPappy098/Satellite1-Ultra/release/Satellite1-Ultra-RC1/3_ENCLOSURE_PARTS/07_WEIGHT_TRAY_LID.3mf

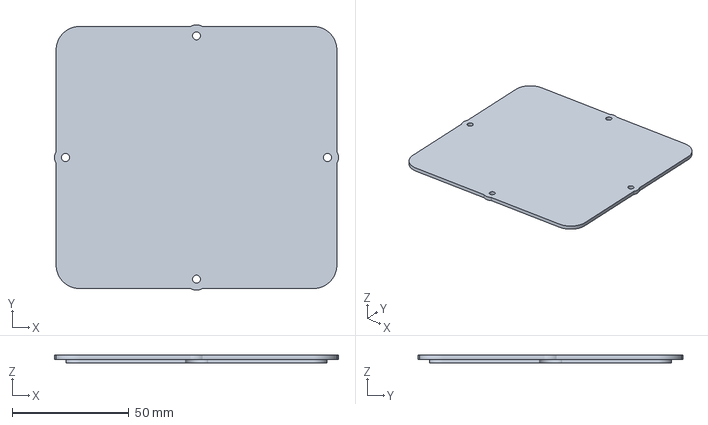
[picture p115: CAD file, 2026-08-10]
release/Satellite1-Ultra-RC1/3_ENCLOSURE_PARTS/07_WEIGHT_TRAY_LID.3mf
121.4 x 113.4 x 3.50 mm
