BigPappy098/Satellite1-Ultra/release/Satellite1-Ultra-RC1/3_ENCLOSURE_PARTS/OPTIONAL_FABRIC_WRAP/11F_OUTER_SKIN_MIDDLE_FOR_FABRIC.3mf

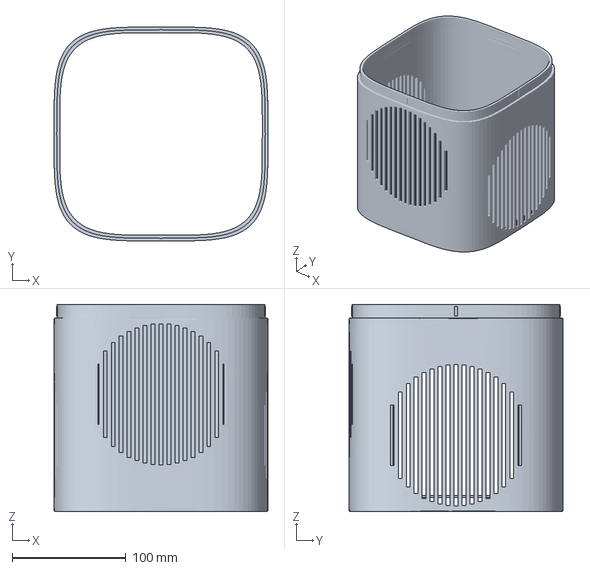
[picture p116: CAD file, 2026-08-10]
release/Satellite1-Ultra-RC1/3_ENCLOSURE_PARTS/OPTIONAL_FABRIC_WRAP/11F_OUTER_SKIN_MIDDLE_FOR_FABRIC.3mf
188.0 x 188.0 x 182.0 mm
