BigPappy098/Satellite1-Ultra/release/Satellite1-Ultra-RC1/ADVANCED/CALIBRATION_PARTS/coupon_heat_set_insert.3mf

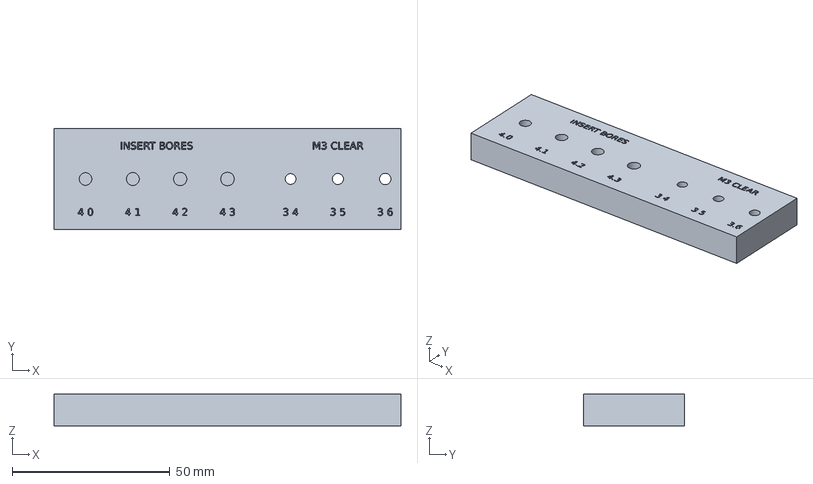
[picture p117: CAD file, 2026-08-10]
release/Satellite1-Ultra-RC1/ADVANCED/CALIBRATION_PARTS/coupon_heat_set_insert.3mf
110.0 x 32.0 x 10.0 mm
