BigPappy098/Satellite1-Ultra/exports/step/bottom_service_plate.step

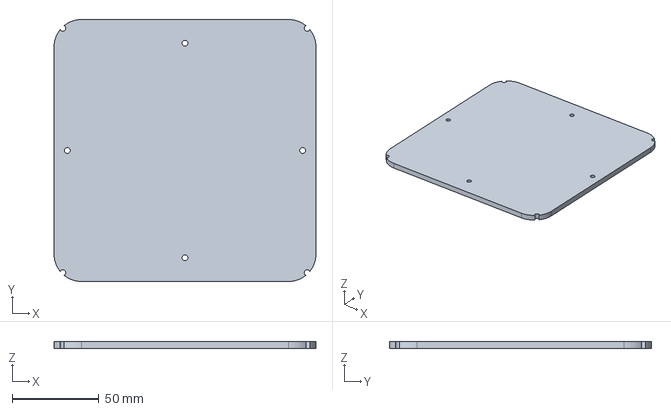
[picture p118: CAD file, 2026-08-10]
exports/step/bottom_service_plate.step
151.4 x 151.4 x 4.00 mm
