BigPappy098/Satellite1-Ultra/reference-assets/official/Satellite1-Enclosures/DIY Enclosures/Squircle Enclosures/Geometry Files/STEP/Speaker Chamber/3-Watt Speaker Chamber Legs x 4.step

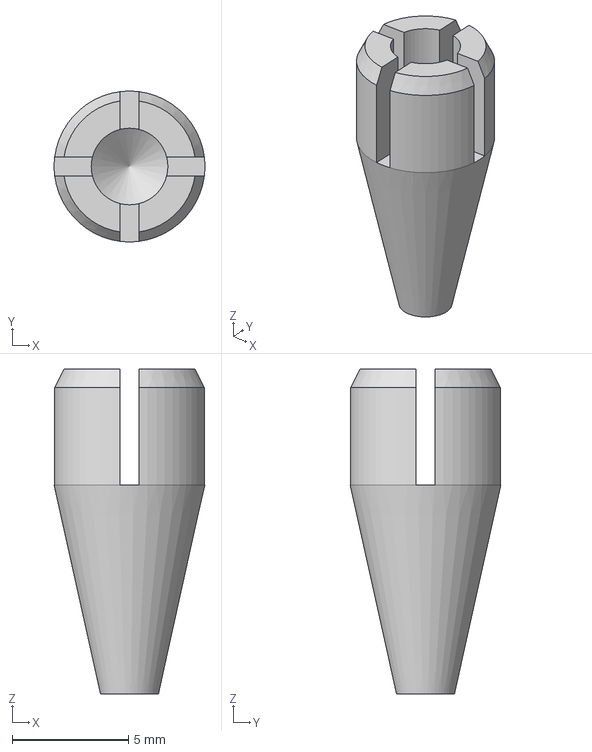
[picture p120: CAD file, 2026-07-28]
reference-assets/official/Satellite1-Enclosures/DIY Enclosures/Squircle Enclosures/Geometry Files/STEP/Speaker Chamber/3-Watt Speaker Chamber Legs x 4.step
6.50 x 6.49 x 14.0 mm
