BigPappy098/Satellite1-Ultra/reference-assets/official/Satellite1-Enclosures/OEM Enclosures/Satellite1.1 Smart Speaker Enclosure Kit/Geometry Files/STEP/Sat1.x - Top Plate single material - LED Diffuser.step

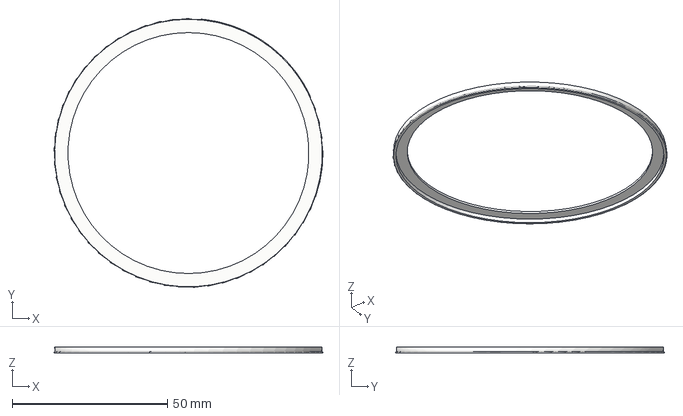
[picture p123: CAD file, 2026-07-28]
reference-assets/official/Satellite1-Enclosures/OEM Enclosures/Satellite1.1 Smart Speaker Enclosure Kit/Geometry Files/STEP/Sat1.x - Top Plate single material - LED Diffuser.step
86.8 x 86.8 x 2.00 mm
