BigPappy098/Satellite1-Ultra/release/Satellite1-Ultra-RC1/3_ENCLOSURE_PARTS/14_LEAK_TEST_TOOL.3mf

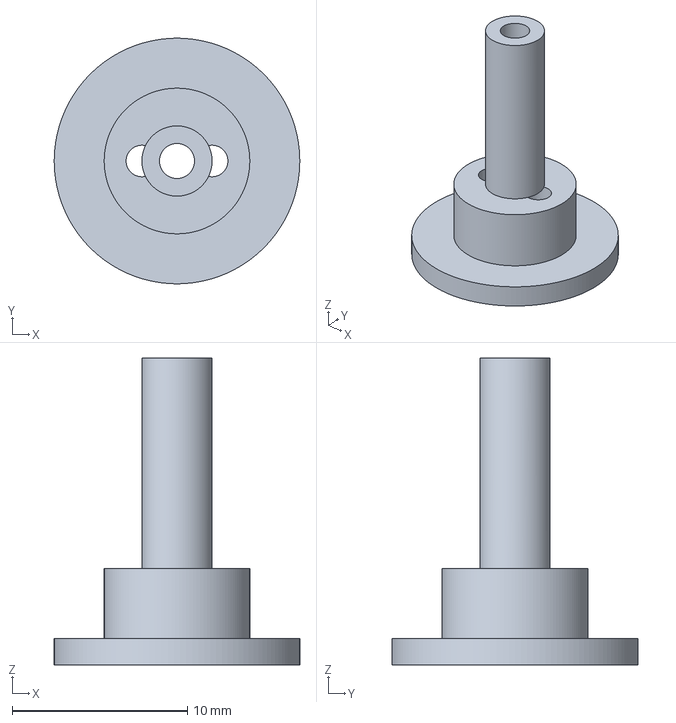
[picture p125: CAD file, 2026-08-10]
release/Satellite1-Ultra-RC1/3_ENCLOSURE_PARTS/14_LEAK_TEST_TOOL.3mf
14.0 x 14.0 x 17.5 mm
