BigPappy098/Satellite1-Ultra/release/Satellite1-Ultra-RC1/ADVANCED/3MF/coupon_gasket_cap.3mf

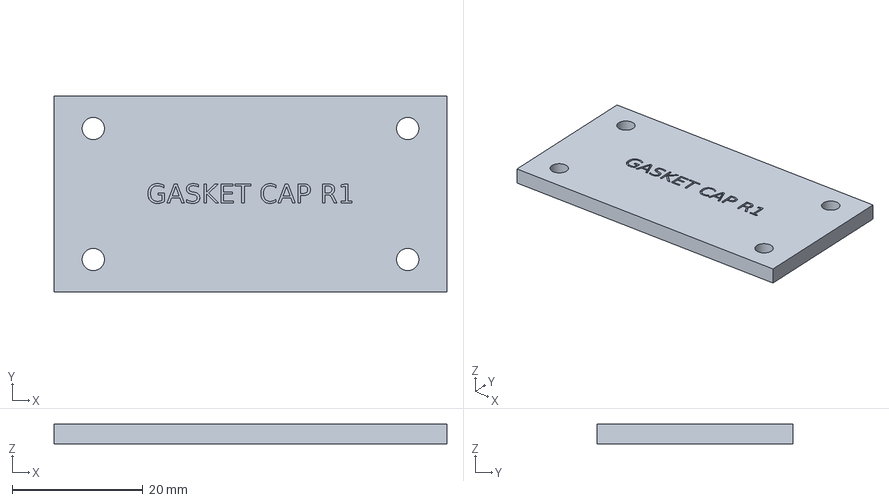
[picture p126: CAD file, 2026-08-10]
release/Satellite1-Ultra-RC1/ADVANCED/3MF/coupon_gasket_cap.3mf
60.0 x 30.0 x 3.00 mm
