BigPappy098/Satellite1-Ultra/release/Satellite1-Ultra-RC1/ADVANCED/STEP/passive_radiator_clamp_ring.step

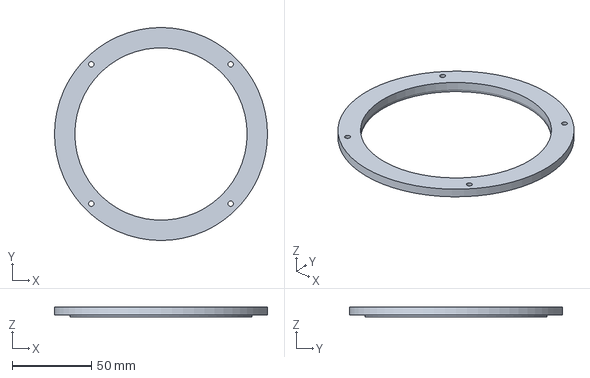
[picture p127: CAD file, 2026-08-10]
release/Satellite1-Ultra-RC1/ADVANCED/STEP/passive_radiator_clamp_ring.step
134.0 x 134.0 x 6.00 mm
