BigPappy098/Satellite1-Ultra/reference-assets/official/Satellite1-Enclosures/OEM Enclosures/Satellite1.1 Smart Speaker Enclosure Kit/Sat 1.x Enclosure small - singlematerial (Bambu Studio Projectfile).3mf

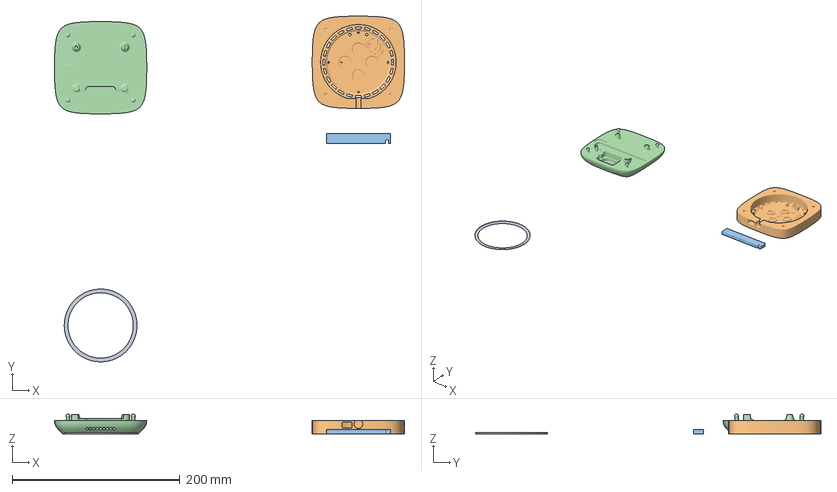
[picture p131: CAD file, 2026-07-28]
reference-assets/official/Satellite1-Enclosures/OEM Enclosures/Satellite1.1 Smart Speaker Enclosure Kit/Sat 1.x Enclosure small - singlematerial (Bambu Studio Projectfile).3mf
417.2 x 412.1 x 23.8 mm
Top - LED diffuser.stl
Top.stl
Screw guide
Squircle Mesh small - Chamber 3525 speaker.step
