BigPappy098/Satellite1-Ultra/release/Satellite1-Ultra-RC1/3_ENCLOSURE_PARTS/09_MIC_ISOLATORS_TPU_PRINT_FOUR.3mf

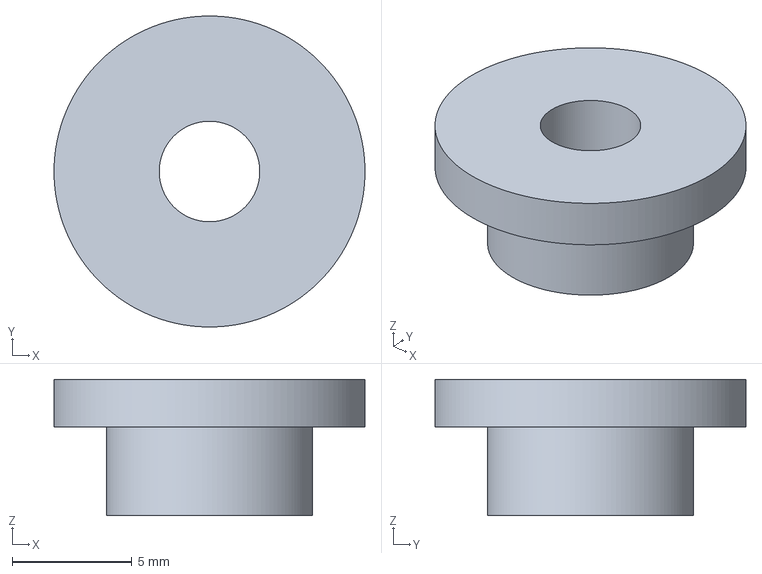
[picture p132: CAD file, 2026-08-10]
release/Satellite1-Ultra-RC1/3_ENCLOSURE_PARTS/09_MIC_ISOLATORS_TPU_PRINT_FOUR.3mf
13.0 x 13.0 x 5.70 mm
