BigPappy098/Satellite1-Ultra/reference-assets/official/Satellite1-Enclosures/DIY Enclosures/Cylindrical Enclosures/Geometry Files/STEP/General Parts/(Optional) Dev Kit UFO Base for No Speaker.step

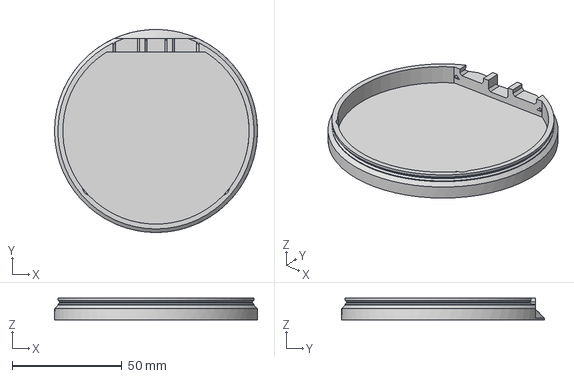
[picture p133: CAD file, 2026-07-28]
reference-assets/official/Satellite1-Enclosures/DIY Enclosures/Cylindrical Enclosures/Geometry Files/STEP/General Parts/(Optional) Dev Kit UFO Base for No Speaker.step
92.4 x 92.4 x 9.80 mm
