BigPappy098/Satellite1-Ultra/reference-assets/official/Satellite1-Enclosures/OEM Enclosures/Satellite1.1 Smart Speaker Enclosure Kit/Sat 1.x Enclosure small - singlematerial (Orca Slicer Projectfile).3mf

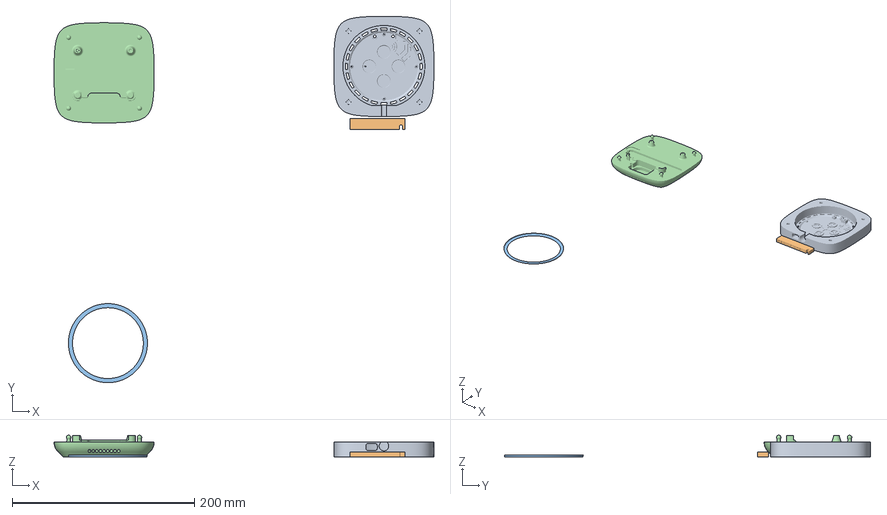
[picture p135: CAD file, 2026-07-28]
reference-assets/official/Satellite1-Enclosures/OEM Enclosures/Satellite1.1 Smart Speaker Enclosure Kit/Sat 1.x Enclosure small - singlematerial (Orca Slicer Projectfile).3mf
417.2 x 402.1 x 23.8 mm
Sat1.x - Top Plate single material.stl
Sat1.x - Screwing guide.stl
Sat1.x - Top Plate single material - LED Diffuser.stl
Sat1.x small - Chamber with 3525 speaker.step
