BigPappy098/Satellite1-Ultra/release/Satellite1-Ultra-RC1/3_ENCLOSURE_PARTS/06_WEIGHT_TRAY.3mf

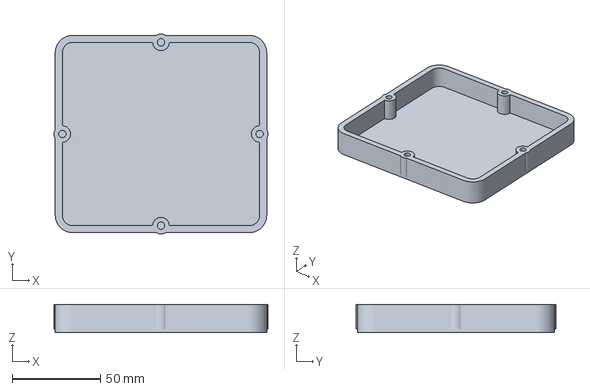
[picture p136: CAD file, 2026-08-10]
release/Satellite1-Ultra-RC1/3_ENCLOSURE_PARTS/06_WEIGHT_TRAY.3mf
121.4 x 113.4 x 16.0 mm
