BigPappy098/Satellite1-Ultra/reference-assets/official/Satellite1-Enclosures/OEM Enclosures/Satellite1.1 Smart Speaker Enclosure Kit/Sat 1.x Enclosure large - singlematerial (Bambu Studio Projectfile).3mf

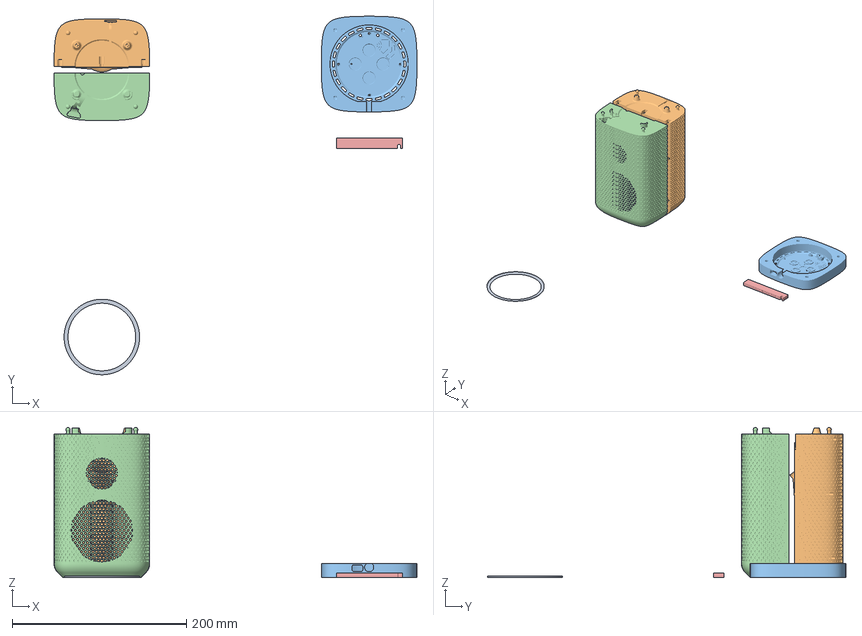
[picture p142: CAD file, 2026-07-28]
reference-assets/official/Satellite1-Enclosures/OEM Enclosures/Satellite1.1 Smart Speaker Enclosure Kit/Sat 1.x Enclosure large - singlematerial (Bambu Studio Projectfile).3mf
417.2 x 412.1 x 172.5 mm
Top - LED diffuser.stl
Chamber back - Wifi pocket + Bass port.stl
Top.stl
Chamber front - FPH Woofer +Tweeter + LD2450 pocket.stl
Screw guide
