BigPappy098/Satellite1-Ultra/release/Satellite1-Ultra-RC1/ADVANCED/IMAGES/assembly_stage_06_ballast.png

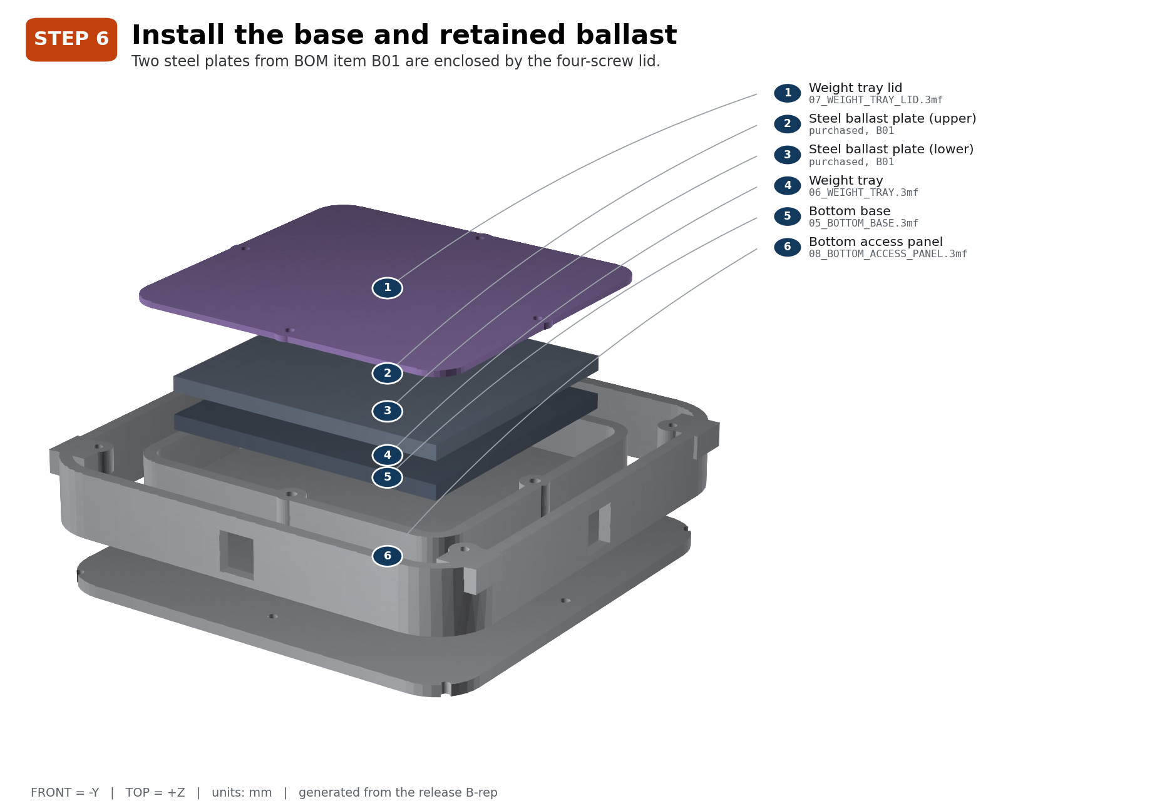
release/Satellite1-Ultra-RC1/ADVANCED/IMAGES/assembly_stage_06_ballast.png
