BigPappy098/Satellite1-Ultra/release/Satellite1-Ultra-RC1/ADVANCED/IMAGES/assembly_top_exploded.png

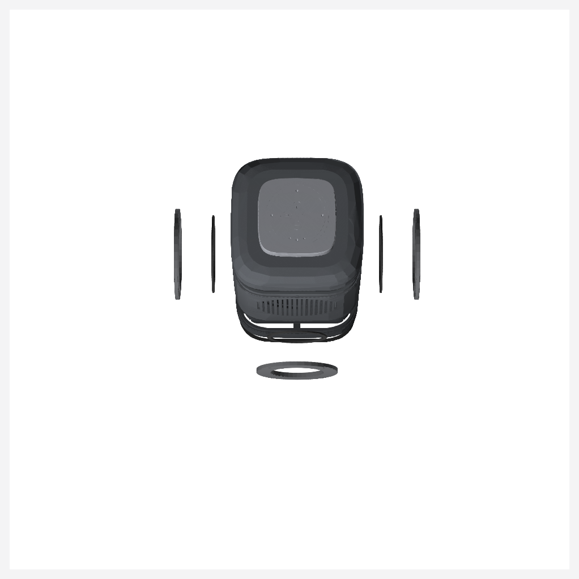
release/Satellite1-Ultra-RC1/ADVANCED/IMAGES/assembly_top_exploded.png
