BigPappy098/Satellite1-Ultra/release/Satellite1-Ultra-RC1/ADVANCED/IMAGES/print_orientation_active_driver_clamp_ring.png

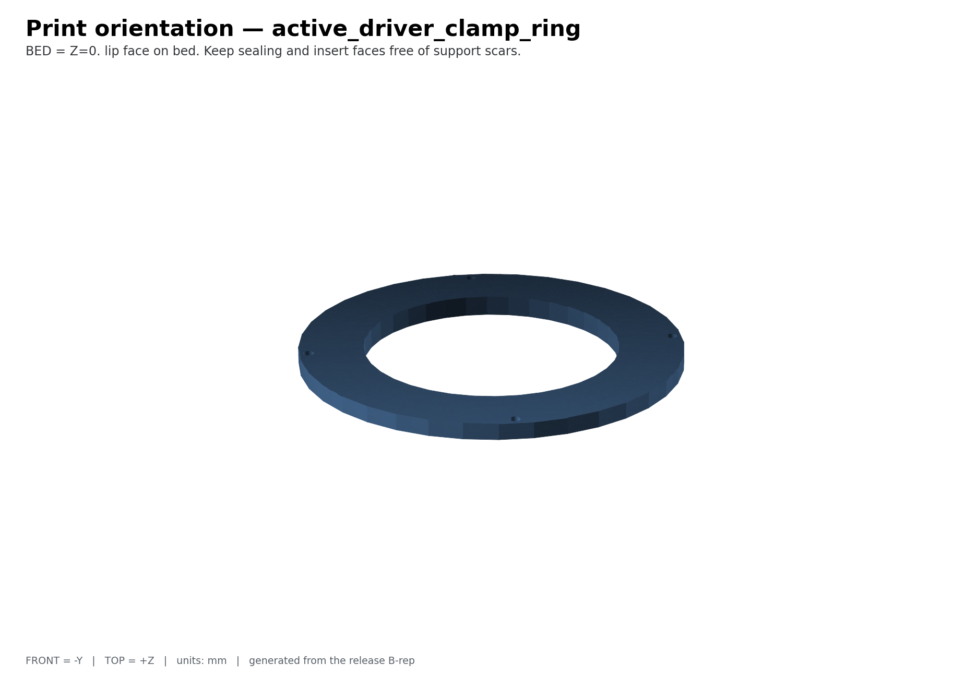
release/Satellite1-Ultra-RC1/ADVANCED/IMAGES/print_orientation_active_driver_clamp_ring.png
