BigPappy098/Satellite1-Ultra/release/Satellite1-Ultra-RC1/ADVANCED/IMAGES/print_orientation_cable_gland.png

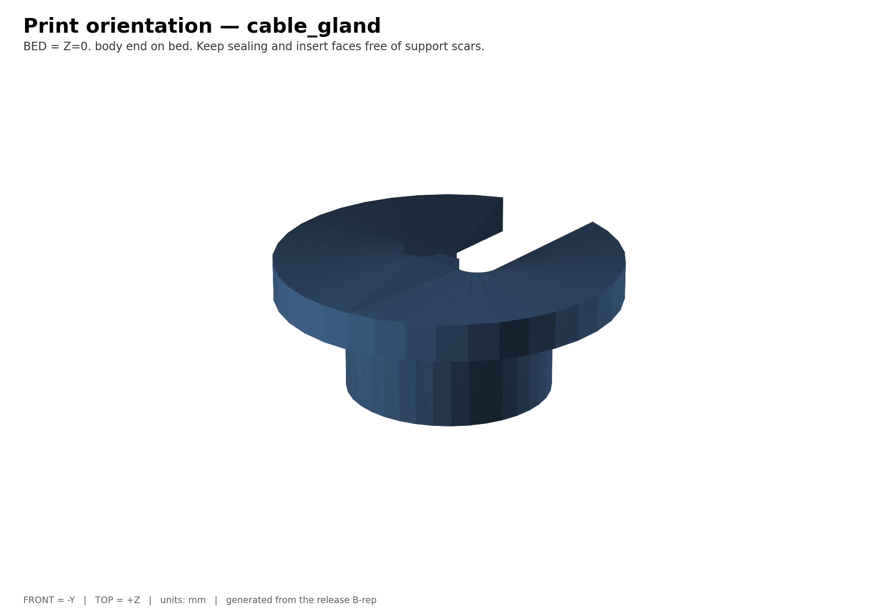
release/Satellite1-Ultra-RC1/ADVANCED/IMAGES/print_orientation_cable_gland.png
