BigPappy098/Satellite1-Ultra/release/Satellite1-Ultra-RC1/ADVANCED/IMAGES/print_orientation_coupon_gasket_base.png

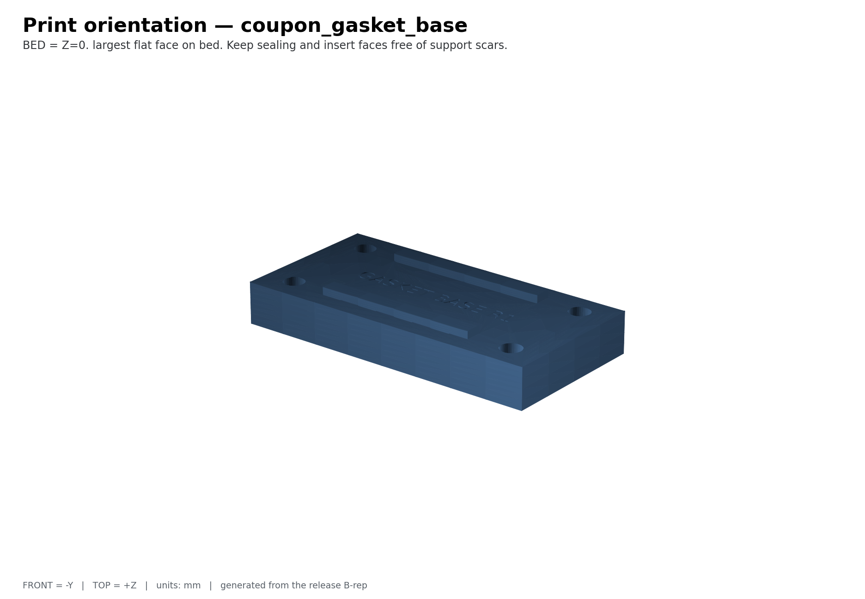
release/Satellite1-Ultra-RC1/ADVANCED/IMAGES/print_orientation_coupon_gasket_base.png
