BigPappy098/Satellite1-Ultra/release/Satellite1-Ultra-RC1/ADVANCED/IMAGES/print_orientation_official_top_plate_mm_buttons.png

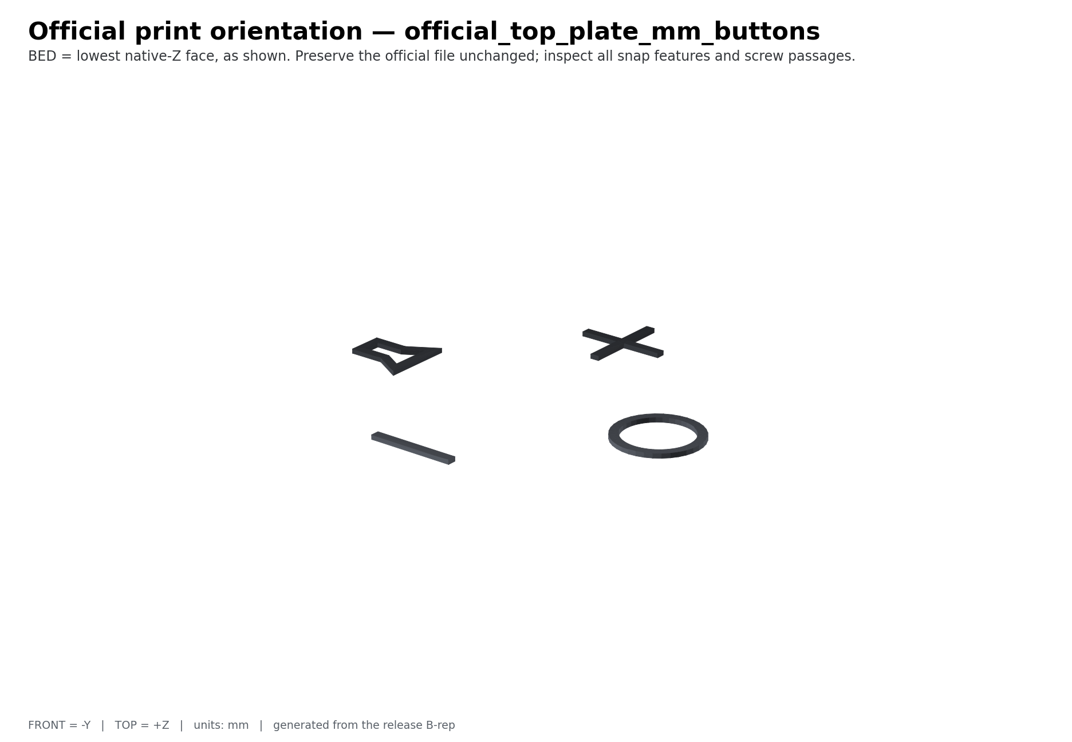
release/Satellite1-Ultra-RC1/ADVANCED/IMAGES/print_orientation_official_top_plate_mm_buttons.png
