BigPappy098/Satellite1-Ultra/release/Satellite1-Ultra-RC1/ADVANCED/IMAGES/service_disassembly.png

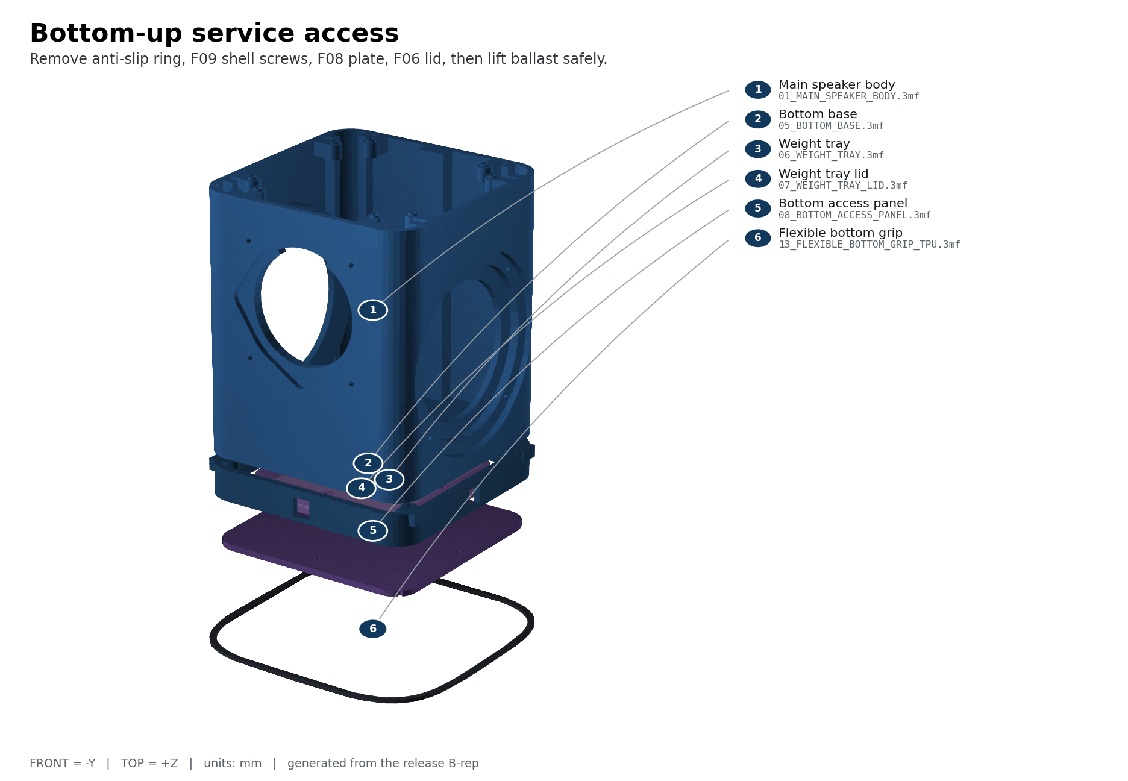
release/Satellite1-Ultra-RC1/ADVANCED/IMAGES/service_disassembly.png
