BigPappy098/Satellite1-Ultra/reports/renders/print_orientation_anti_slip_ring.png

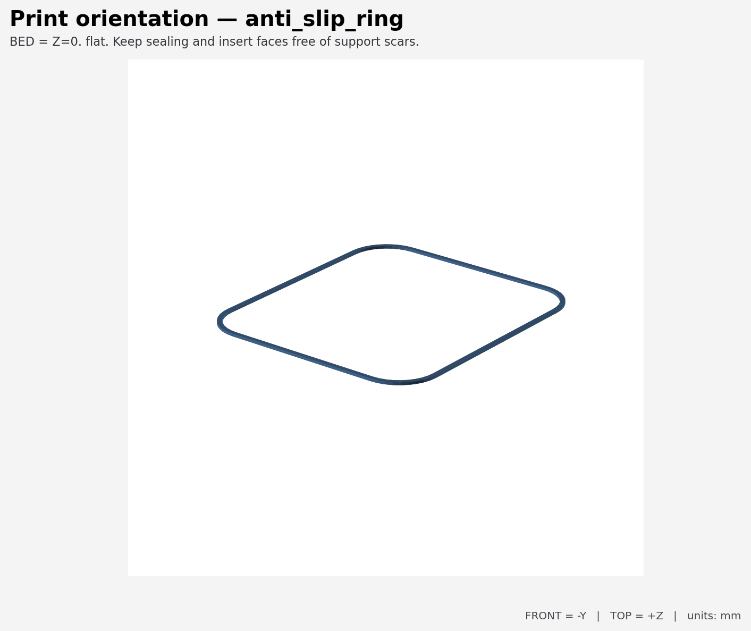
reports/renders/print_orientation_anti_slip_ring.png
