BigPappy098/Satellite1-Ultra/reports/renders/print_orientation_ballast_cartridge.png

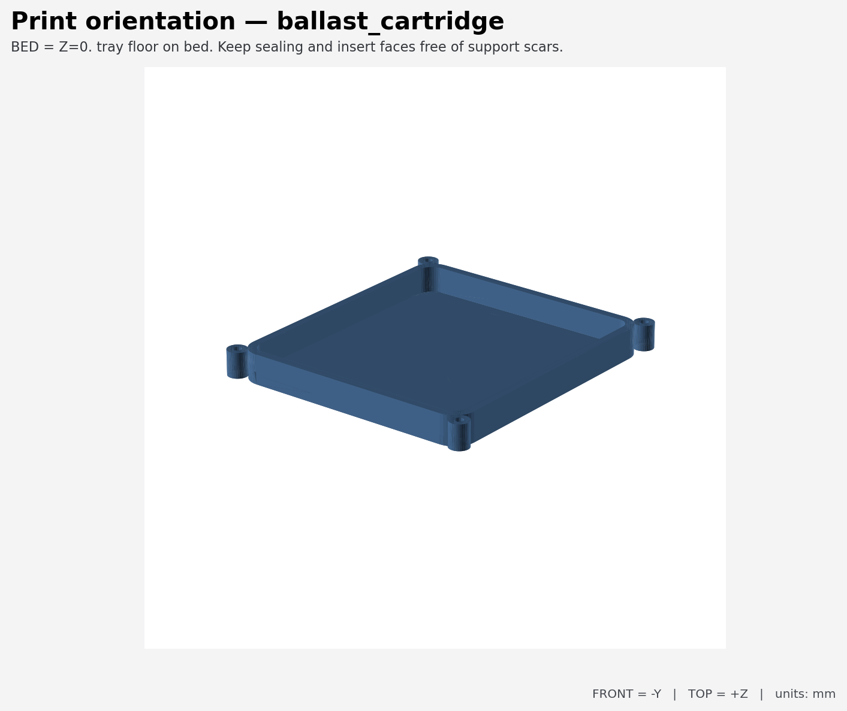
reports/renders/print_orientation_ballast_cartridge.png
