BigPappy098/Satellite1-Ultra/reports/renders/print_orientation_base_skirt.png

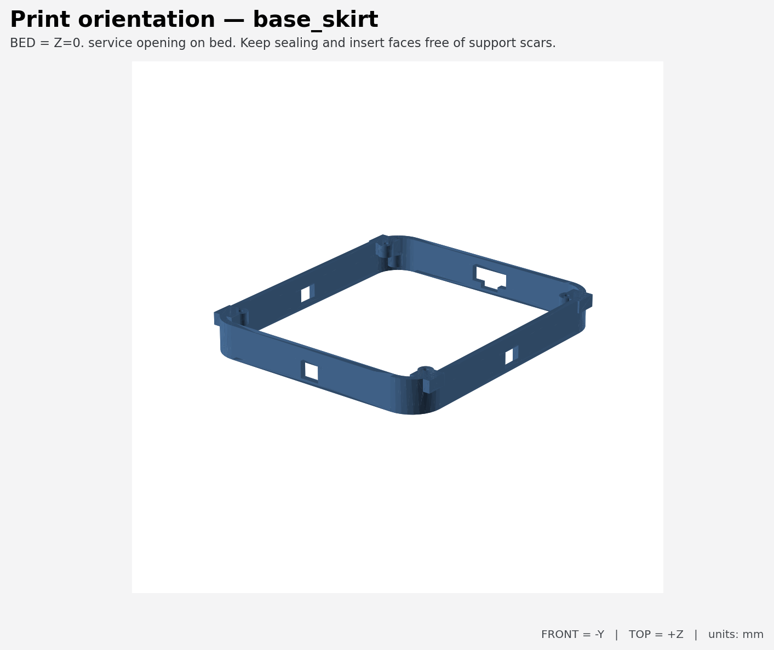
reports/renders/print_orientation_base_skirt.png
