BigPappy098/Satellite1-Ultra/reports/renders/print_orientation_bottom_service_plate.png

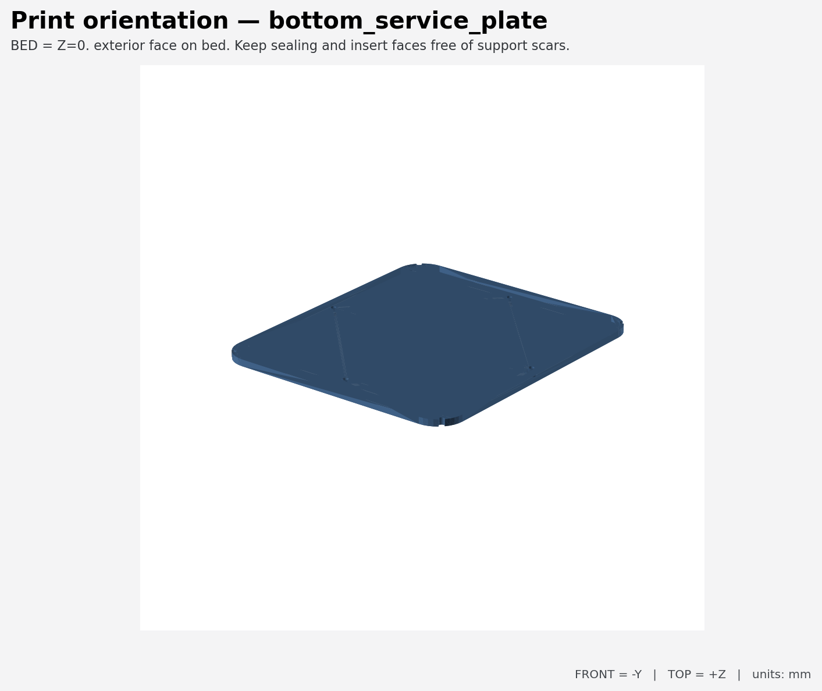
reports/renders/print_orientation_bottom_service_plate.png
