BigPappy098/Satellite1-Ultra/reports/renders/print_orientation_cable_gland.png

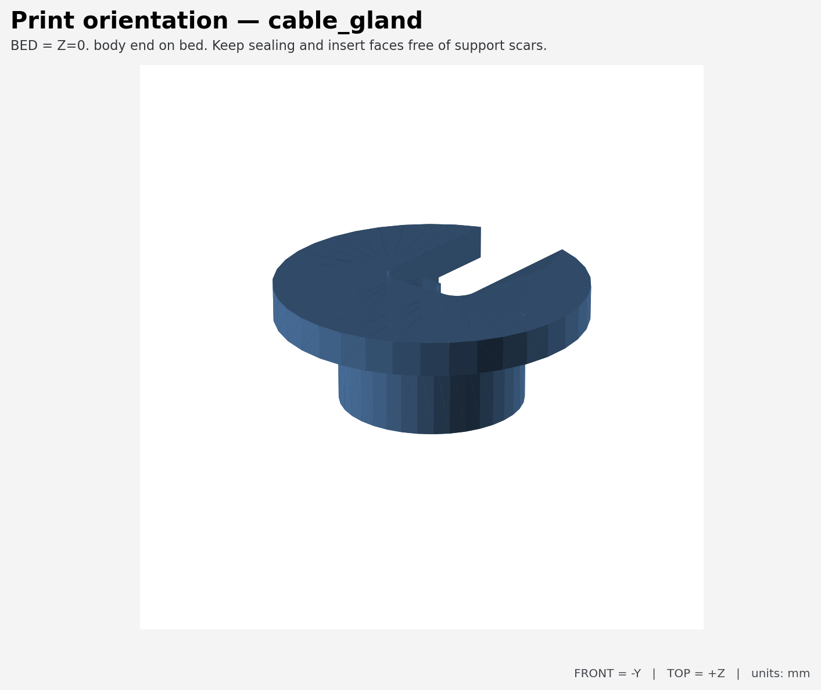
reports/renders/print_orientation_cable_gland.png
