BigPappy098/Satellite1-Ultra/reports/renders/print_orientation_coupon_gasket_base.png

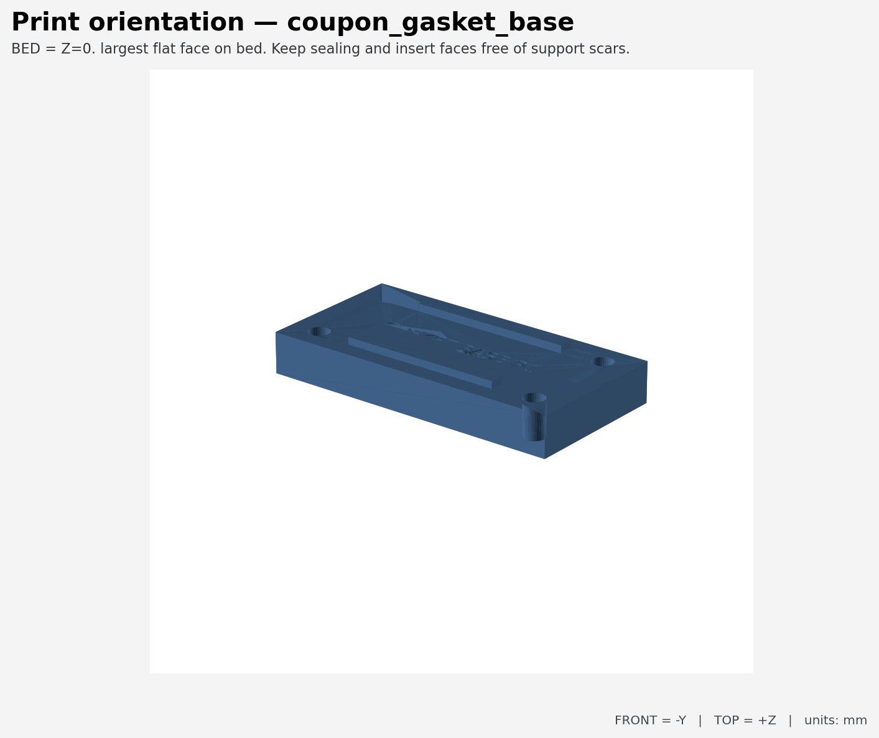
reports/renders/print_orientation_coupon_gasket_base.png
