BigPappy098/Satellite1-Ultra/reports/renders/print_orientation_coupon_heat_set_insert.png

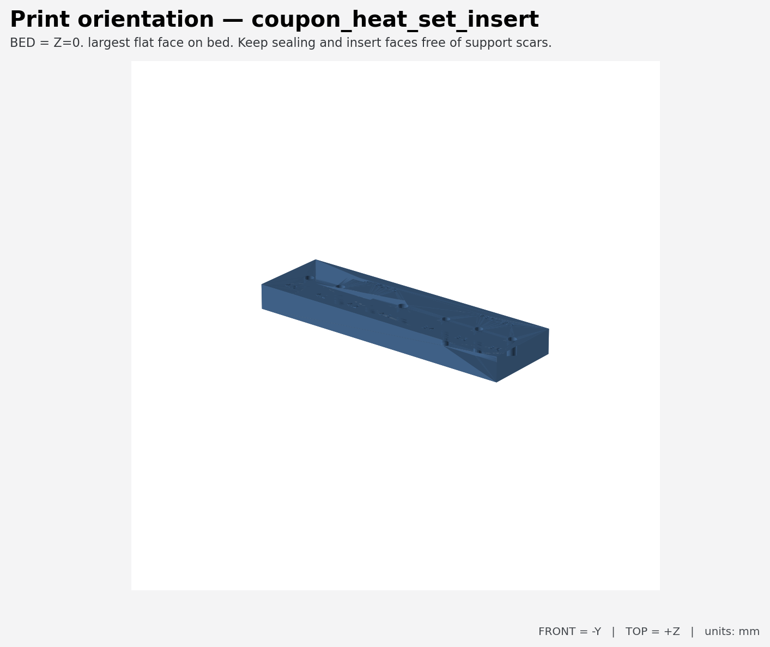
reports/renders/print_orientation_coupon_heat_set_insert.png
