BigPappy098/Satellite1-Ultra/reports/renders/print_orientation_leak_test_adapter.png

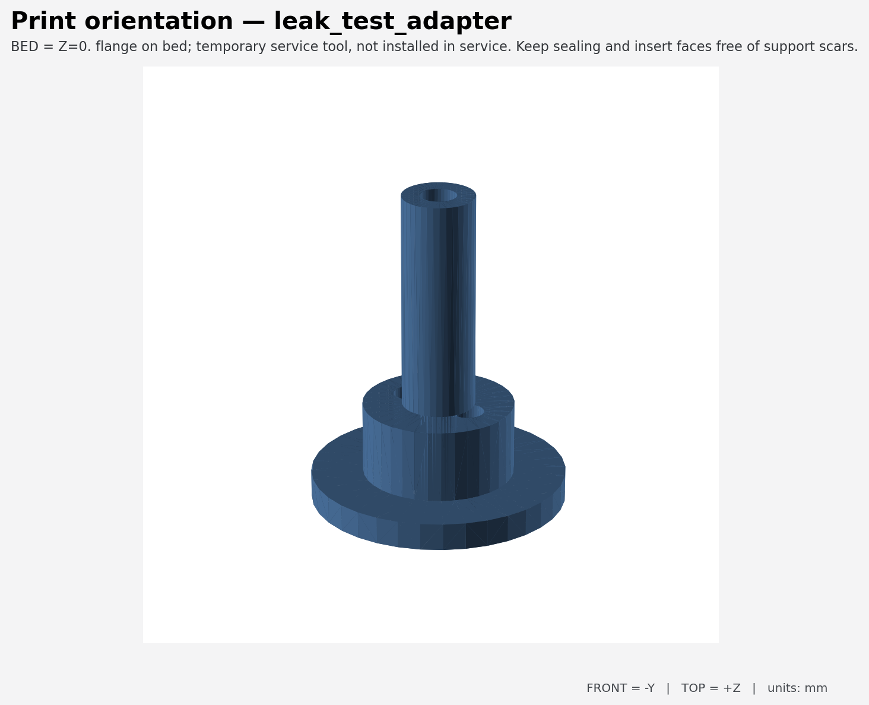
reports/renders/print_orientation_leak_test_adapter.png
