BigPappy098/Satellite1-Ultra/reports/renders/print_orientation_official_lock_ring.png

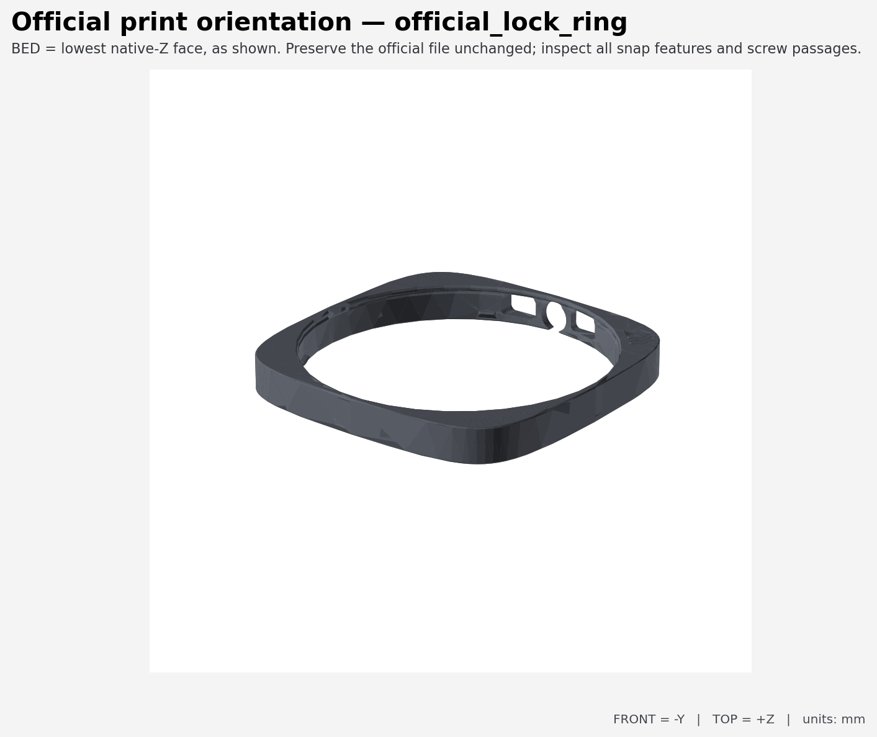
reports/renders/print_orientation_official_lock_ring.png
