BigPappy098/Satellite1-Ultra/reports/renders/print_orientation_official_mid_plate.png

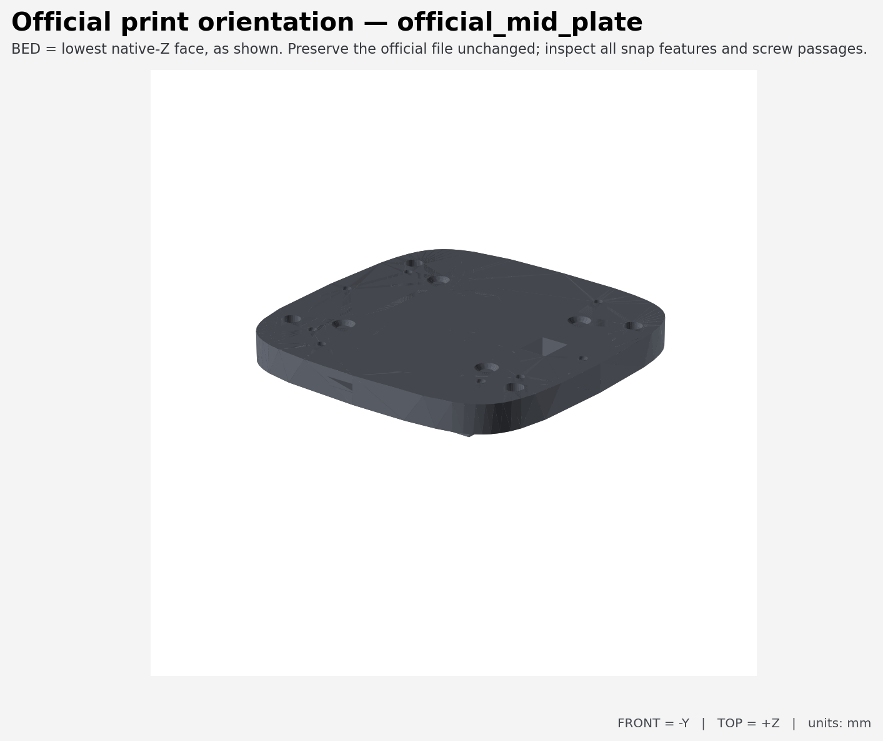
reports/renders/print_orientation_official_mid_plate.png
