BigPappy098/Satellite1-Ultra/reports/renders/print_orientation_official_top_plate_mm_buttons.png

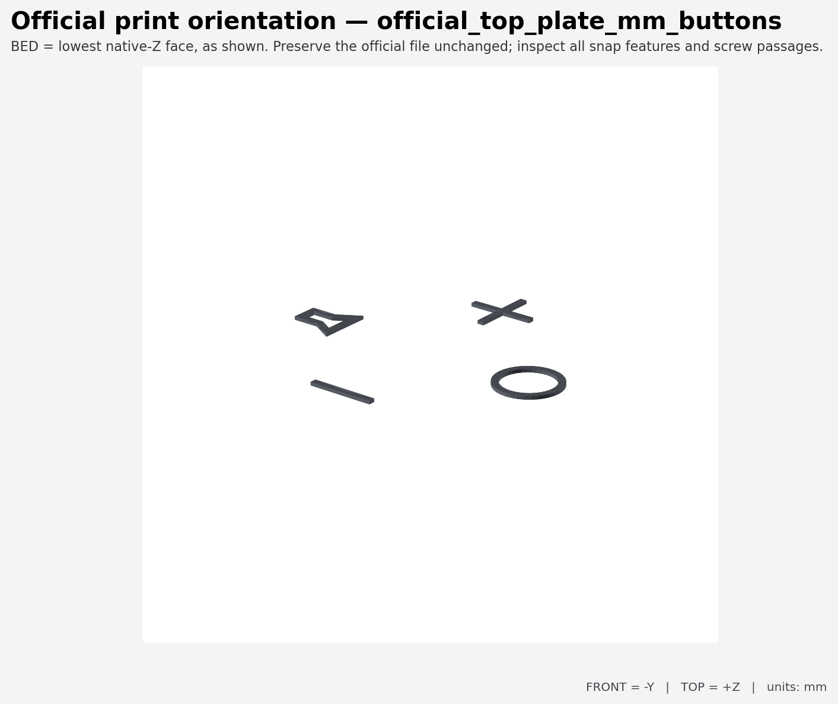
reports/renders/print_orientation_official_top_plate_mm_buttons.png
