BigPappy098/Satellite1-Ultra/reports/renders/print_orientation_official_top_plate_snap_in_diffuser_ring.png

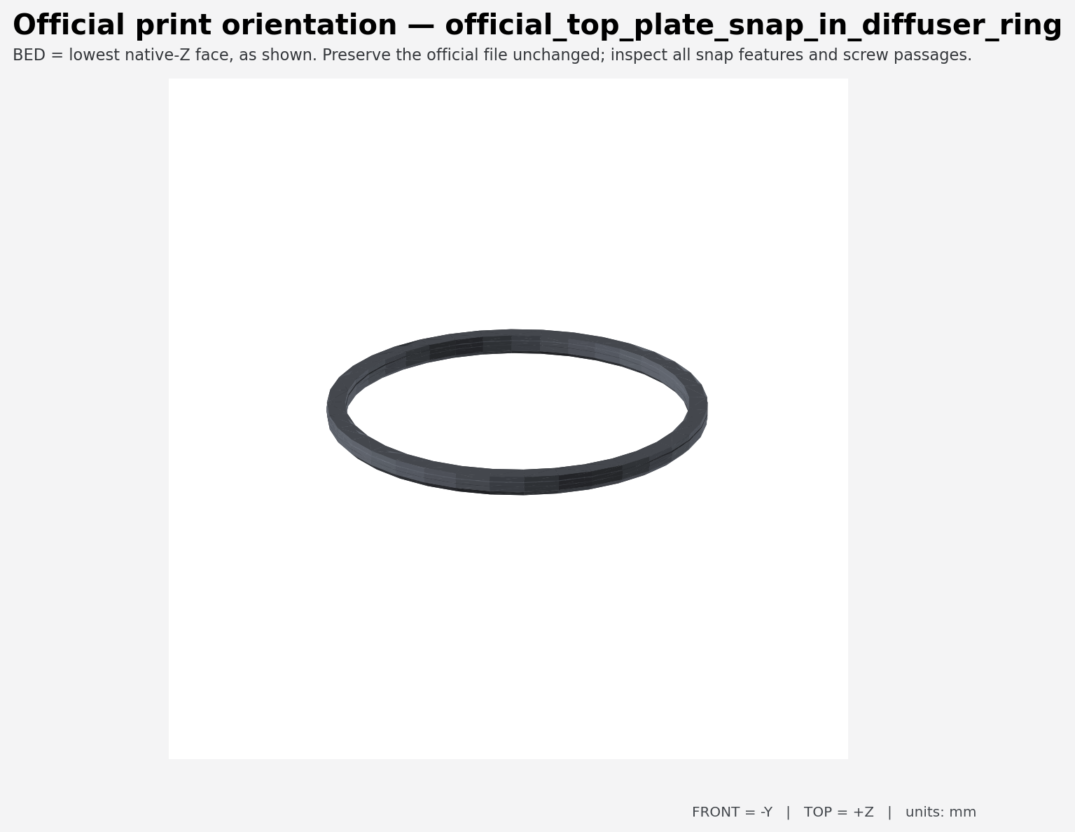
reports/renders/print_orientation_official_top_plate_snap_in_diffuser_ring.png
