BigPappy098/Satellite1-Ultra/reports/renders/print_orientation_pressure_divider.png

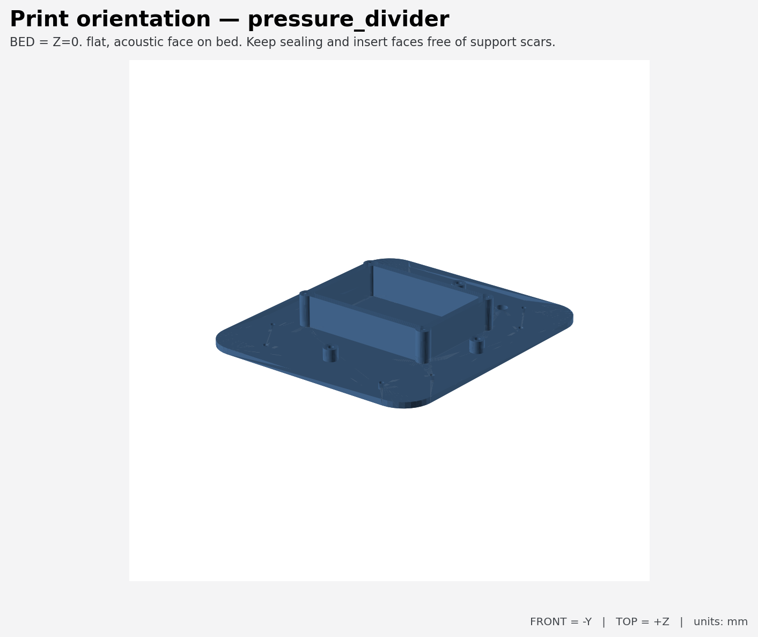
reports/renders/print_orientation_pressure_divider.png
