BigPappy098/Satellite1-Ultra/reports/drawings/leak_test_adapter.pdf

# Satellite1 Ultra — leak_test_adapter

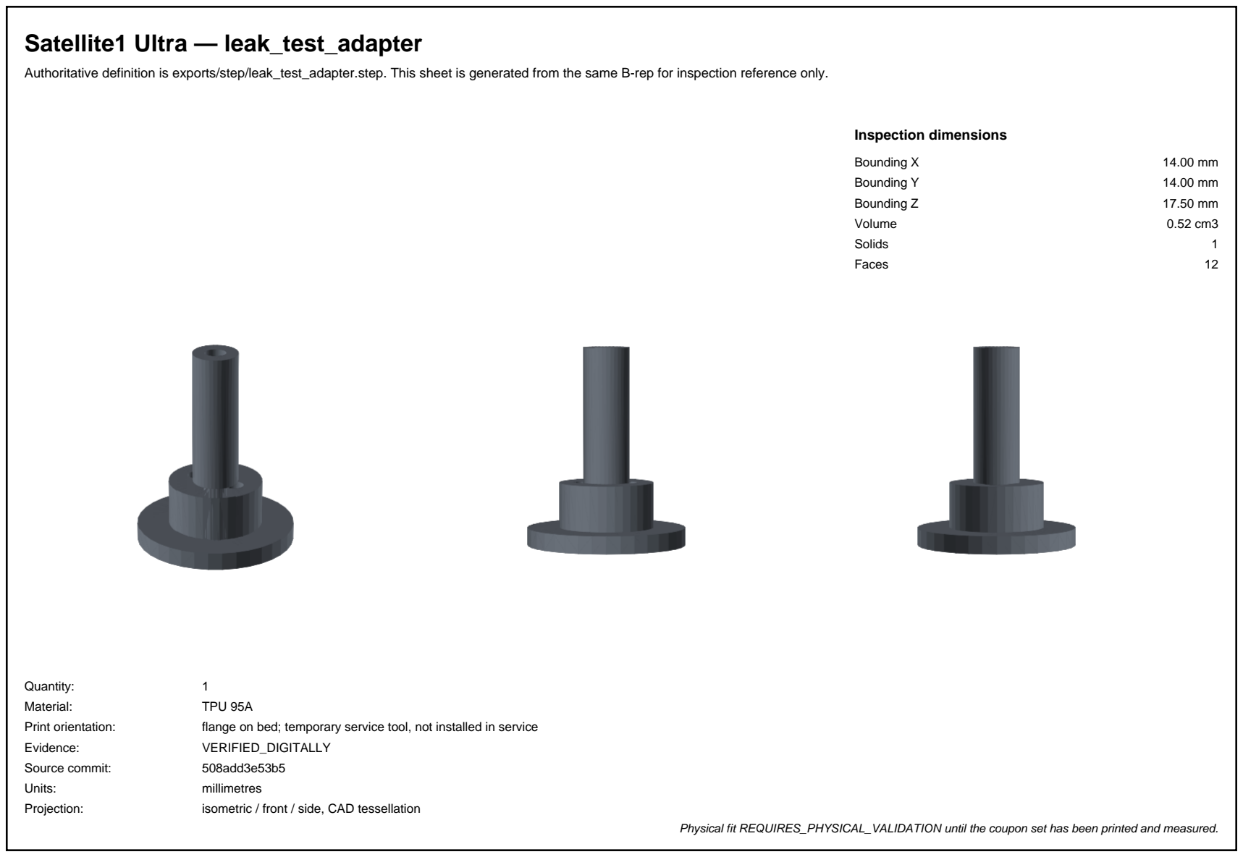
[picture p217: page 1]

Authoritative definition is exports/step/leak_test_adapter.step. This sheet is generated from the same B-rep for inspection reference only.

Inspection dimensions

Bounding X | 14.00 mm
Bounding Y | 14.00 mm
Bounding Z | 17.50 mm
Volume | 0.52 cm3
Solids | 1
Faces | 12
Quantity: | 1
Material: | TPU 95A
Print orientation: | flange on bed; temporary service tool, not installed in service
Evidence: | VERIFIED_DIGITALLY
Source commit: | 508add3e53b5
Units: | millimetres
Projection: | isometric / front / side, CAD tessellation
Physical fit REQUIRES_PHYSICAL_VALIDATION until the coupon set has been printed and measured.
