BigPappy098/Satellite1-Ultra/release/Satellite1-Ultra-RC1/ADVANCED/IMAGES/calibration_driver.png

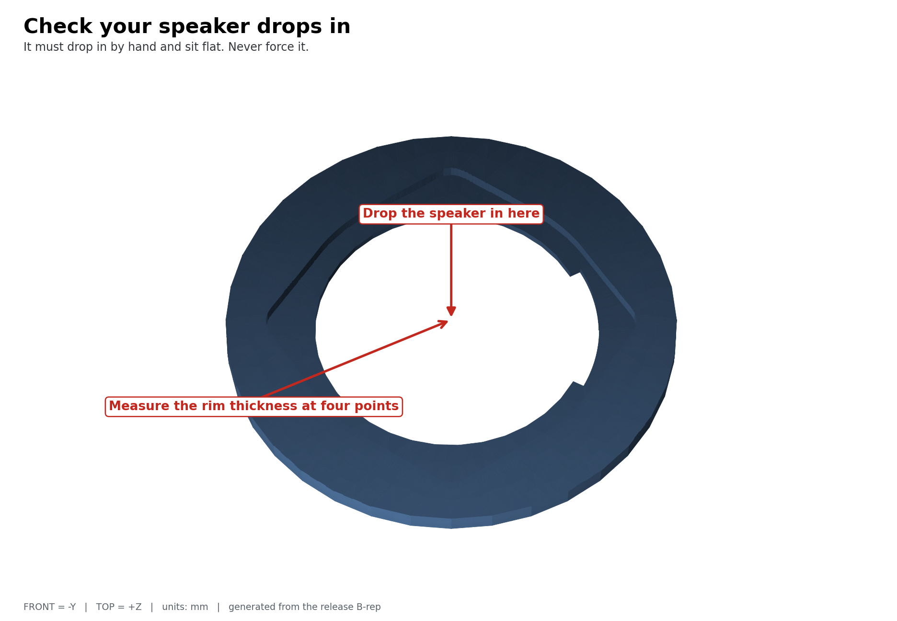
release/Satellite1-Ultra-RC1/ADVANCED/IMAGES/calibration_driver.png
