BigPappy098/Satellite1-Ultra/reports/drawings/views/leak_test_adapter_front.png

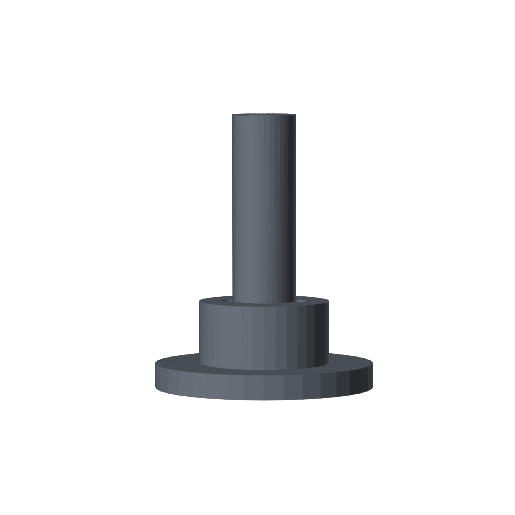
reports/drawings/views/leak_test_adapter_front.png
