BigPappy098/Satellite1-Ultra/reports/renders/calibration_cable.png

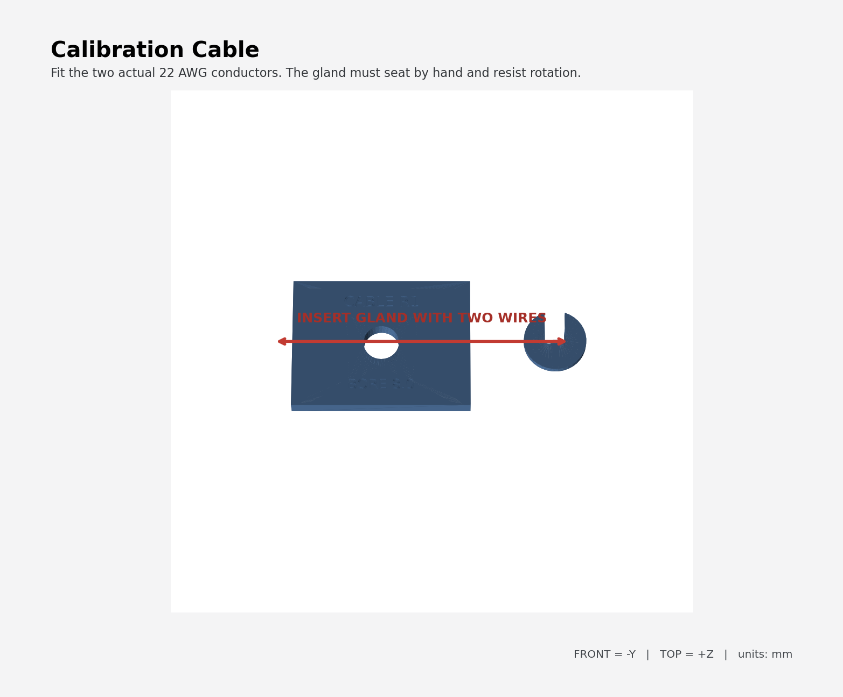
reports/renders/calibration_cable.png
