BigPappy098/Satellite1-Ultra/reports/renders/calibration_fasteners.png

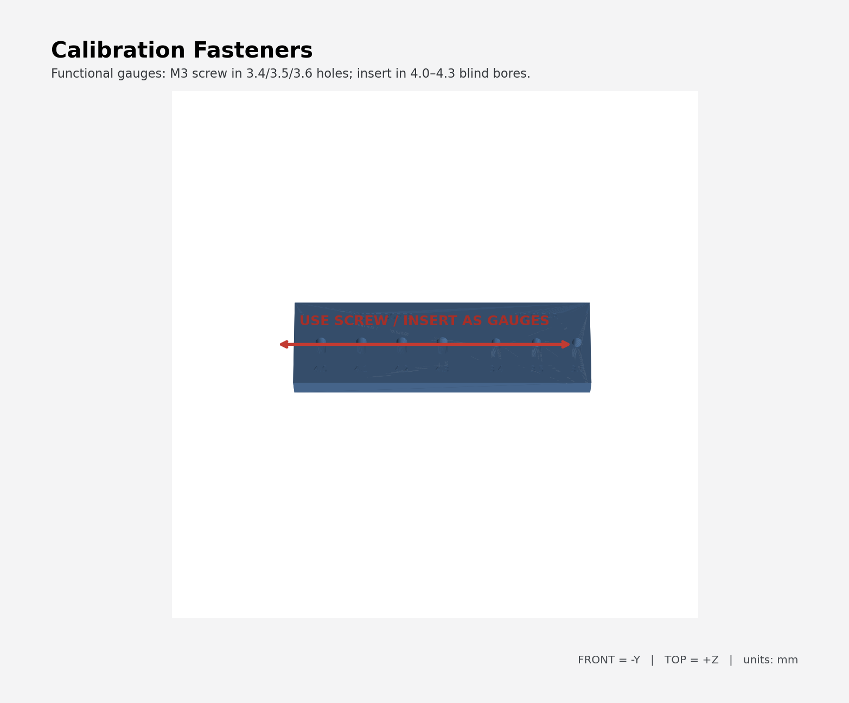
reports/renders/calibration_fasteners.png
