BigPappy098/Satellite1-Ultra/reports/renders/calibration_gasket.png

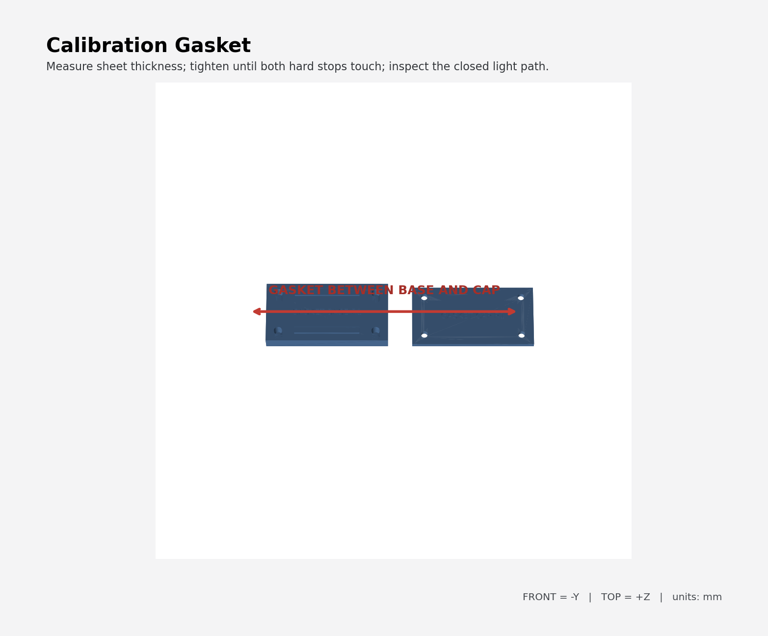
reports/renders/calibration_gasket.png
