BigPappy098/Satellite1-Ultra/reports/renders/calibration_official_interface.png

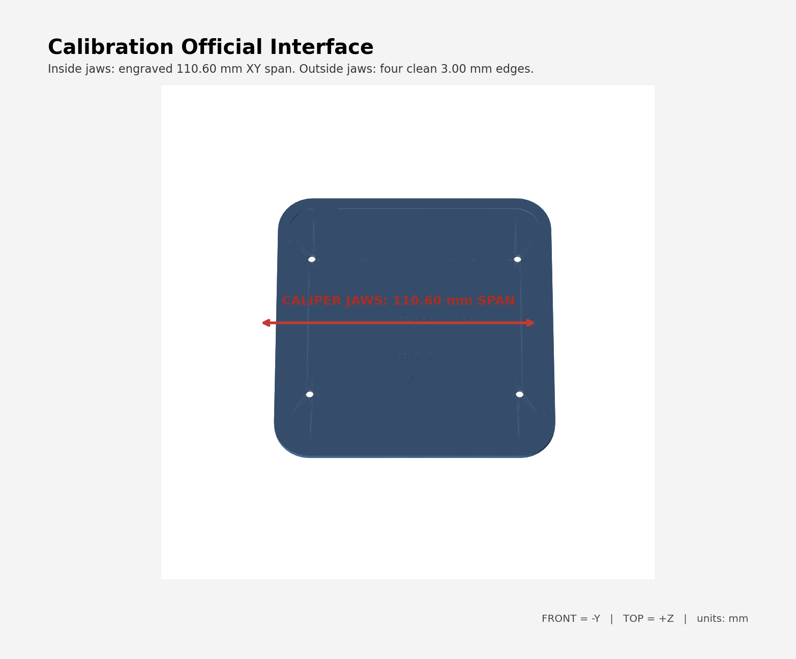
reports/renders/calibration_official_interface.png
